rmfharvey/EE4951_REPO/Documentation/Firmware Algorithms/ADC Trigger.PNG

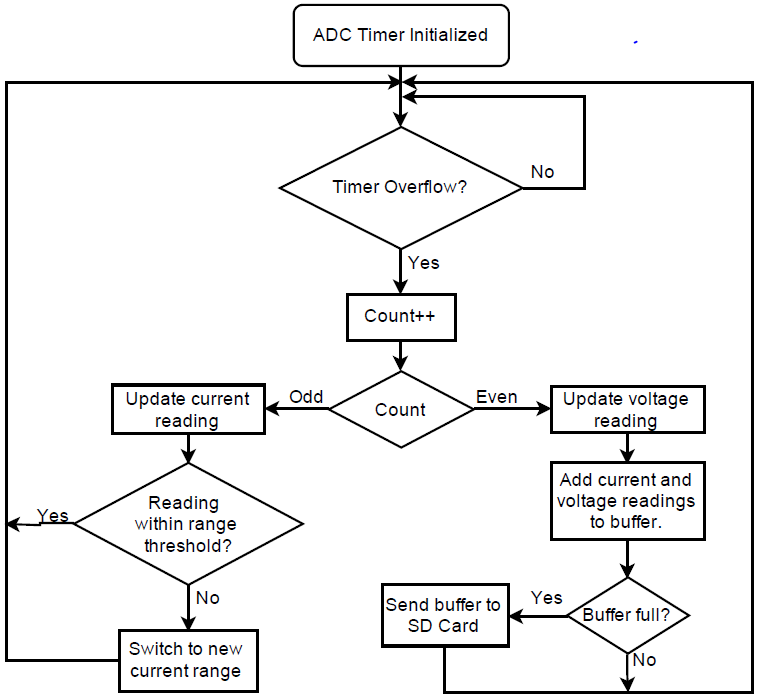
Documentation/Firmware Algorithms/ADC Trigger.PNG
