rmfharvey/EE4951_REPO/Documentation/Nimbelink Device Power Profile/Skywire Online Demo.png

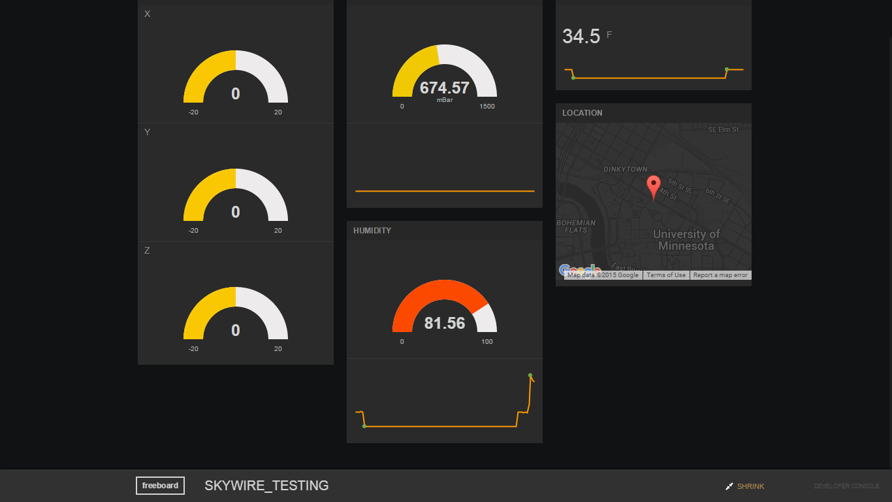
Documentation/Nimbelink Device Power Profile/Skywire Online Demo.png
