rmfharvey/EE4951_REPO/Documentation/Skywire Scope Shots/Constant Transmission.png

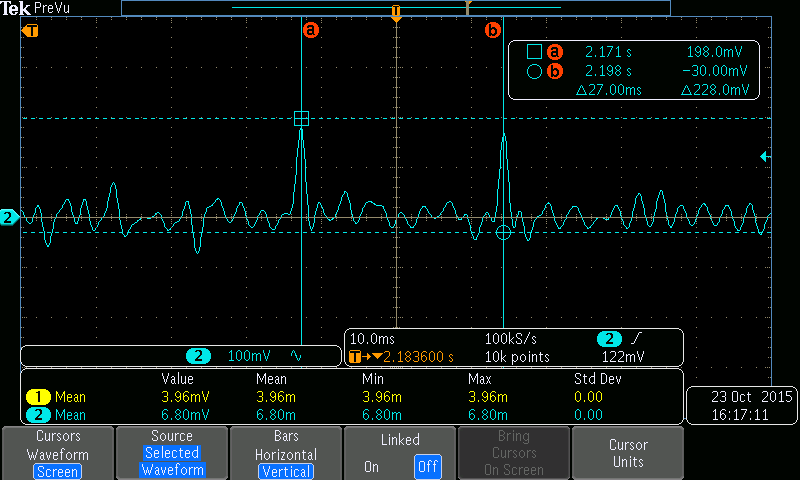
Documentation/Skywire Scope Shots/Constant Transmission.png
