rmfharvey/EE4951_REPO/Documentation/Skywire Scope Shots/Transmission Length.png

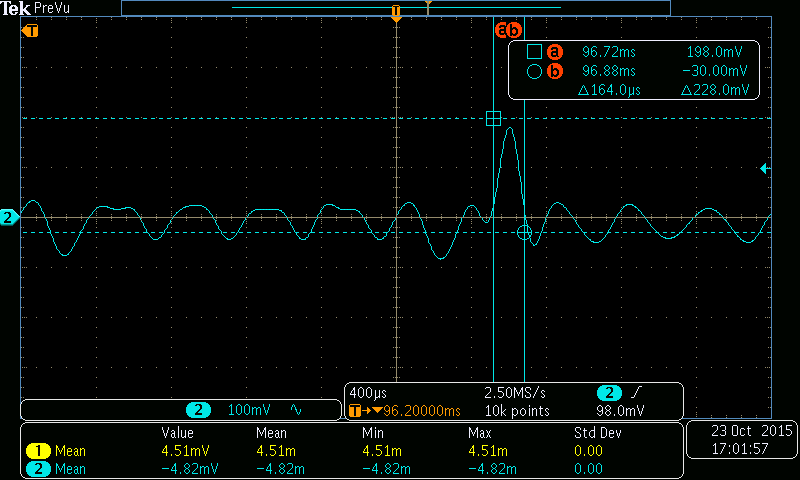
Documentation/Skywire Scope Shots/Transmission Length.png
