rmfharvey/EE4951_REPO/Simulation/Power Subsystem/Converter Selection Controls Simulation/Simulation Output/Charge Pump Auto Turn_Off.png

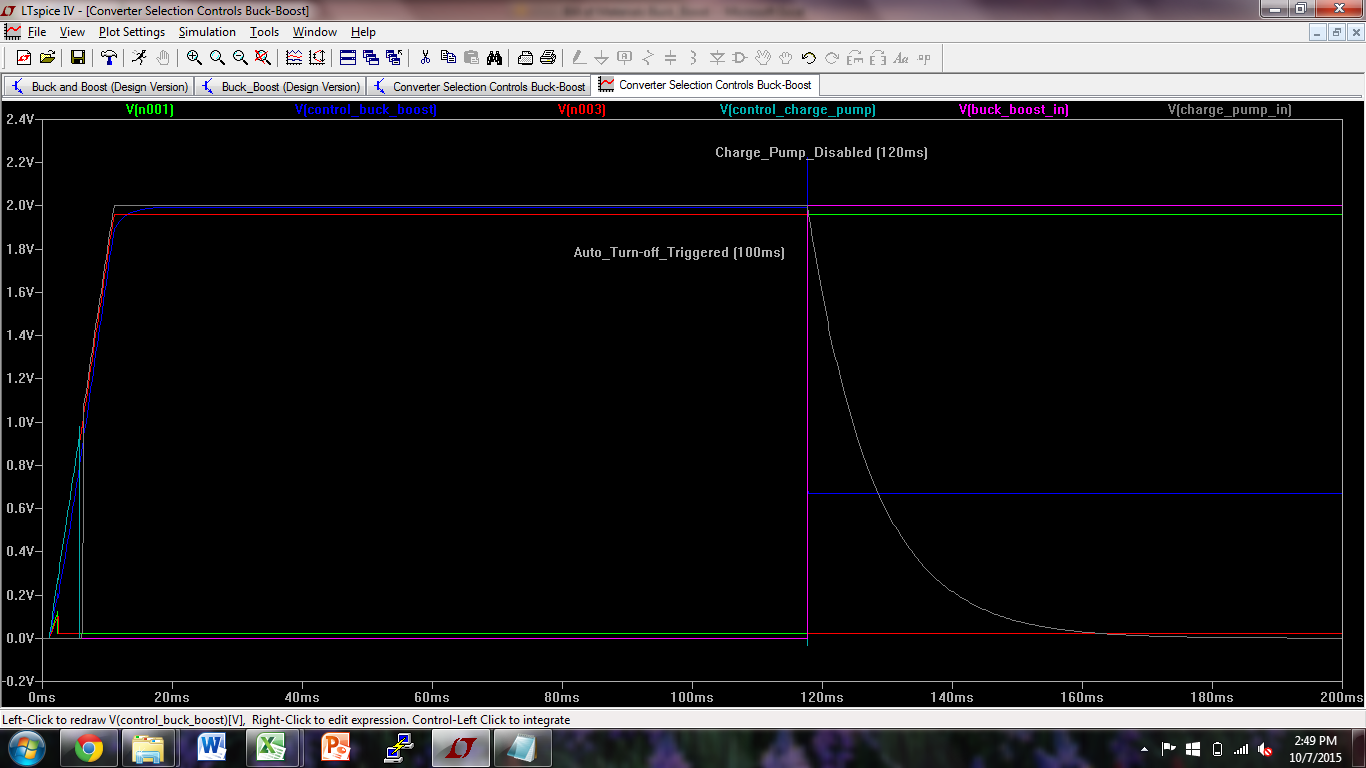
Simulation/Power Subsystem/Converter Selection Controls Simulation/Simulation Output/Charge Pump Auto Turn_Off.png
