rmfharvey/EE4951_REPO/Simulation/Power Subsystem/Converter Selection Controls Simulation/Simulation Output/Comparator and Control Signals.png

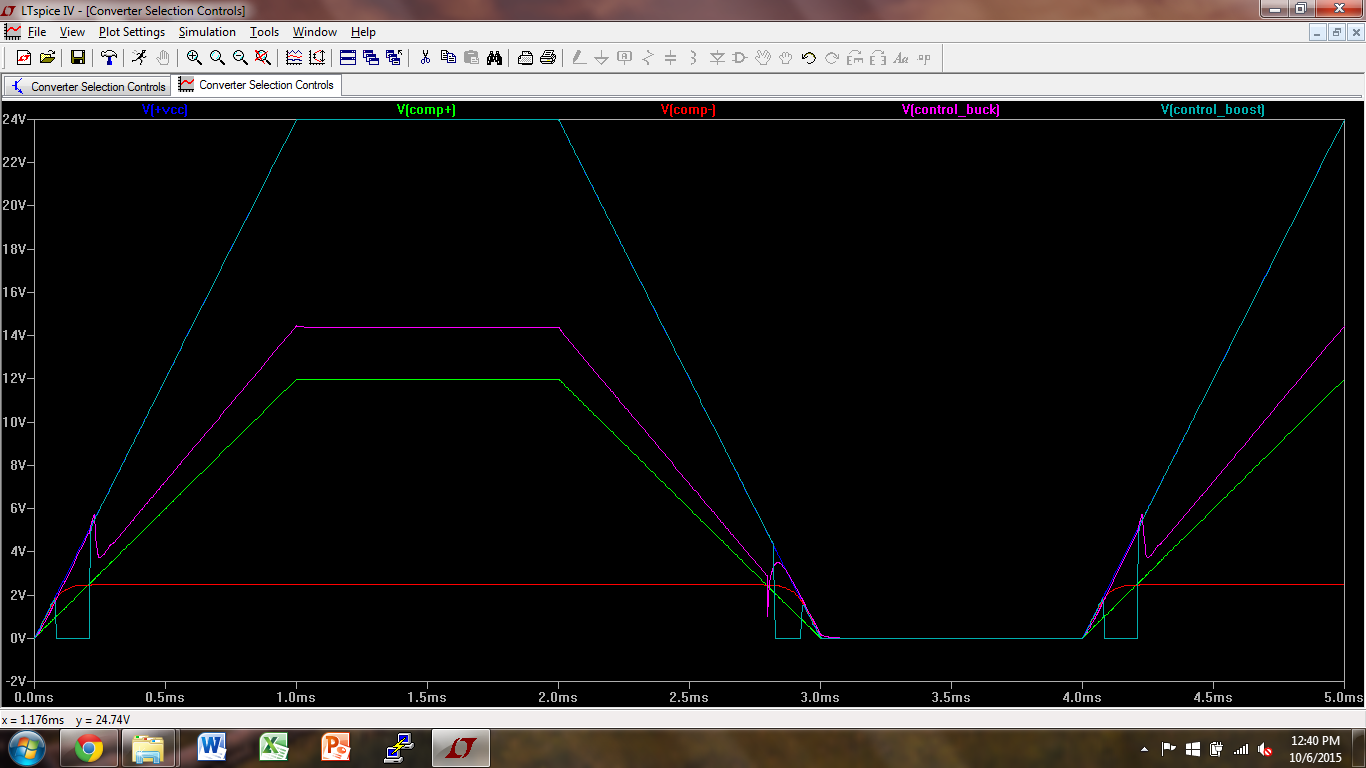
Simulation/Power Subsystem/Converter Selection Controls Simulation/Simulation Output/Comparator and Control Signals.png
