rmfharvey/EE4951_REPO/Simulation/Power Subsystem/Converter Selection Controls Simulation/Simulation Output/Converter Inputs (Assuming 10uF filter caps).png

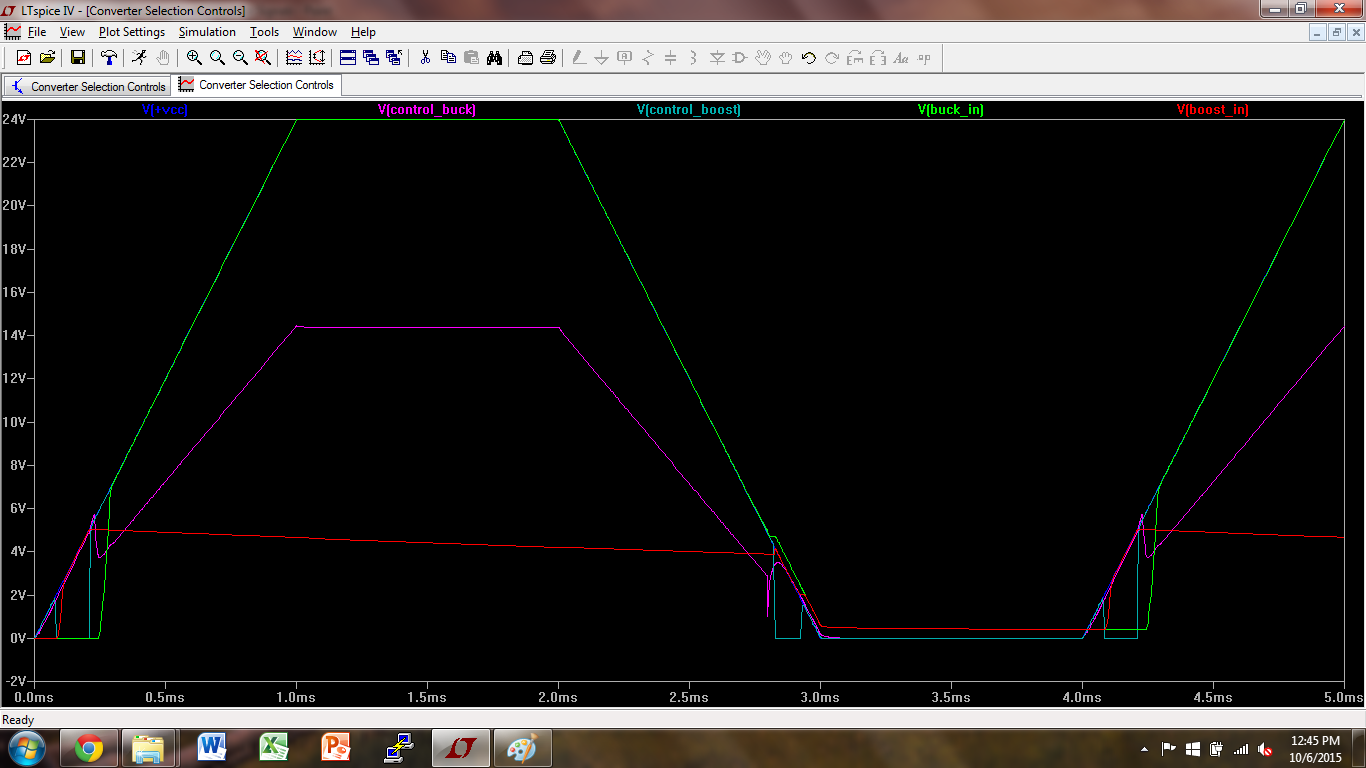
Simulation/Power Subsystem/Converter Selection Controls Simulation/Simulation Output/Converter Inputs (Assuming 10uF filter caps).png
