rmfharvey/EE4951_REPO/Simulation/Power Subsystem/Converter Selection Controls Simulation/Simulation Output/Converter Transition 4_4V to 5_6V Input.png

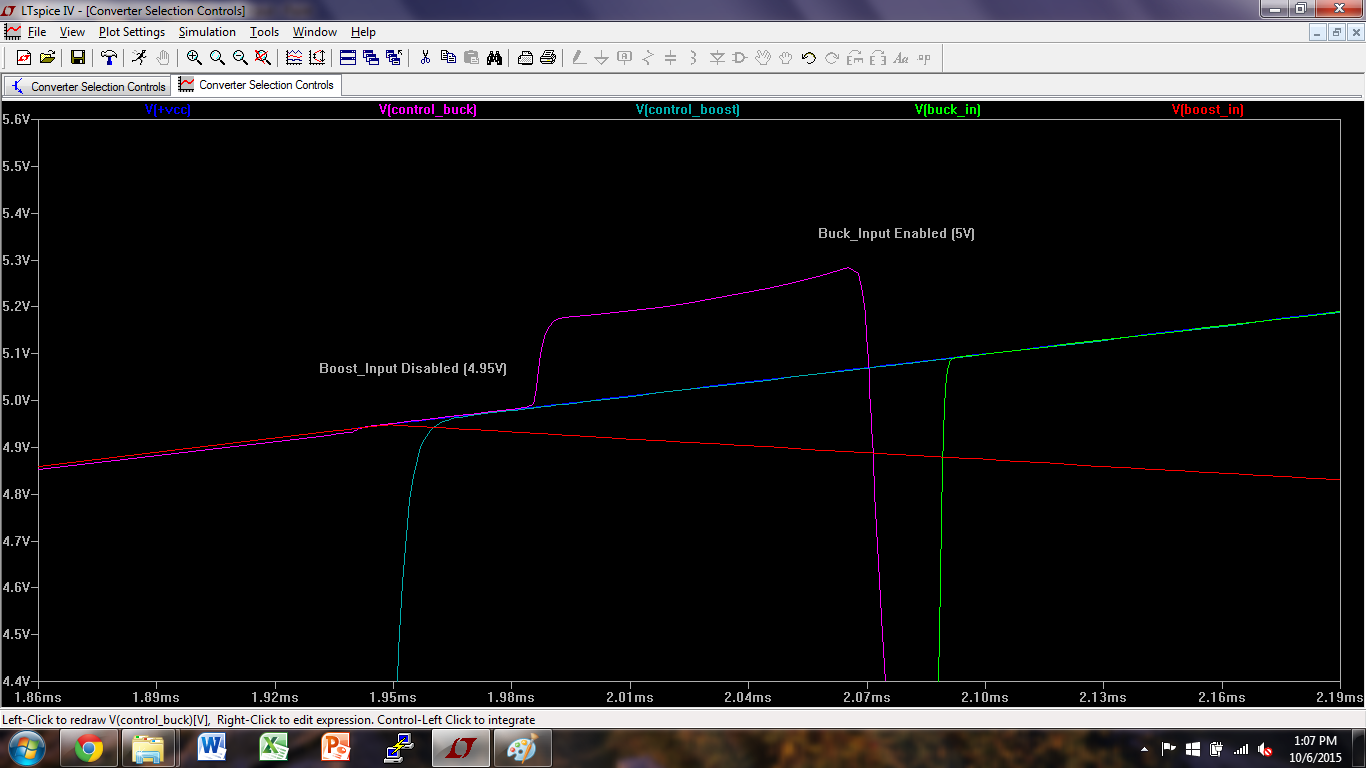
Simulation/Power Subsystem/Converter Selection Controls Simulation/Simulation Output/Converter Transition 4_4V to 5_6V Input.png
