rmfharvey/EE4951_REPO/Simulation/Power Subsystem/USB Autotransfer/Switch USB onto 4_5V.png

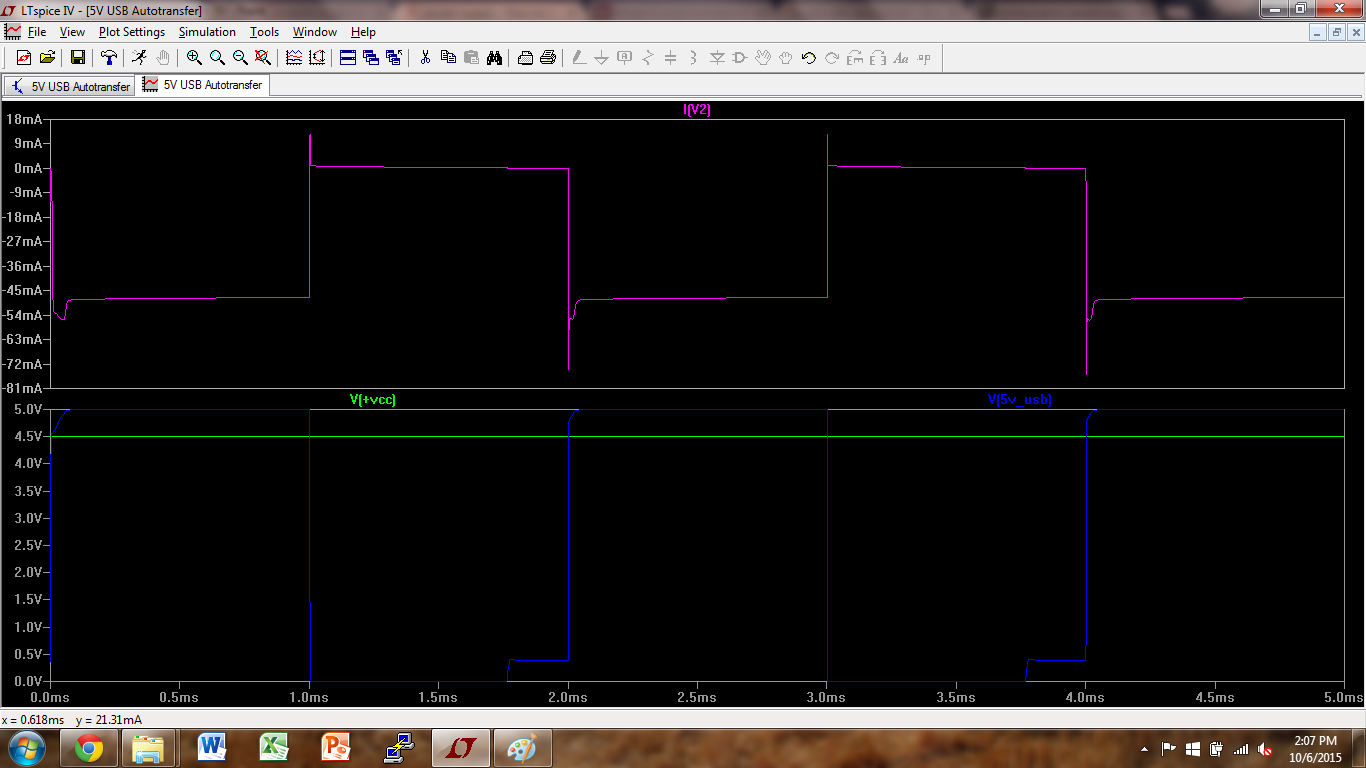
Simulation/Power Subsystem/USB Autotransfer/Switch USB onto 4_5V.png
