rmfharvey/EE4951_REPO/Simulation/Power Subsystem/USB Autotransfer/Switch USB onto 5V (Converter Current Spike).png

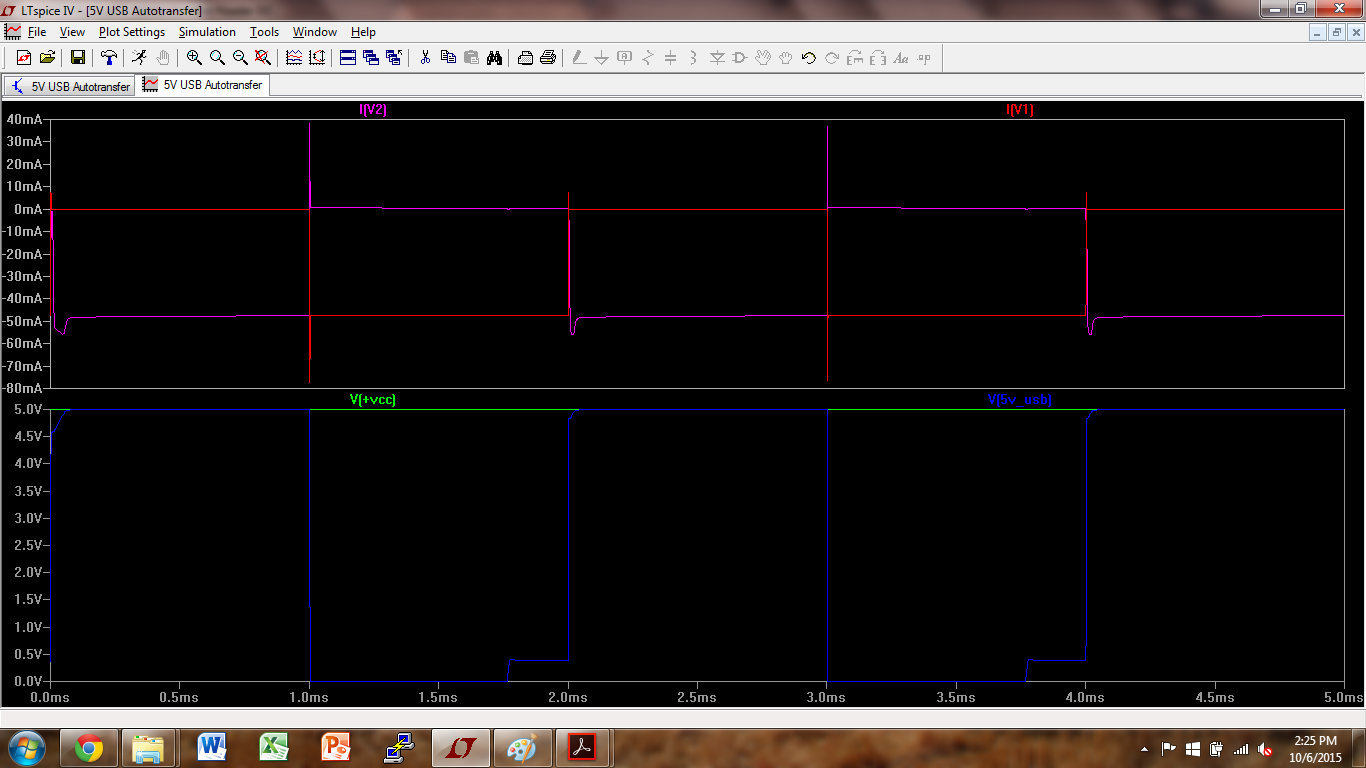
Simulation/Power Subsystem/USB Autotransfer/Switch USB onto 5V (Converter Current Spike).png
