rmfharvey/EE4951_REPO/Simulation/Power Subsystem/USB Autotransfer/Switch USB onto 5V.png

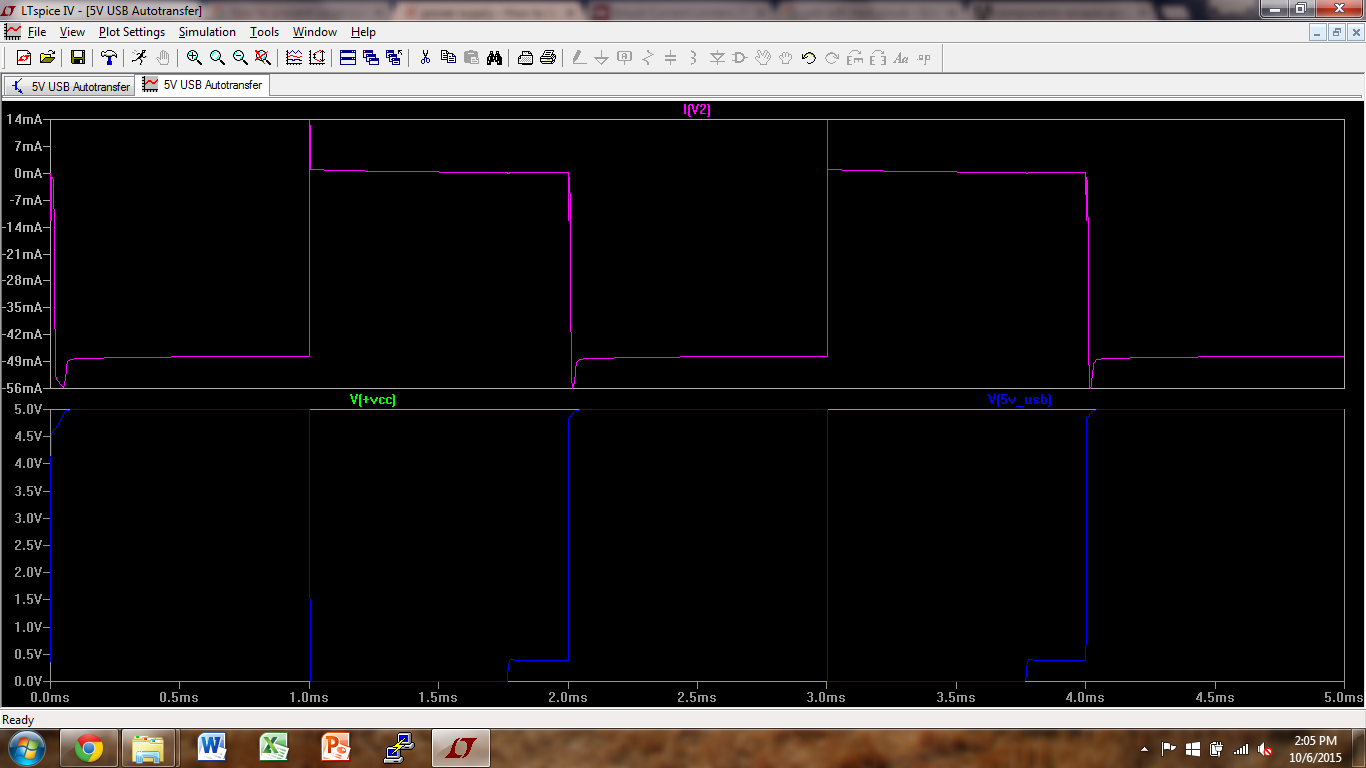
Simulation/Power Subsystem/USB Autotransfer/Switch USB onto 5V.png
