rmfharvey/EE4951_REPO/PCBA/Master_Altium_Library/3D Models/Standoff_M3x15mm.stp

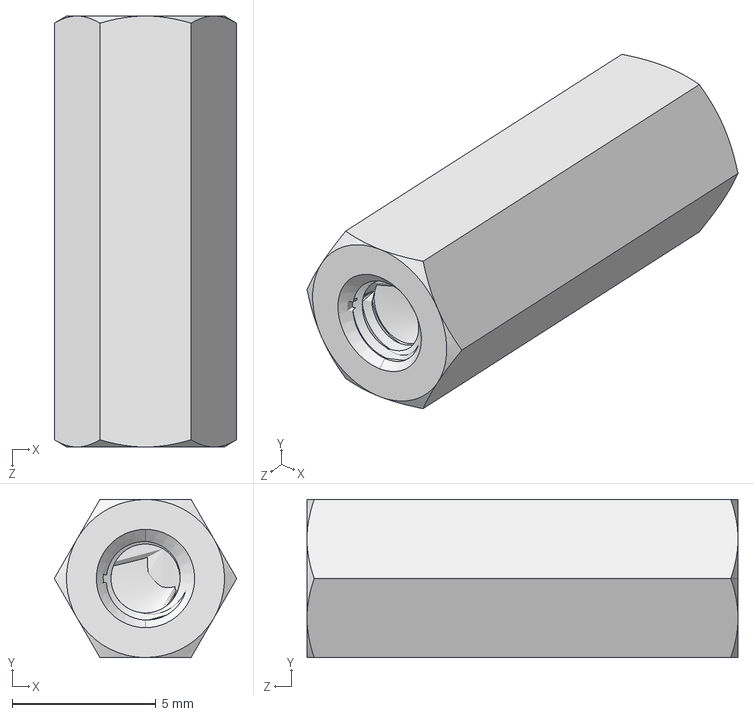
[picture p25: CAD file, 2015-10-20]
PCBA/Master_Altium_Library/3D Models/Standoff_M3x15mm.stp
6.35 x 5.50 x 15.0 mm
