rmfharvey/EE4951_REPO/PCBA/Master_Altium_Library/3D Models/QFN-32-5x5.step

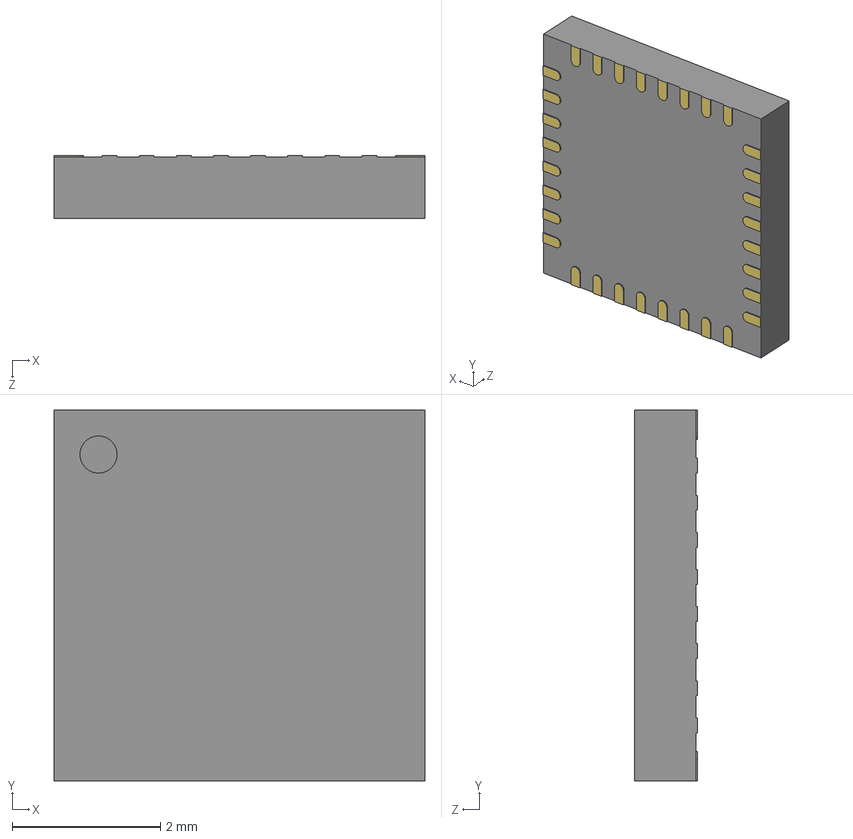
[picture p35: CAD file, 2015-10-08]
PCBA/Master_Altium_Library/3D Models/QFN-32-5x5.step
5.00 x 5.00 x 0.85 mm
