rmfharvey/EE4951_REPO/PCBA/Master_Altium_Library/3D Models/PLCC-2.STEP

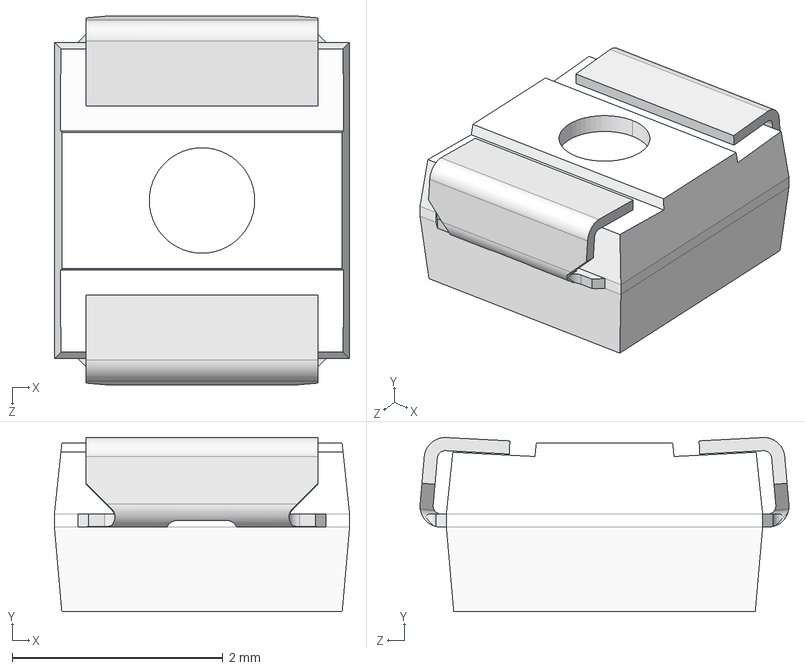
[picture p36: CAD file, 2015-10-08]
PCBA/Master_Altium_Library/3D Models/PLCC-2.STEP
2.80 x 1.65 x 3.50 mm
User Library-PLCC-2_VSMY3850_6_541-5067_1-3D
User Library-PLCC-2_VSMY3850_6_541-5067_1-3D001
User Library-PLCC-2_VSMY3850_6_541-5067_1-3D002
User Library-PLCC-2_VSMY3850_6_541-5067_1-3D003
