rmfharvey/EE4951_REPO/PCBA/Master_Altium_Library/3D Models/SMD_CAP_4x5_5.STEP

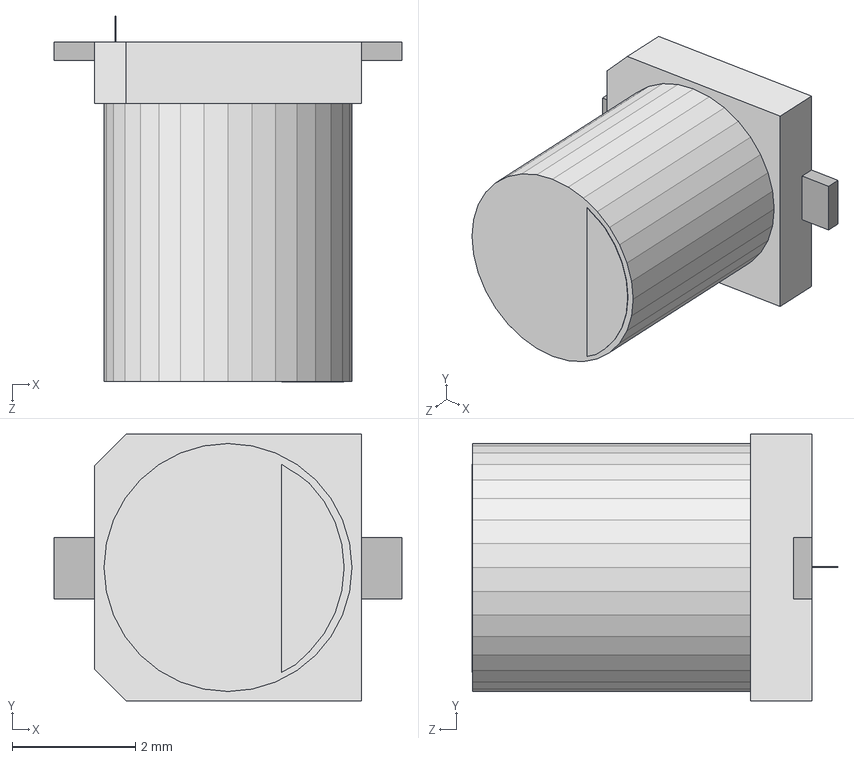
[picture p37: CAD file, 2015-10-08]
PCBA/Master_Altium_Library/3D Models/SMD_CAP_4x5_5.STEP
5.64 x 4.32 x 5.93 mm
SW3dPS-CAPSMD4x5_5_Board
SW3dPS-CAPSMD4x5_5_Extruded2 x 2
SW3dPS-CAPSMD4x5_5_Extruded3
SW3dPS-CAPSMD4x5_5_Extruded
SW3dPS-CAPSMD4x5_5_Extruded1
