rmfharvey/EE4951_REPO/PCBA/Master_Altium_Library/3D Models/MOLEX_878310820.stp

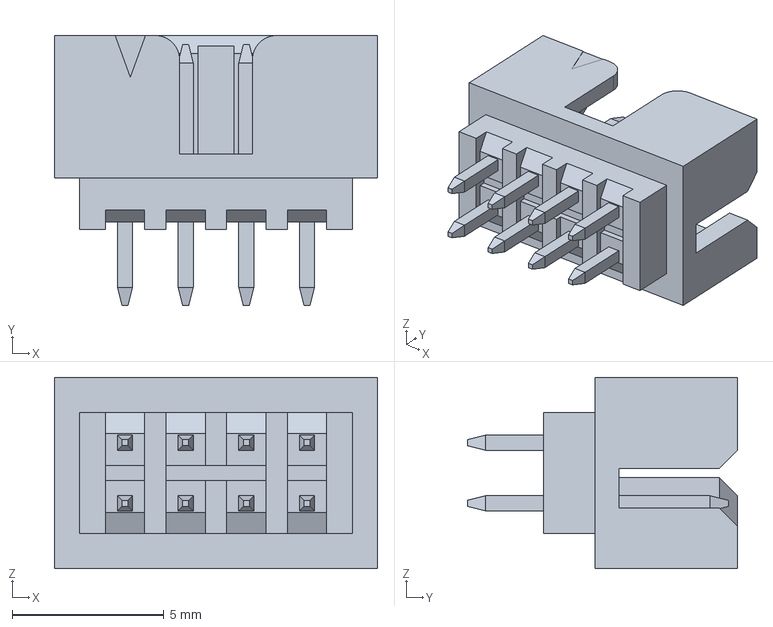
[picture p38: CAD file, 2015-10-08]
PCBA/Master_Altium_Library/3D Models/MOLEX_878310820.stp
10.7 x 8.90 x 6.30 mm
