rmfharvey/EE4951_REPO/PCBA/Master_Altium_Library/3D Models/RES0201.stp

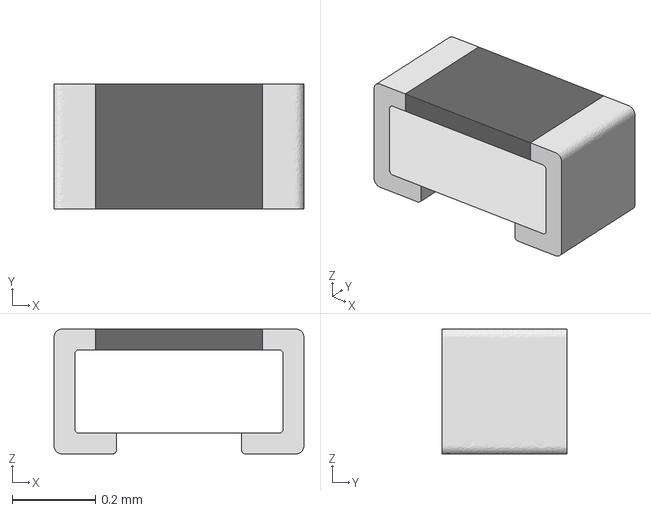
[picture p39: CAD file, 2015-10-08]
PCBA/Master_Altium_Library/3D Models/RES0201.stp
0.6 x 0.3 x 0.3 mm
