rmfharvey/EE4951_REPO/PCBA/Master_Altium_Library/3D Models/Molex 15-31-1026.stp

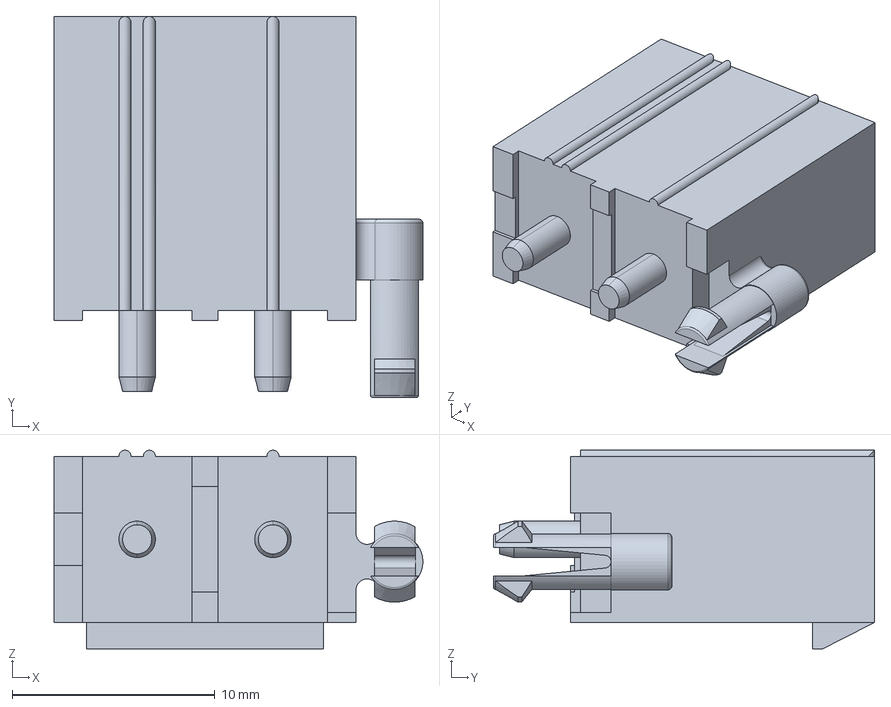
[picture p40: CAD file, 2015-10-08]
PCBA/Master_Altium_Library/3D Models/Molex 15-31-1026.stp
18.2 x 18.8 x 9.80 mm
