rmfharvey/EE4951_REPO/PCBA/Master_Altium_Library/3D Models/1x4 Header.stp

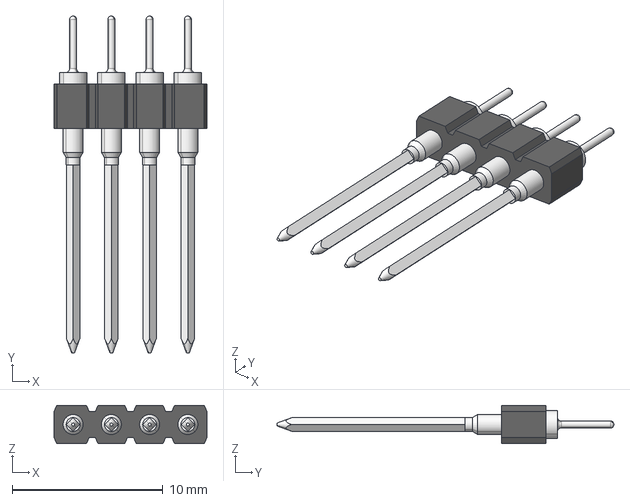
[picture p41: CAD file, 2015-10-08]
PCBA/Master_Altium_Library/3D Models/1x4 Header.stp
10.2 x 22.4 x 2.54 mm
