rmfharvey/EE4951_REPO/PCBA/Master_Altium_Library/3D Models/TSSOP14.step

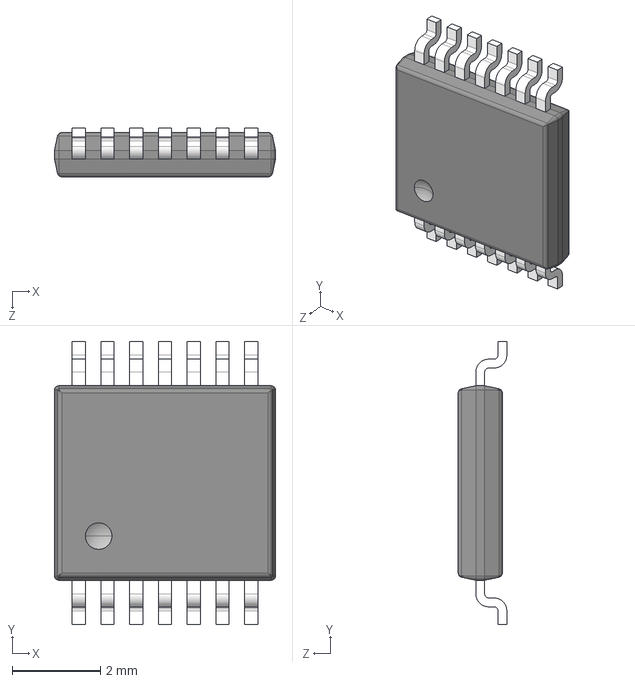
[picture p42: CAD file, 2015-10-08]
PCBA/Master_Altium_Library/3D Models/TSSOP14.step
5.00 x 6.40 x 1.10 mm
