rmfharvey/EE4951_REPO/PCBA/Master_Altium_Library/3D Models/USB_MINI_B_SMD_FEMALE.stp

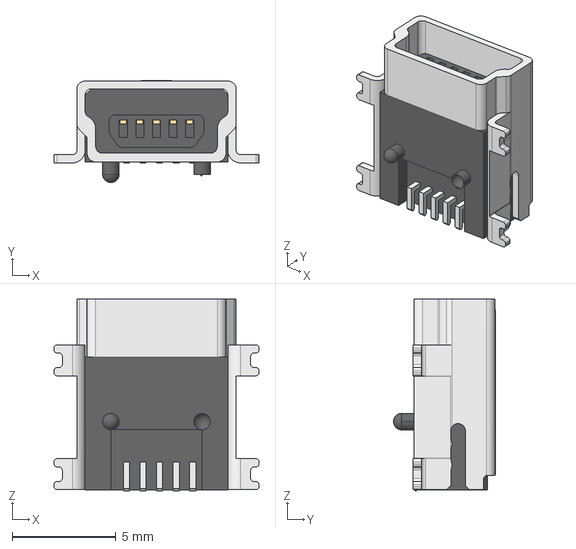
[picture p43: CAD file, 2015-10-08]
PCBA/Master_Altium_Library/3D Models/USB_MINI_B_SMD_FEMALE.stp
9.90 x 4.93 x 9.25 mm
