rmfharvey/EE4951_REPO/PCBA/Master_Altium_Library/3D Models/SOT-23-6 PITCH 0_65.STEP

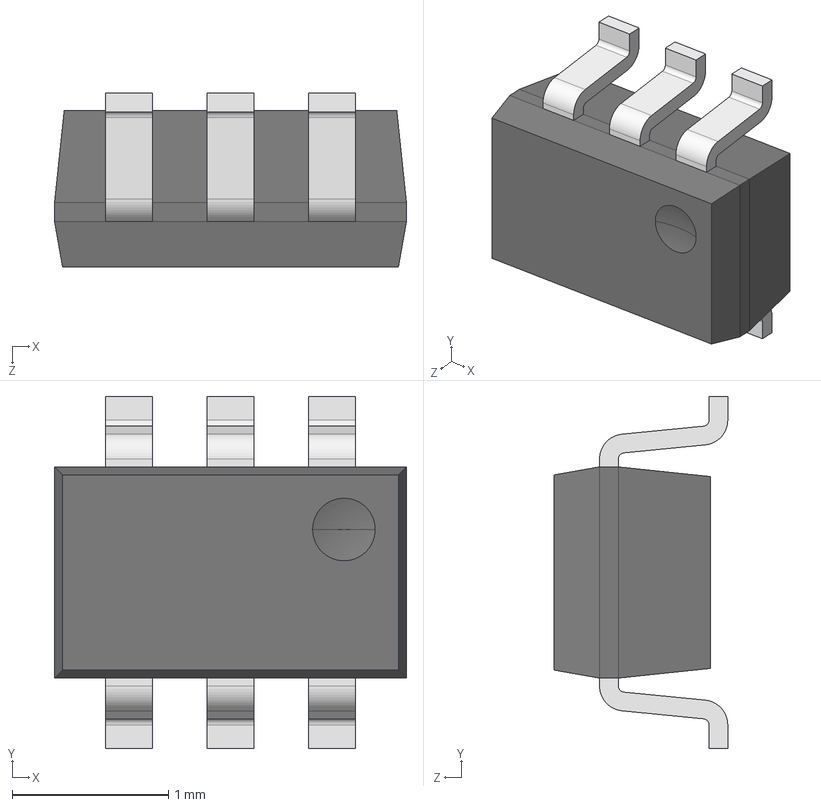
[picture p44: CAD file, 2015-10-08]
PCBA/Master_Altium_Library/3D Models/SOT-23-6 PITCH 0_65.STEP
2.25 x 2.25 x 1.11 mm
User Library-TSSOP-6 (SOT-23-6 PITCH 0.65)_pin_TSSOP_tssop6_1 x 6
User Library-TSSOP-6 (SOT-23-6 PITCH 0.65)_body_TSSOP-6_TSSOP5_1
