rmfharvey/EE4951_REPO/PCBA/Master_Altium_Library/3D Models/SOIC10 narrow.stp

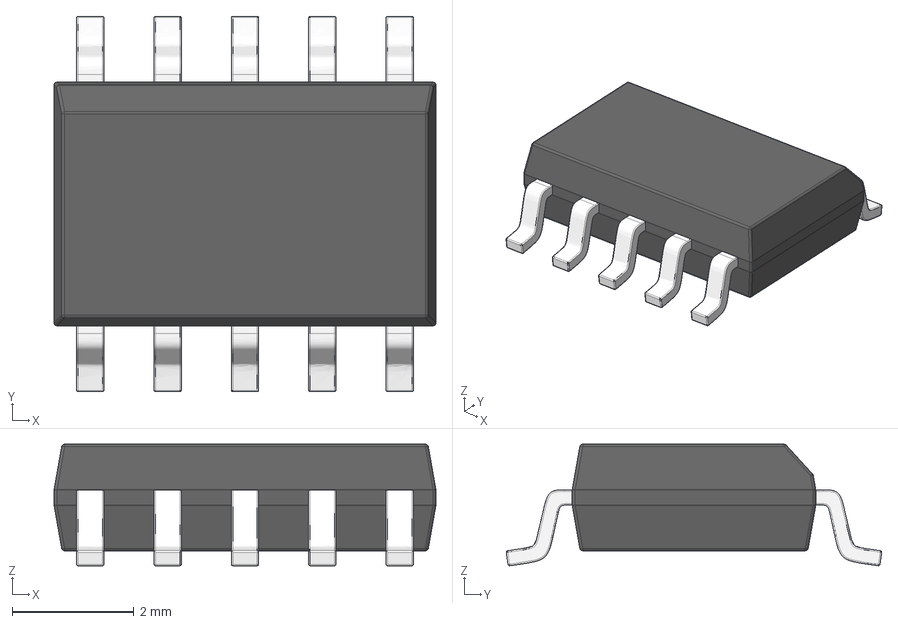
[picture p45: CAD file, 2015-10-08]
PCBA/Master_Altium_Library/3D Models/SOIC10 narrow.stp
6.27 x 6.16 x 2.00 mm
