rmfharvey/EE4951_REPO/PCBA/Master_Altium_Library/3D Models/CAP2220.stp

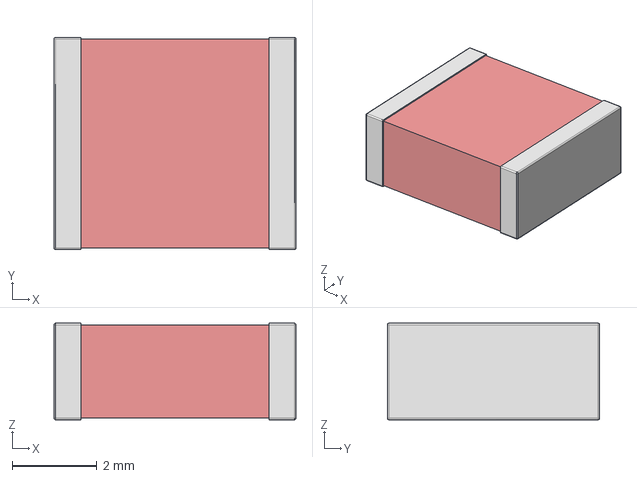
[picture p46: CAD file, 2015-10-08]
PCBA/Master_Altium_Library/3D Models/CAP2220.stp
5.70 x 5.00 x 2.28 mm
