rmfharvey/EE4951_REPO/PCBA/Master_Altium_Library/3D Models/1x4 PicoBlade.stp

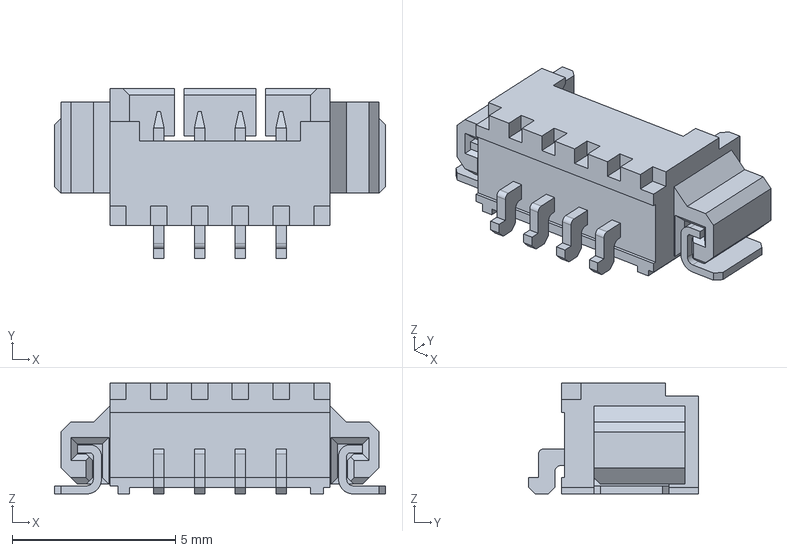
[picture p47: CAD file, 2015-10-08]
PCBA/Master_Altium_Library/3D Models/1x4 PicoBlade.stp
10.2 x 5.20 x 3.40 mm
