rmfharvey/EE4951_REPO/PCBA/Master_Altium_Library/3D Models/SRR1260-680M.step

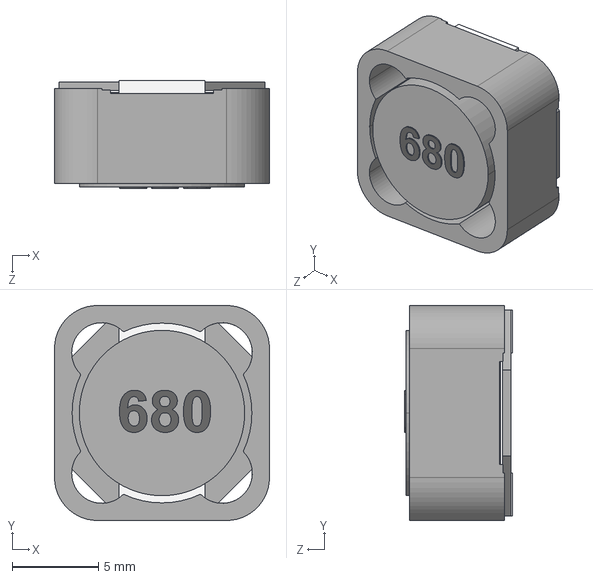
[picture p48: CAD file, 2015-10-08]
PCBA/Master_Altium_Library/3D Models/SRR1260-680M.step
12.5 x 12.5 x 6.29 mm
