rmfharvey/EE4951_REPO/PCBA/Master_Altium_Library/3D Models/BGA121C65P11X11_800X800X143_JEDEC_MO-275-CCBE-1_Freescale_MAPBGA_121 (2).STEP

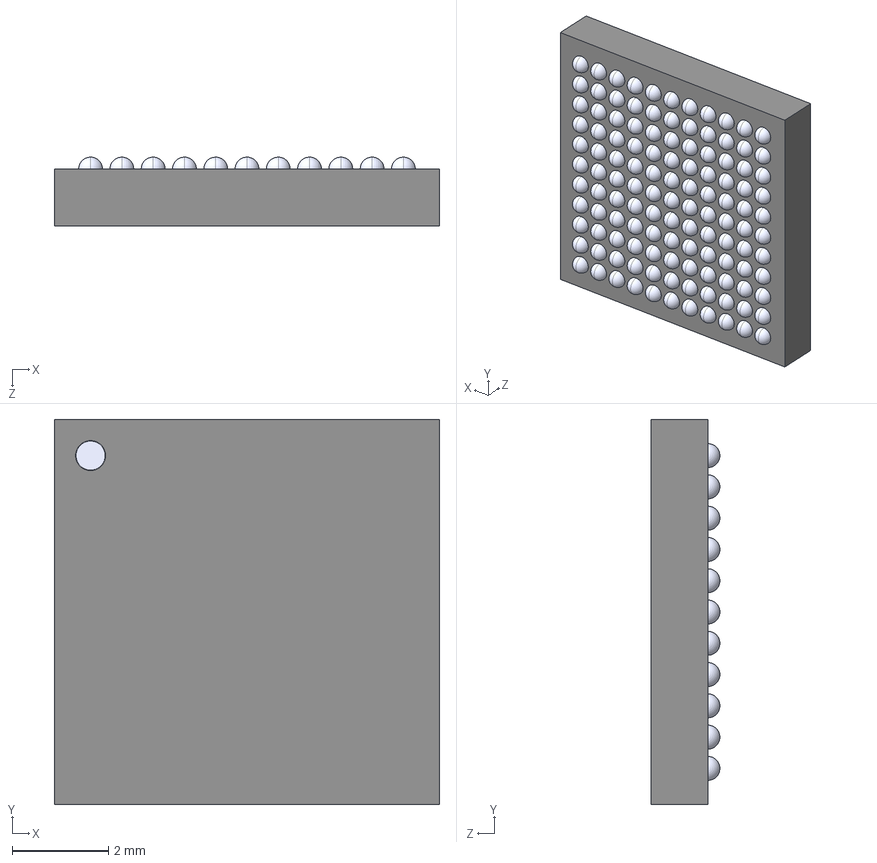
[picture p49: CAD file, 2015-10-08]
PCBA/Master_Altium_Library/3D Models/BGA121C65P11X11_800X800X143_JEDEC_MO-275-CCBE-1_Freescale_MAPBGA_121 (2).STEP
8.00 x 8.00 x 1.43 mm
