rmfharvey/EE4951_REPO/PCBA/Master_Altium_Library/3D Models/DO-214AC SMA.step

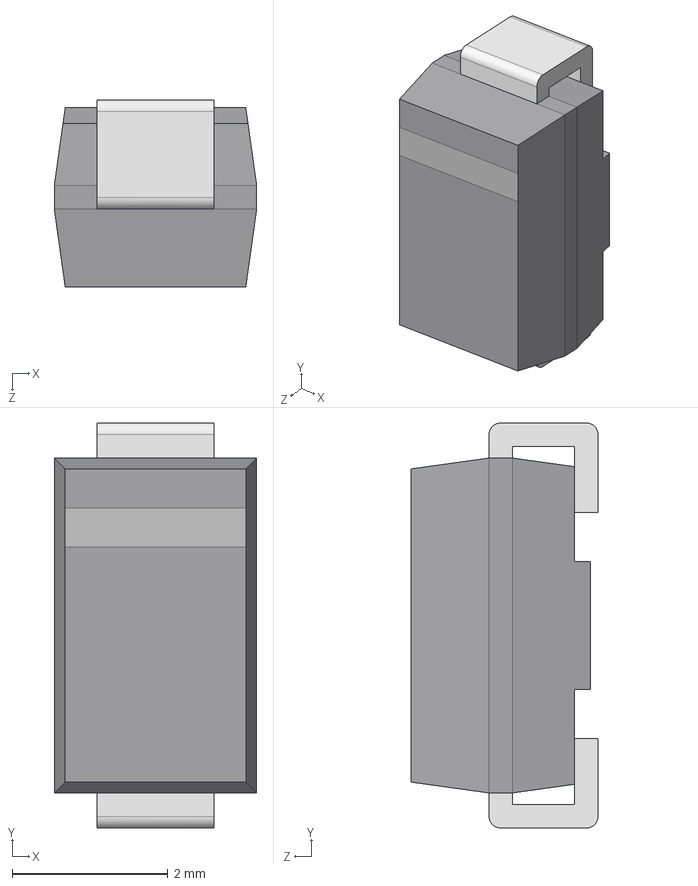
[picture p50: CAD file, 2015-10-08]
PCBA/Master_Altium_Library/3D Models/DO-214AC SMA.step
2.60 x 5.20 x 2.40 mm
