rmfharvey/EE4951_REPO/PCBA/Master_Altium_Library/3D Models/SOD-123FL.STEP

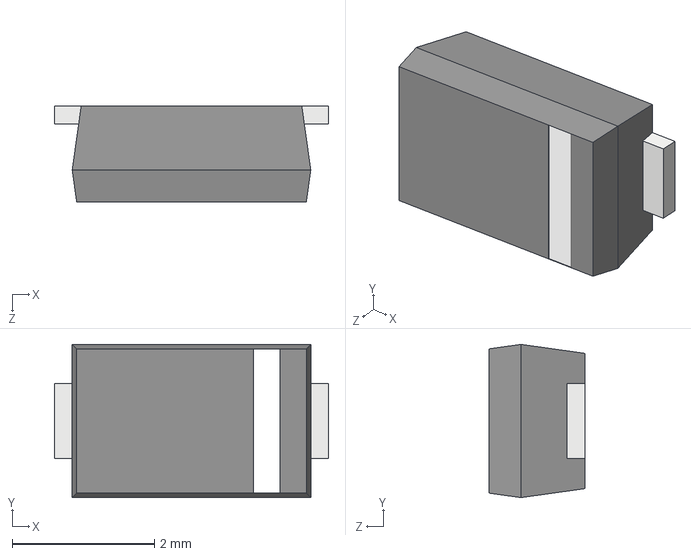
[picture p51: CAD file, 2015-10-08]
PCBA/Master_Altium_Library/3D Models/SOD-123FL.STEP
3.85 x 2.15 x 1.35 mm
