rmfharvey/EE4951_REPO/PCBA/Master_Altium_Library/3D Models/DPAK_TO-252AA.step

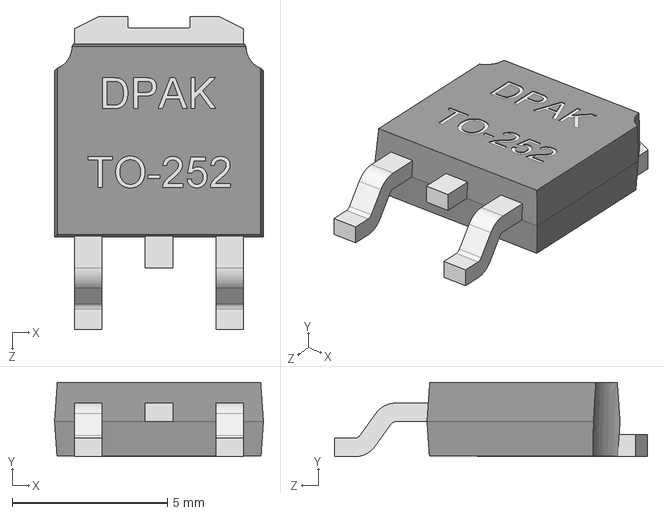
[picture p52: CAD file, 2015-10-08]
PCBA/Master_Altium_Library/3D Models/DPAK_TO-252AA.step
6.73 x 2.40 x 10.1 mm
