rmfharvey/EE4951_REPO/PCBA/Master_Altium_Library/3D Models/P-TO263-15-1.STEP

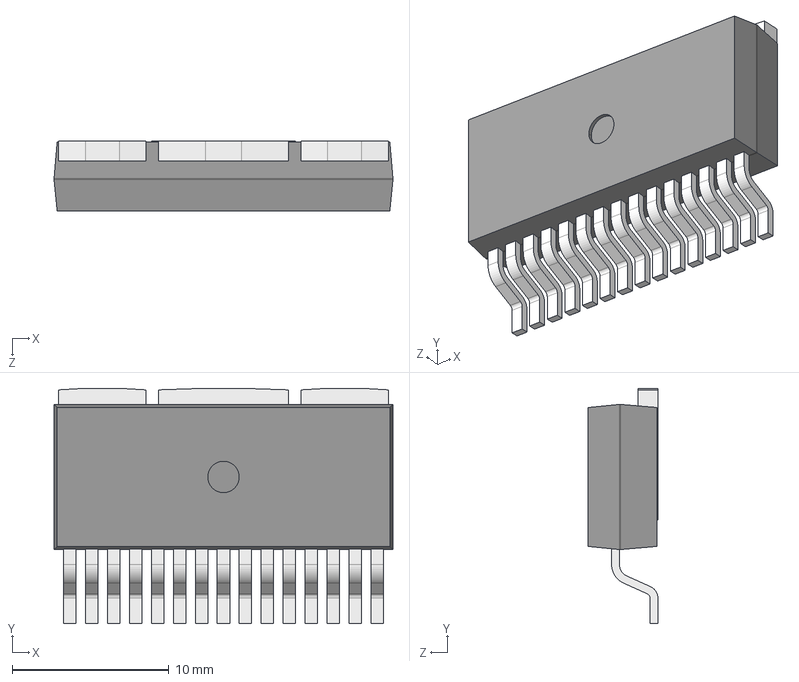
[picture p53: CAD file, 2015-10-08]
PCBA/Master_Altium_Library/3D Models/P-TO263-15-1.STEP
21.6 x 15.0 x 4.45 mm
SW3dPS-P-TO263-15-1_Part_1303
SW3dPS-P-TO263-15-1_Part_1535
SW3dPS-P-TO263-15-1_Part_996
SW3dPS-P-TO263-15-1_Part_1655
SW3dPS-P-TO263-15-1_Part_557
SW3dPS-P-TO263-15-1_Part_1075
SW3dPS-P-TO263-15-1_Part_1575
SW3dPS-P-TO263-15-1_Part_1151
SW3dPS-P-TO263-15-1_Part_1735
SW3dPS-P-TO263-15-1_Part_98
SW3dPS-P-TO263-15-1_Part_1379
SW3dPS-P-TO263-15-1_Part_59
SW3dPS-P-TO263-15-1_Part_1775
SW3dPS-P-TO263-15-1_Part_1695
SW3dPS-P-TO263-15-1_Part_1531
SW3dPS-P-TO263-15-1_Part_1227
SW3dPS-P-TO263-15-1_Part_1455
SW3dPS-P-TO263-15-1_Part_113
SW3dPS-P-TO263-15-1_Part_1615
