rmfharvey/EE4951_REPO/PCBA/Master_Altium_Library/3D Models/SOIC-8 Narrow.step

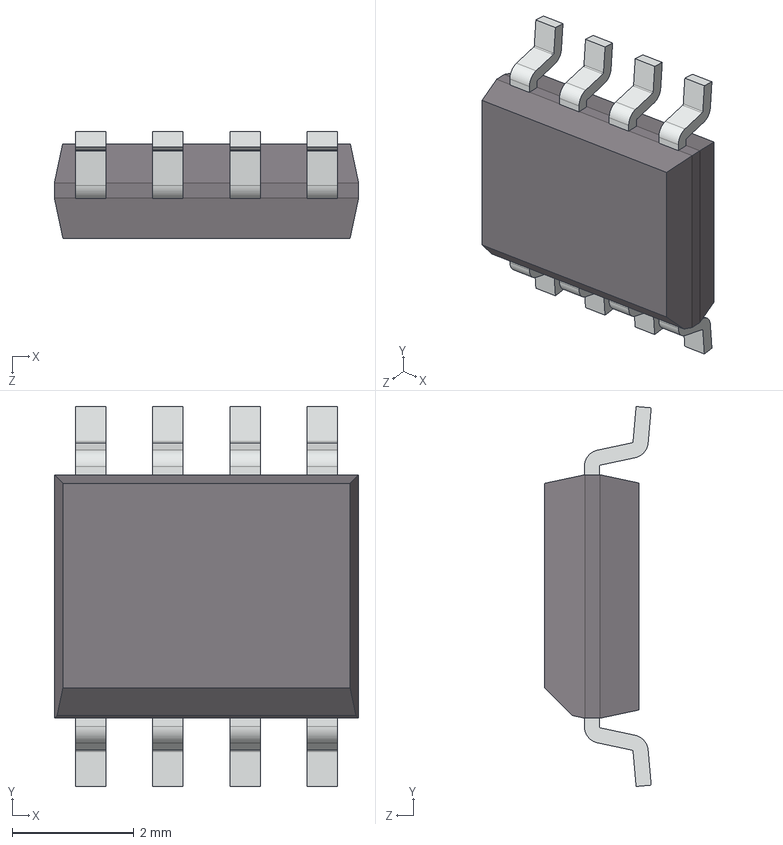
[picture p54: CAD file, 2015-10-08]
PCBA/Master_Altium_Library/3D Models/SOIC-8 Narrow.step
5.00 x 6.24 x 1.75 mm
