rmfharvey/EE4951_REPO/PCBA/Master_Altium_Library/3D Models/d2pak7_ST.STEP

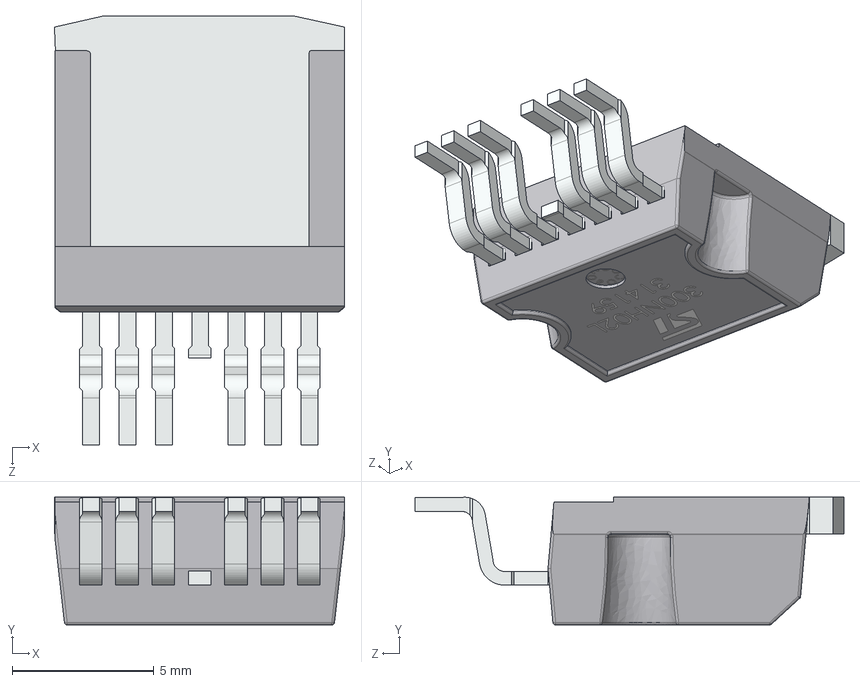
[picture p55: CAD file, 2015-10-08]
PCBA/Master_Altium_Library/3D Models/d2pak7_ST.STEP
10.2 x 4.50 x 15.1 mm
