rmfharvey/EE4951_REPO/PCBA/Master_Altium_Library/3D Models/TSDSON-8.step

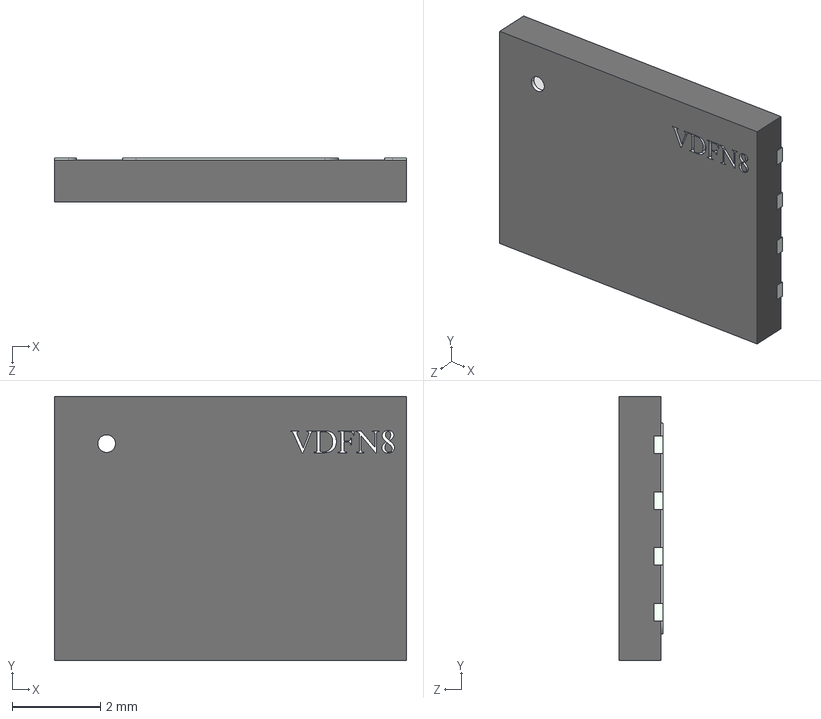
[picture p56: CAD file, 2015-10-08]
PCBA/Master_Altium_Library/3D Models/TSDSON-8.step
8.00 x 6.00 x 1.00 mm
