rmfharvey/EE4951_REPO/PCBA/Master_Altium_Library/3D Models/PowerPAK_SO8.step

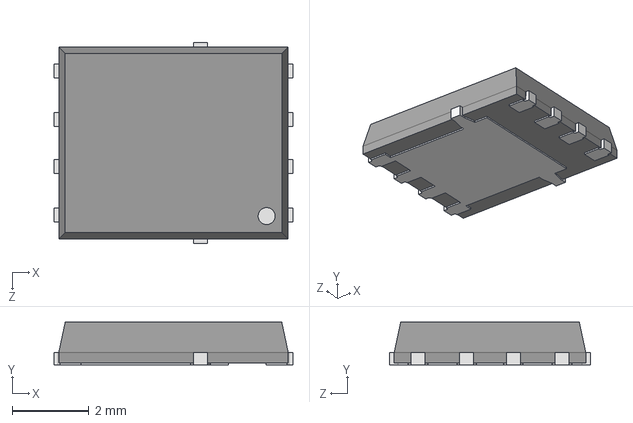
[picture p57: CAD file, 2015-10-08]
PCBA/Master_Altium_Library/3D Models/PowerPAK_SO8.step
6.24 x 1.12 x 5.25 mm
