rmfharvey/EE4951_REPO/PCBA/Master_Altium_Library/3D Models/CAP1825.stp

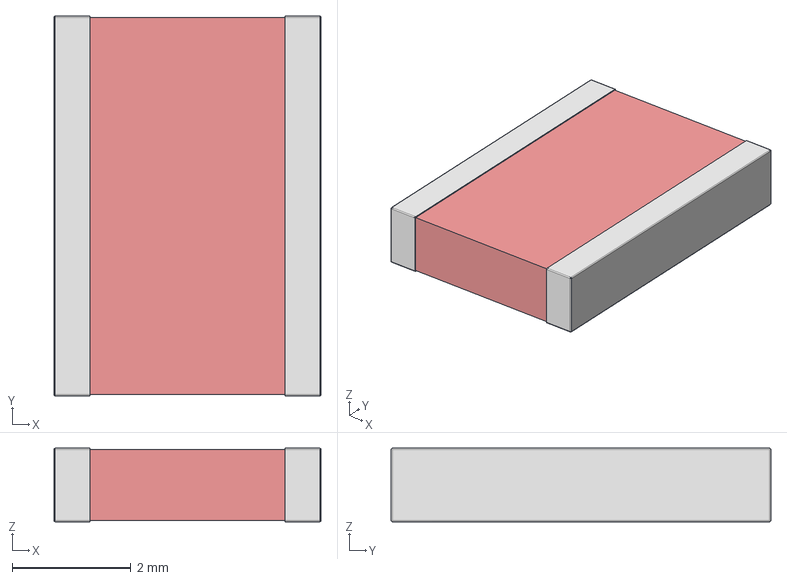
[picture p58: CAD file, 2015-10-08]
PCBA/Master_Altium_Library/3D Models/CAP1825.stp
4.50 x 6.40 x 1.24 mm
