rmfharvey/EE4951_REPO/PCBA/Master_Altium_Library/3D Models/Vertical USB-B.stp

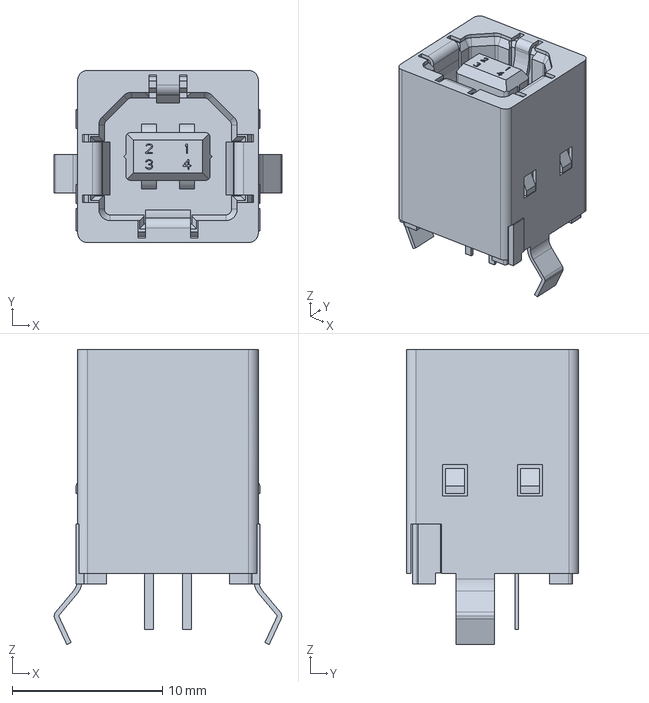
[picture p59: CAD file, 2015-10-08]
PCBA/Master_Altium_Library/3D Models/Vertical USB-B.stp
15.2 x 11.5 x 19.6 mm
