rmfharvey/EE4951_REPO/PCBA/Master_Altium_Library/3D Models/CTS 204-211.step

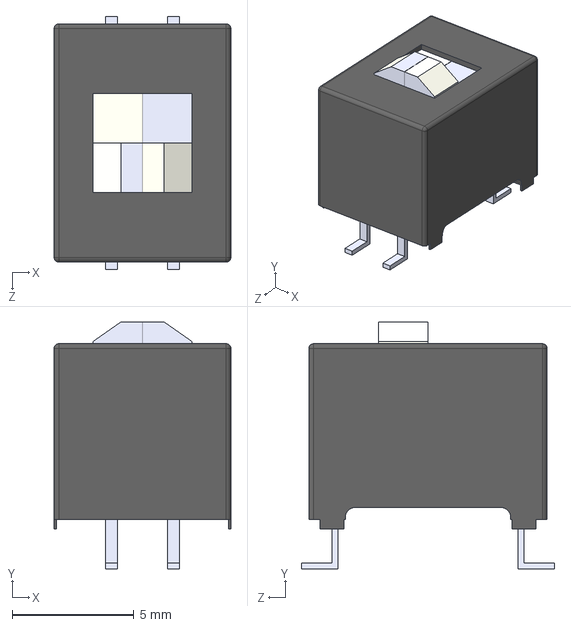
[picture p60: CAD file, 2015-10-08]
PCBA/Master_Altium_Library/3D Models/CTS 204-211.step
7.26 x 10.1 x 10.4 mm
