rmfharvey/EE4951_REPO/PCBA/Master_Altium_Library/3D Models/TO263-5.STEP

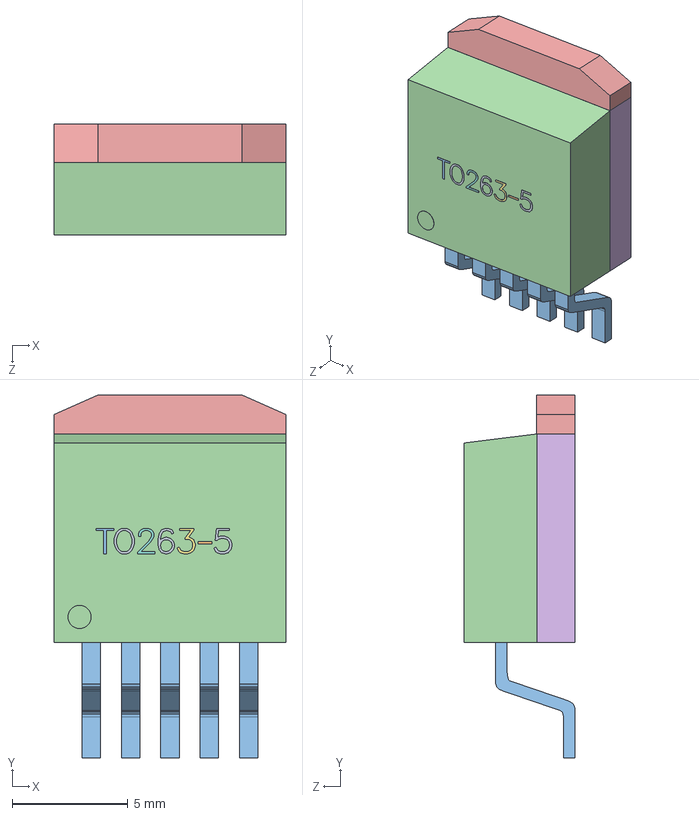
[picture p61: CAD file, 2015-10-08]
PCBA/Master_Altium_Library/3D Models/TO263-5.STEP
10.0 x 15.7 x 4.80 mm
SW3dPS-TO263-5_Board6
SW3dPS-TO263-5_Board7 x 5
SW3dPS-TO263-5_Extruded13 x 5
SW3dPS-TO263-5_Board5
SW3dPS-TO263-5_Extruded18
SW3dPS-TO263-5_Board9
SW3dPS-TO263-5_Extruded20
SW3dPS-TO263-5_Extruded14
SW3dPS-TO263-5_Board8
SW3dPS-TO263-5_Extruded15
SW3dPS-TO263-5_Extruded16
SW3dPS-TO263-5_Extruded17
SW3dPS-TO263-5_Extruded12
SW3dPS-TO263-5_Extruded21
SW3dPS-TO263-5_Extruded19
SW3dPS-TO263-5_Cylinder1
SW3dPS-TO263-5_Extruded11
