rmfharvey/EE4951_REPO/PCBA/Master_Altium_Library/3D Models/TSSOP16.step

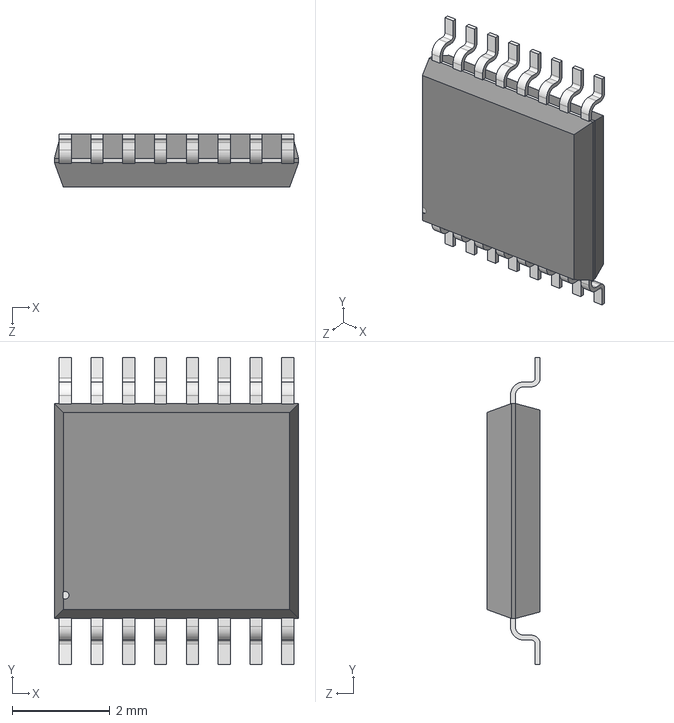
[picture p62: CAD file, 2015-10-08]
PCBA/Master_Altium_Library/3D Models/TSSOP16.step
5.00 x 6.28 x 1.09 mm
