rmfharvey/EE4951_REPO/PCBA/Master_Altium_Library/3D Models/2x5 Header JTAG.step

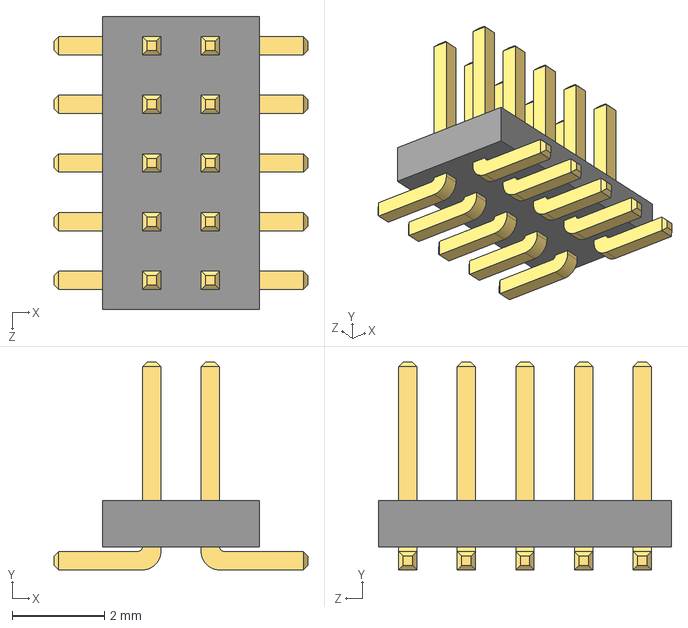
[picture p63: CAD file, 2015-10-08]
PCBA/Master_Altium_Library/3D Models/2x5 Header JTAG.step
5.50 x 4.50 x 6.35 mm
