rmfharvey/EE4951_REPO/PCBA/Master_Altium_Library/3D Models/SOT-223-6.step

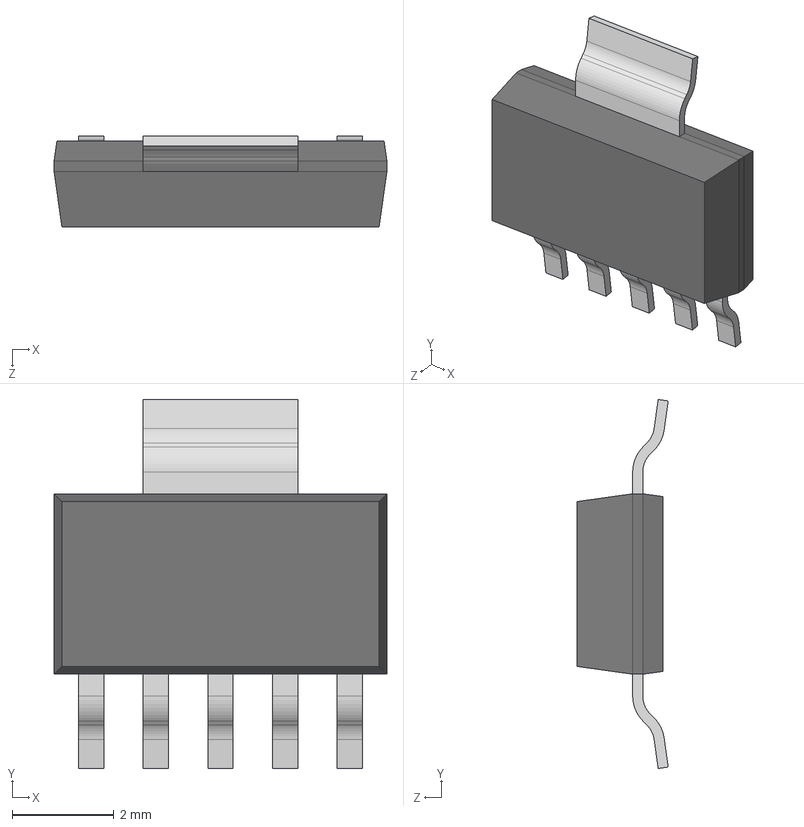
[picture p64: CAD file, 2015-10-08]
PCBA/Master_Altium_Library/3D Models/SOT-223-6.step
6.55 x 7.26 x 1.80 mm
