rmfharvey/EE4951_REPO/PCBA/Master_Altium_Library/3D Models/8pin Friction Lock.stp

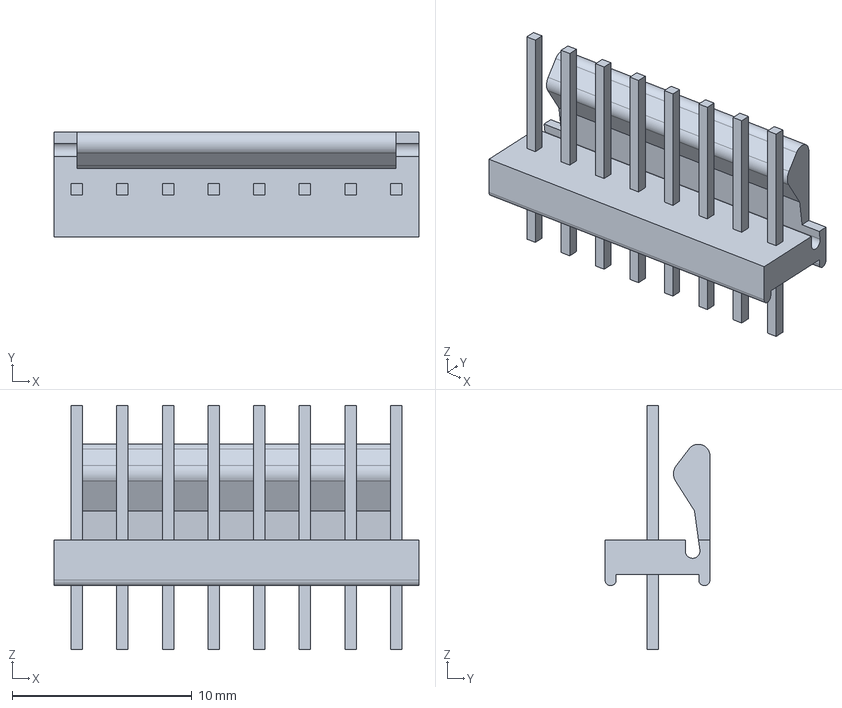
[picture p65: CAD file, 2015-10-08]
PCBA/Master_Altium_Library/3D Models/8pin Friction Lock.stp
20.3 x 5.84 x 13.6 mm
