rmfharvey/EE4951_REPO/PCBA/Master_Altium_Library/3D Models/SOIC16.step

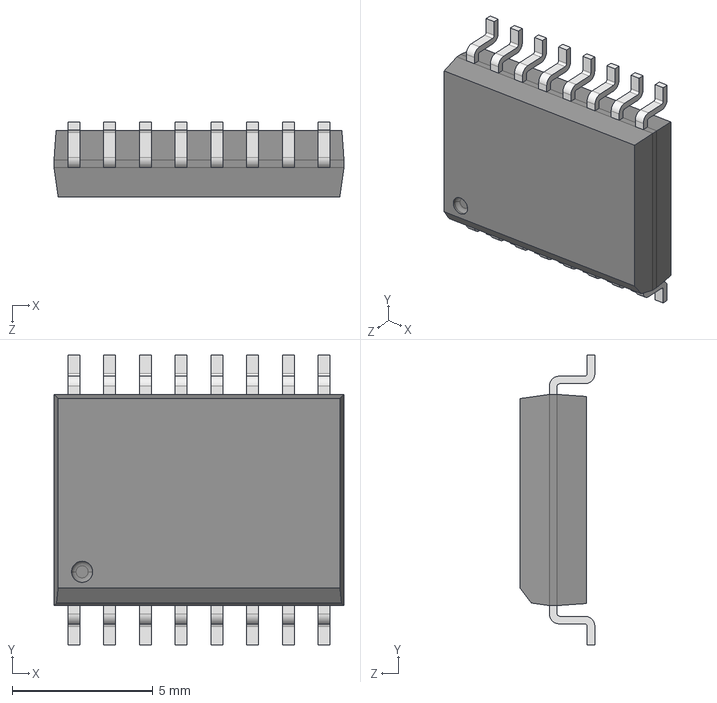
[picture p66: CAD file, 2015-10-08]
PCBA/Master_Altium_Library/3D Models/SOIC16.step
10.3 x 10.3 x 2.65 mm
