rmfharvey/EE4951_REPO/PCBA/Master_Altium_Library/3D Models/SOT-223-4.STEP

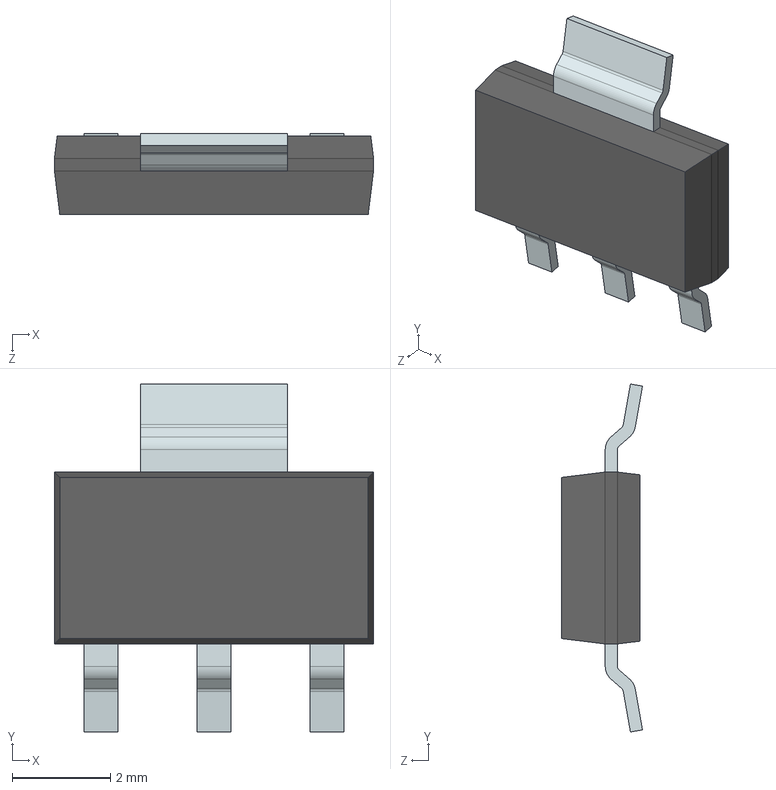
[picture p67: CAD file, 2015-10-08]
PCBA/Master_Altium_Library/3D Models/SOT-223-4.STEP
6.50 x 7.09 x 1.65 mm
User Library-SOT-223-4_SOT-223 Body
User Library-SOT-223-4_SOT-223 Foot_1 x 3
User Library-SOT-223-4_SOT-223 Foot_2
