rmfharvey/EE4951_REPO/PCBA/Master_Altium_Library/3D Models/RES2010.stp

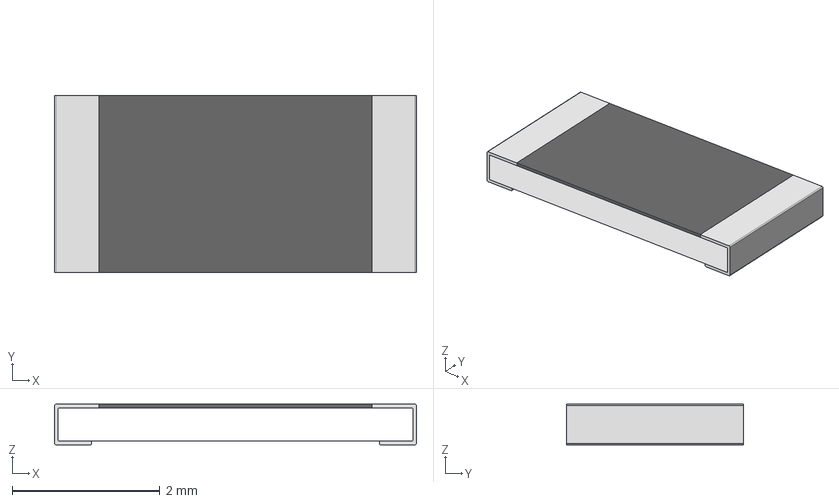
[picture p68: CAD file, 2015-10-08]
PCBA/Master_Altium_Library/3D Models/RES2010.stp
4.90 x 2.40 x 0.55 mm
