rmfharvey/EE4951_REPO/PCBA/Master_Altium_Library/3D Models/Fuse_Holder.STEP

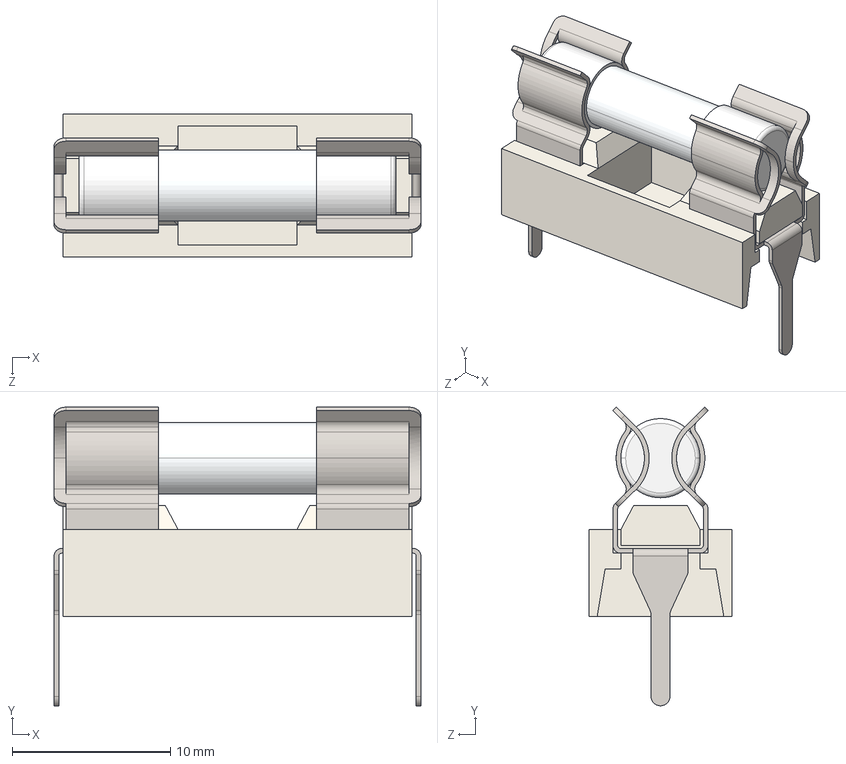
[picture p69: CAD file, 2015-10-08]
PCBA/Master_Altium_Library/3D Models/Fuse_Holder.STEP
23.2 x 18.8 x 9.00 mm
User Library-Fuse_Holder_Body_Domyslna
User Library-Fuse_Holder_pin_Domyslna x 2
User Library-Fuse_Holder_Fuse_Domyslna
