rmfharvey/EE4951_REPO/PCBA/Master_Altium_Library/3D Models/CAP2225.stp

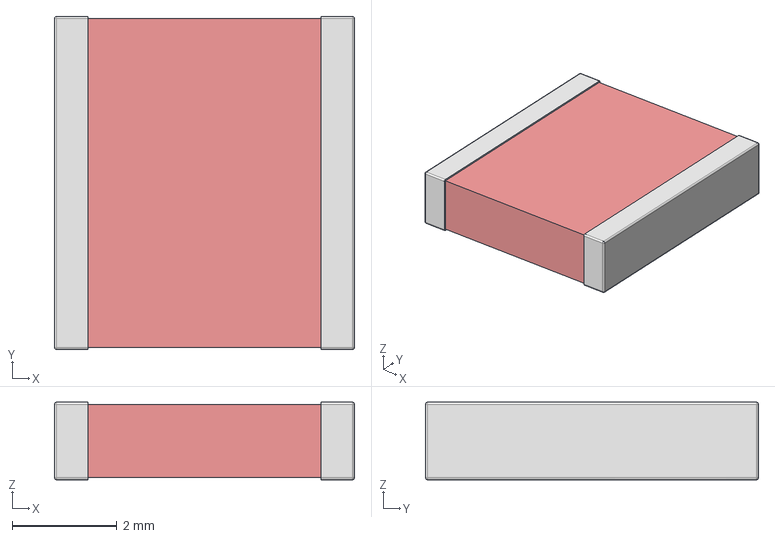
[picture p71: CAD file, 2015-10-08]
PCBA/Master_Altium_Library/3D Models/CAP2225.stp
5.72 x 6.35 x 1.48 mm
