rmfharvey/EE4951_REPO/PCBA/Master_Altium_Library/3D Models/jumper2_2.54mm.stp

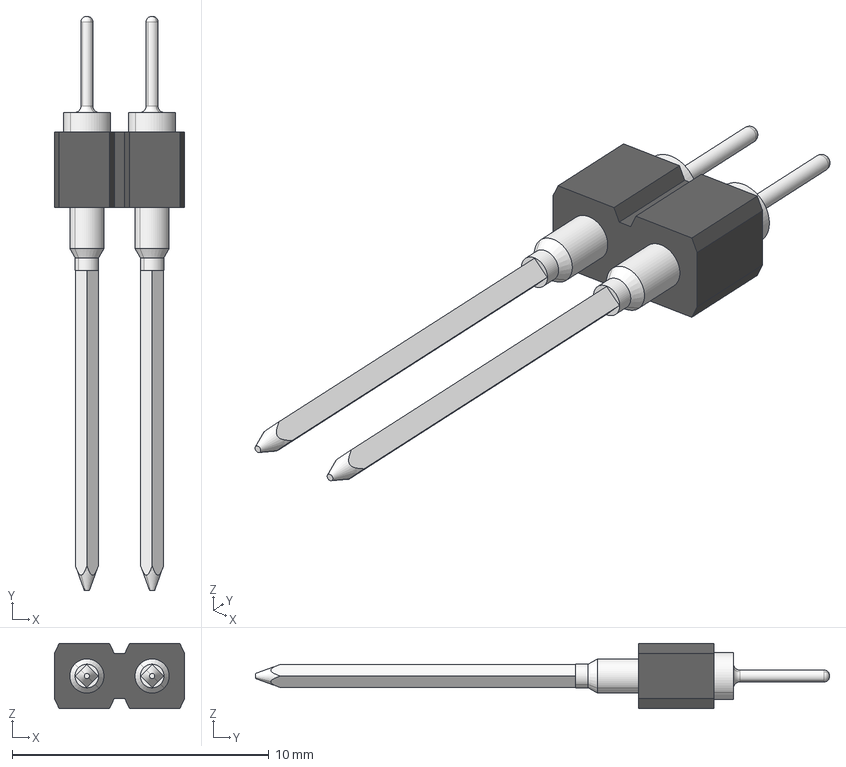
[picture p72: CAD file, 2015-10-08]
PCBA/Master_Altium_Library/3D Models/jumper2_2.54mm.stp
5.08 x 22.4 x 2.54 mm
