rmfharvey/EE4951_REPO/PCBA/Master_Altium_Library/3D Models/TSSOP-8 3_1x3_1.STEP

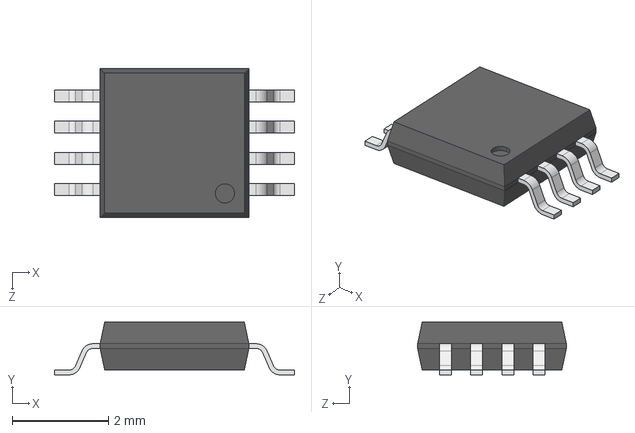
[picture p73: CAD file, 2015-10-08]
PCBA/Master_Altium_Library/3D Models/TSSOP-8 3_1x3_1.STEP
5.00 x 1.10 x 3.10 mm
User Library-TSSOP-8 3.1x3.1_pin_TSSOP_tssop_1 x 8
User Library-TSSOP-8 3.1x3.1_body_TSSOP_TSSOP_3.1x3.1_1
