rmfharvey/EE4951_REPO/PCBA/Master_Altium_Library/3D Models/BGA144_10x10mm_0.8mm_pitch.step

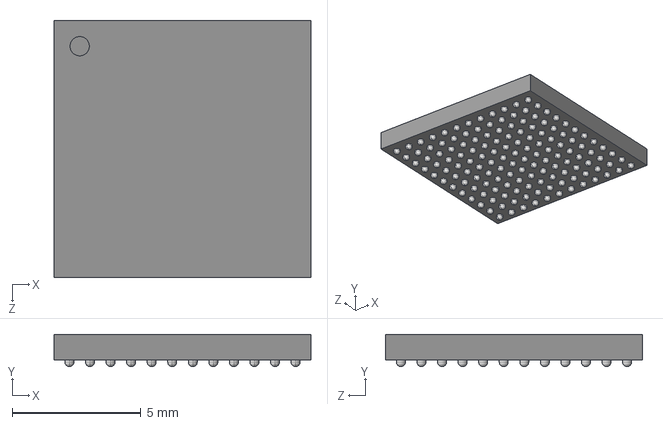
[picture p75: CAD file, 2015-10-08]
PCBA/Master_Altium_Library/3D Models/BGA144_10x10mm_0.8mm_pitch.step
10.0 x 1.25 x 10.0 mm
