rmfharvey/EE4951_REPO/PCBA/Master_Altium_Library/3D Models/SC70-6.step

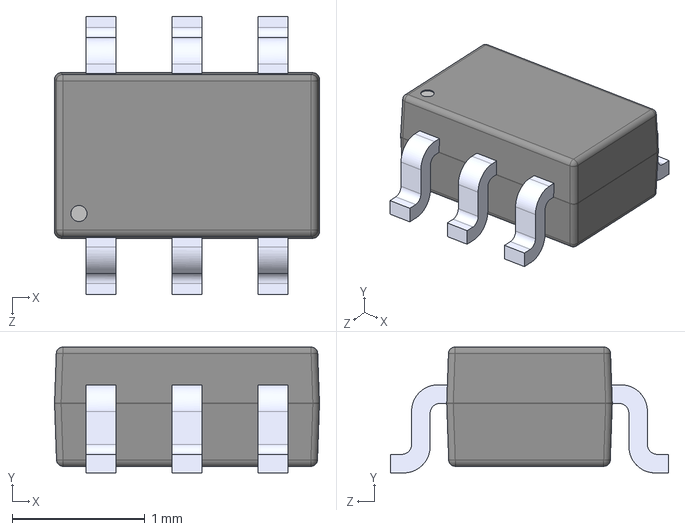
[picture p76: CAD file, 2015-10-08]
PCBA/Master_Altium_Library/3D Models/SC70-6.step
2.00 x 0.95 x 2.10 mm
