rmfharvey/EE4951_REPO/PCBA/Master_Altium_Library/3D Models/SOIC08 narrow.stp

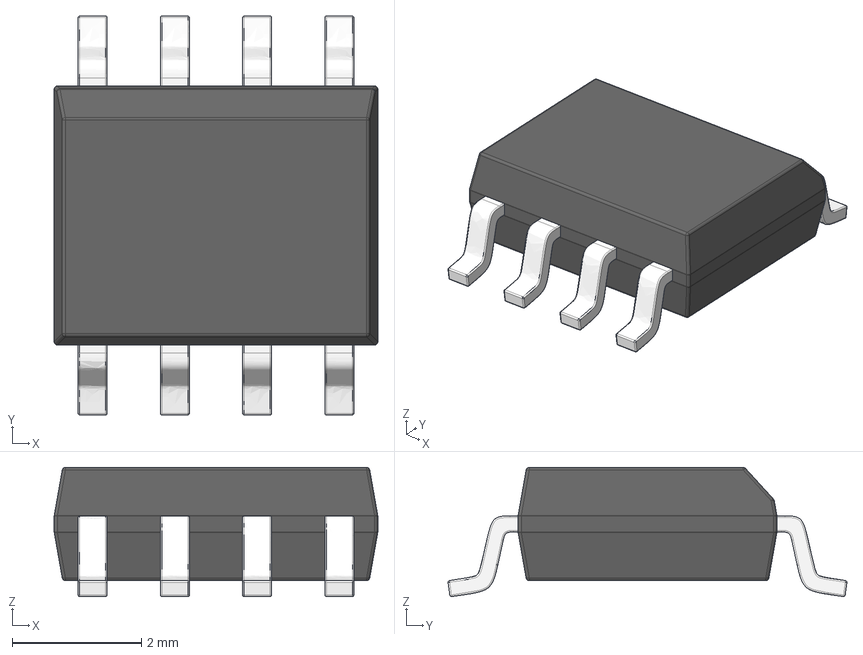
[picture p77: CAD file, 2015-10-08]
PCBA/Master_Altium_Library/3D Models/SOIC08 narrow.stp
5.00 x 6.16 x 2.00 mm
