rmfharvey/EE4951_REPO/PCBA/Master_Altium_Library/3D Models/SOT23-3.stEP

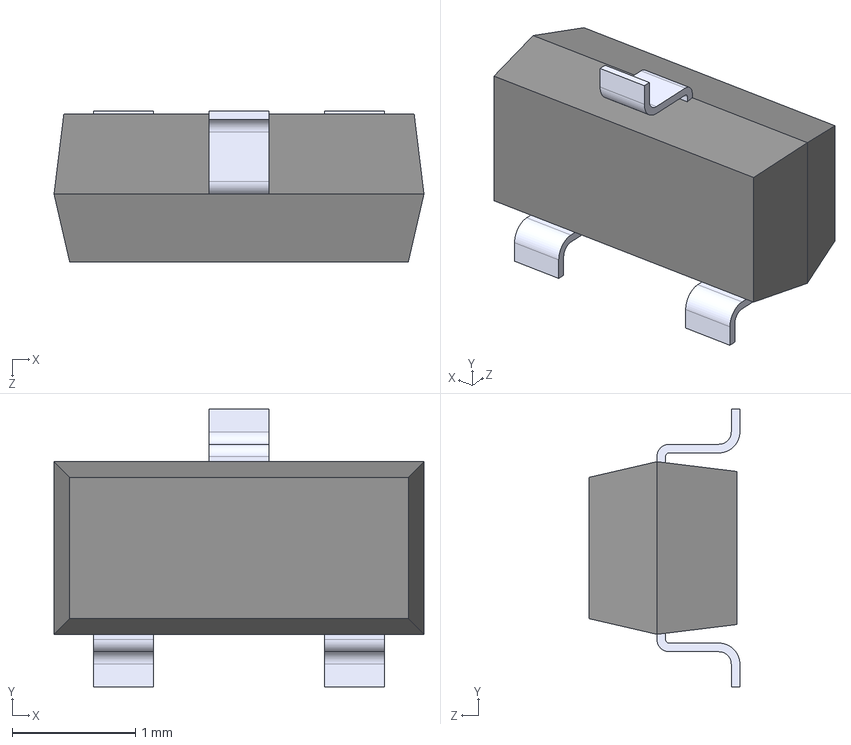
[picture p78: CAD file, 2015-10-08]
PCBA/Master_Altium_Library/3D Models/SOT23-3.stEP
3.00 x 2.25 x 1.22 mm
