rmfharvey/EE4951_REPO/PCBA/Master_Altium_Library/3D Models/SOT-323.step

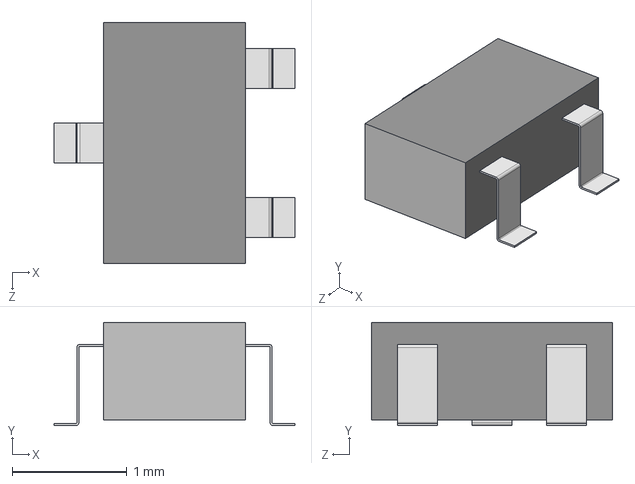
[picture p79: CAD file, 2015-10-08]
PCBA/Master_Altium_Library/3D Models/SOT-323.step
2.10 x 0.9 x 2.10 mm
