rmfharvey/EE4951_REPO/PCBA/Master_Altium_Library/3D Models/SMD_ELKO_6,3x5,8.stp

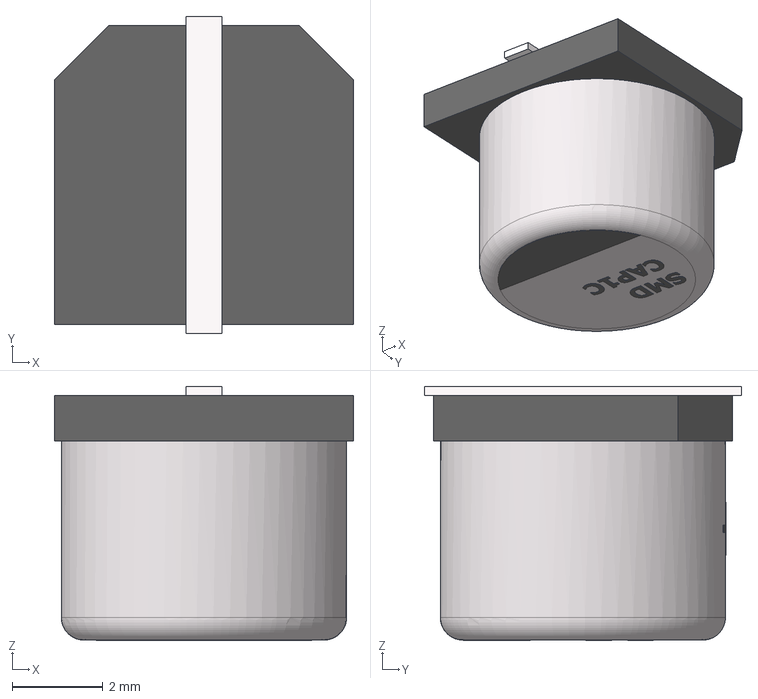
[picture p80: CAD file, 2015-10-08]
PCBA/Master_Altium_Library/3D Models/SMD_ELKO_6,3x5,8.stp
6.60 x 7.00 x 5.61 mm
