rmfharvey/EE4951_REPO/PCBA/Master_Altium_Library/3D Models/RES2512.stp

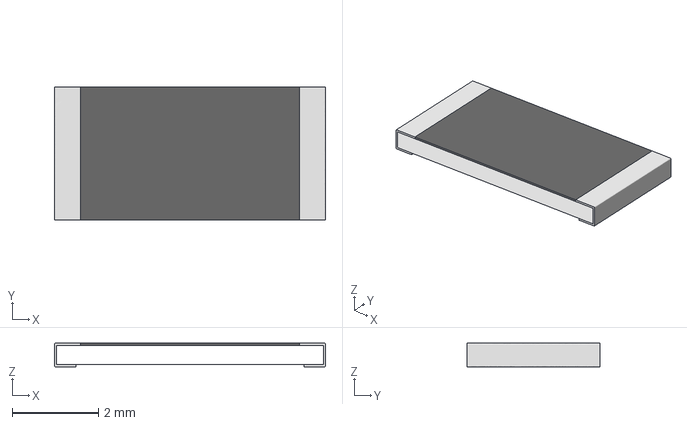
[picture p81: CAD file, 2015-10-08]
PCBA/Master_Altium_Library/3D Models/RES2512.stp
6.30 x 3.10 x 0.55 mm
