rmfharvey/EE4951_REPO/PCBA/Master_Altium_Library/3D Models/TQFP64_Grid_0_5.STEP

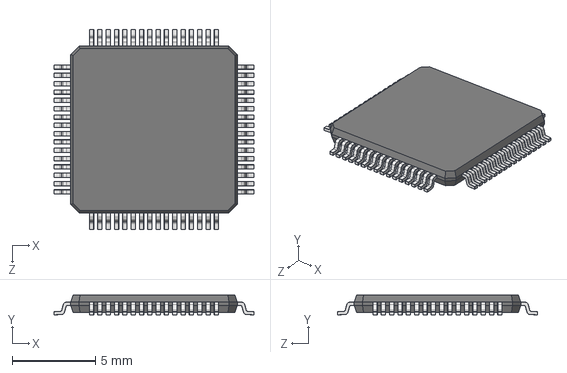
[picture p82: CAD file, 2015-10-08]
PCBA/Master_Altium_Library/3D Models/TQFP64_Grid_0_5.STEP
12.0 x 1.20 x 12.0 mm
User Library-TQFP64_Grid_0.5_TQFP64_Koerper_2
User Library-TQFP64_Grid_0.5_TQFP_PIN_2 x 64
