rmfharvey/EE4951_REPO/PCBA/Master_Altium_Library/3D Models/ATX_PSU_Conn.stp

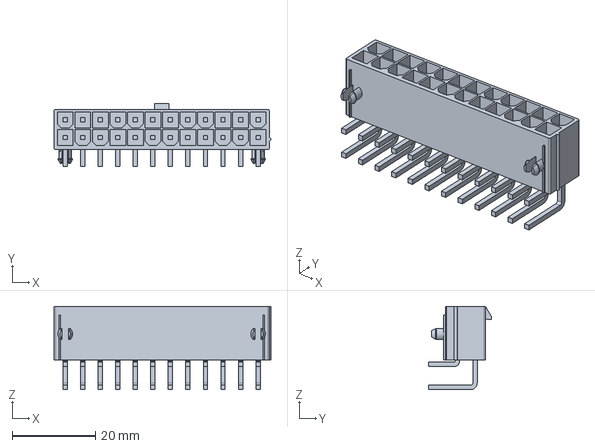
[picture p84: CAD file, 2015-10-08]
PCBA/Master_Altium_Library/3D Models/ATX_PSU_Conn.stp
52.0 x 15.0 x 19.9 mm
