rmfharvey/EE4951_REPO/PCBA/Master_Altium_Library/3D Models/CAP1210.stp

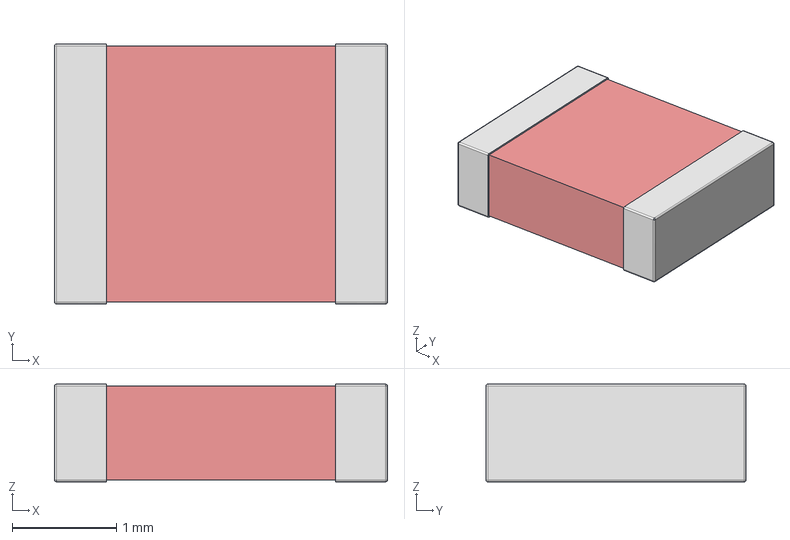
[picture p85: CAD file, 2015-10-08]
PCBA/Master_Altium_Library/3D Models/CAP1210.stp
3.20 x 2.50 x 0.94 mm
