rmfharvey/EE4951_REPO/PCBA/Master_Altium_Library/3D Models/CAP1812.stp

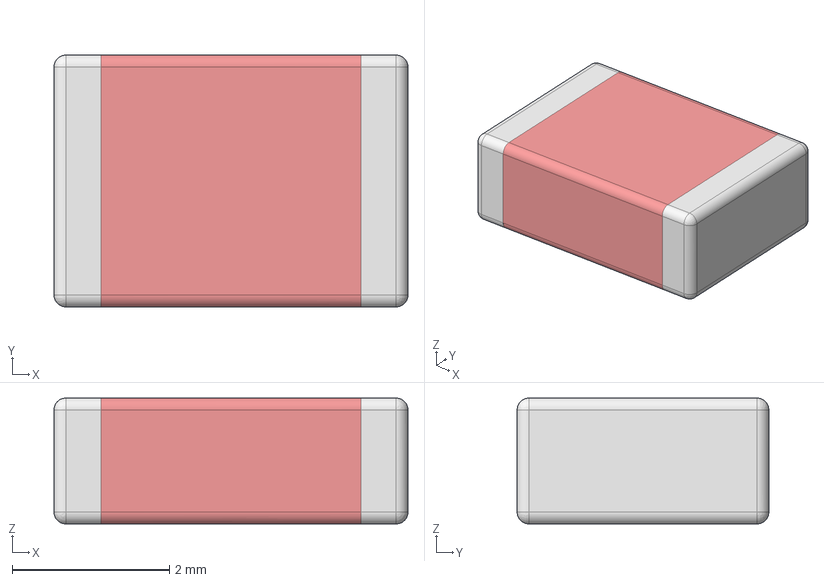
[picture p86: CAD file, 2015-10-08]
PCBA/Master_Altium_Library/3D Models/CAP1812.stp
4.50 x 3.20 x 1.60 mm
