rmfharvey/EE4951_REPO/PCBA/Master_Altium_Library/3D Models/LQFP100 0_5mm 14x14.STEP

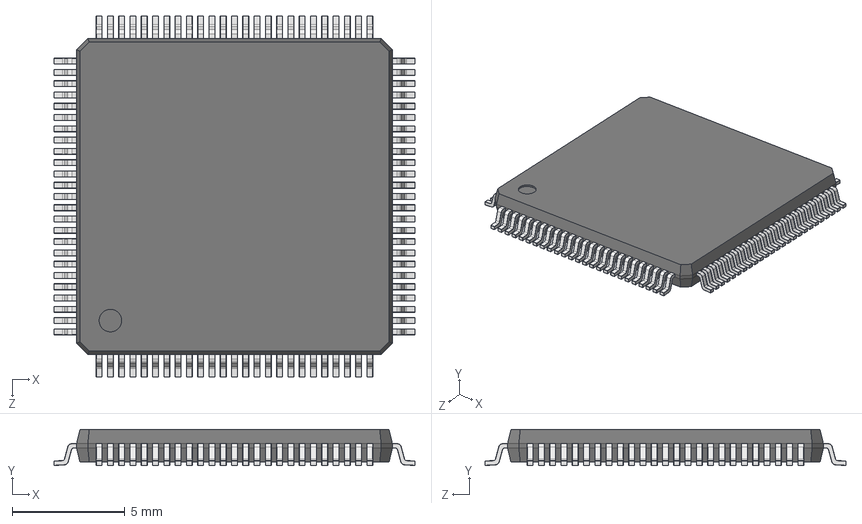
[picture p88: CAD file, 2015-10-08]
PCBA/Master_Altium_Library/3D Models/LQFP100 0_5mm 14x14.STEP
16.0 x 1.60 x 16.0 mm
User Library-LQFP100_Grid_0.5_LQFP100_Koerper_2
User Library-LQFP100_Grid_0.5_LQFP_PIN_2 x 100
