rmfharvey/EE4951_REPO/PCBA/Master_Altium_Library/3D Models/LDQ-N516R1.step

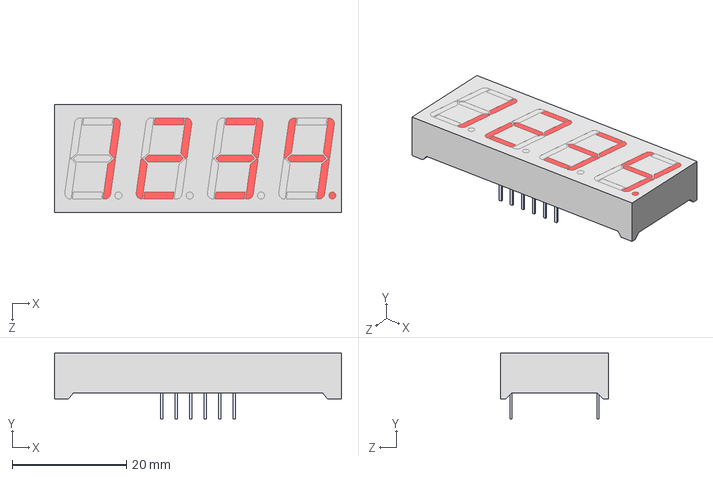
[picture p89: CAD file, 2015-10-08]
PCBA/Master_Altium_Library/3D Models/LDQ-N516R1.step
50.3 x 11.5 x 19.0 mm
