rmfharvey/EE4951_REPO/PCBA/Master_Altium_Library/3D Models/BNC_Connector.stp

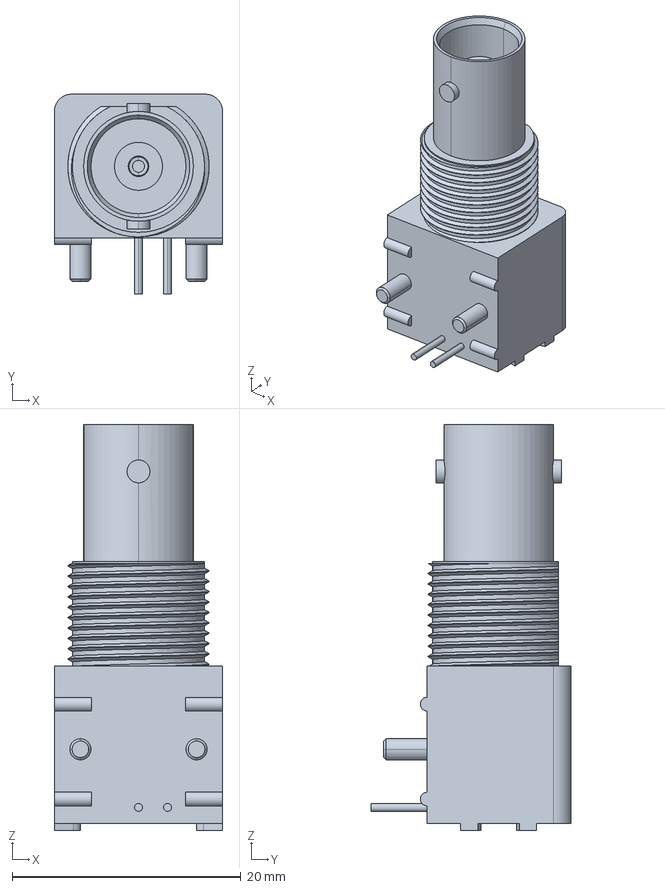
[picture p90: CAD file, 2015-10-08]
PCBA/Master_Altium_Library/3D Models/BNC_Connector.stp
14.7 x 17.5 x 35.5 mm
