rmfharvey/EE4951_REPO/PCBA/Master_Altium_Library/3D Models/RES1206.stp

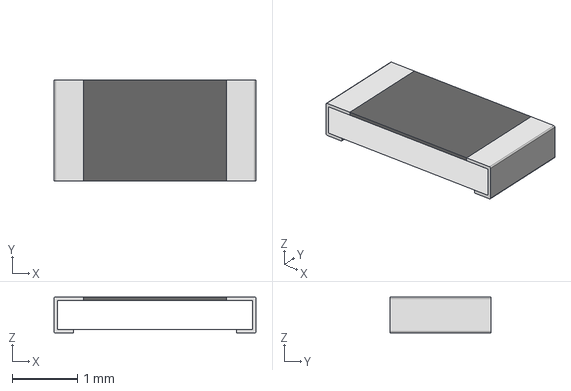
[picture p91: CAD file, 2015-10-08]
PCBA/Master_Altium_Library/3D Models/RES1206.stp
3.10 x 1.55 x 0.55 mm
