rmfharvey/EE4951_REPO/PCBA/Master_Altium_Library/3D Models/SOIC24.step

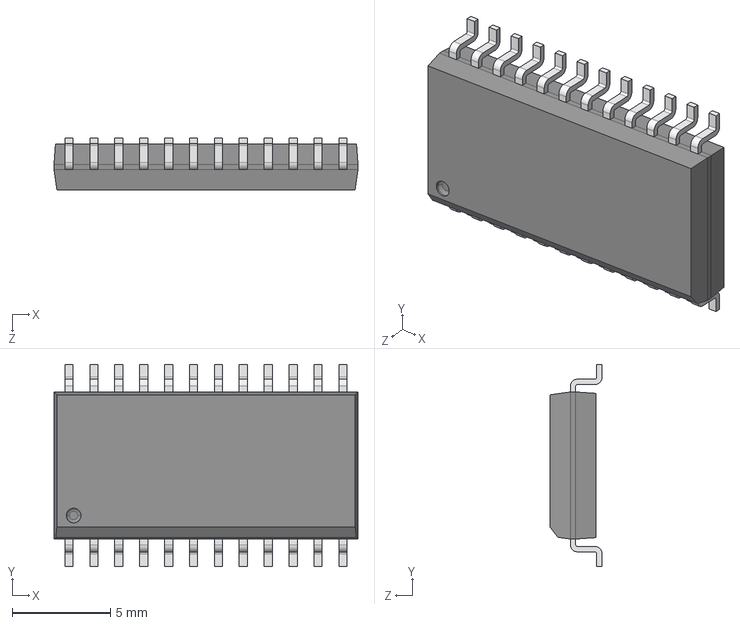
[picture p92: CAD file, 2015-10-08]
PCBA/Master_Altium_Library/3D Models/SOIC24.step
15.5 x 10.3 x 2.65 mm
