rmfharvey/EE4951_REPO/PCBA/Master_Altium_Library/3D Models/RES0603.stp

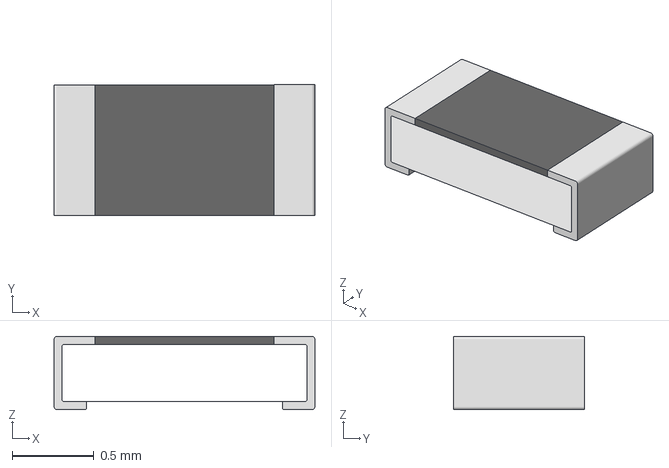
[picture p93: CAD file, 2015-10-08]
PCBA/Master_Altium_Library/3D Models/RES0603.stp
1.60 x 0.8 x 0.45 mm
