rmfharvey/EE4951_REPO/PCBA/Master_Altium_Library/3D Models/HC49_Crystal_SM.step

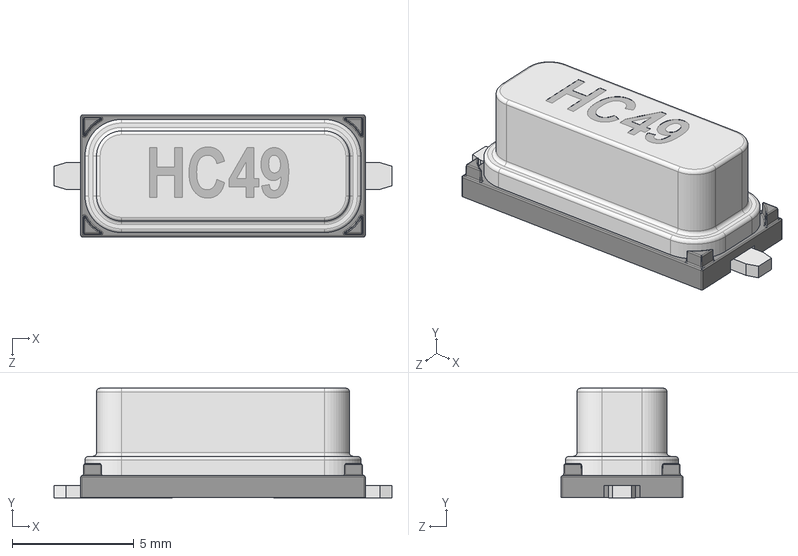
[picture p94: CAD file, 2015-10-08]
PCBA/Master_Altium_Library/3D Models/HC49_Crystal_SM.step
13.9 x 4.51 x 5.00 mm
