rmfharvey/EE4951_REPO/PCBA/Master_Altium_Library/3D Models/Banana_jack_red.step

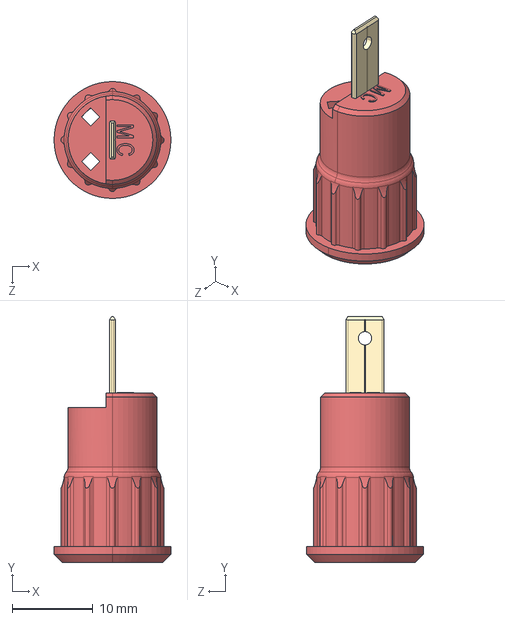
[picture p95: CAD file, 2015-10-08]
PCBA/Master_Altium_Library/3D Models/Banana_jack_red.step
14.5 x 30.5 x 14.5 mm
