rmfharvey/EE4951_REPO/PCBA/Master_Altium_Library/3D Models/LED SMD RGB.step

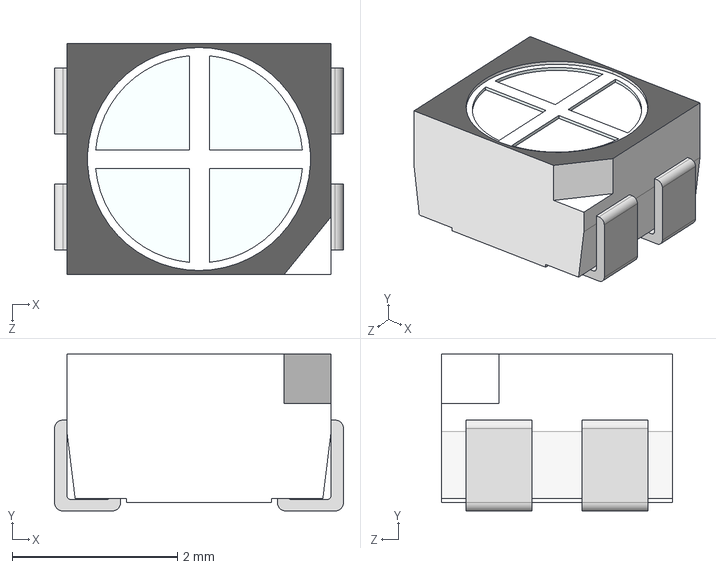
[picture p96: CAD file, 2015-10-08]
PCBA/Master_Altium_Library/3D Models/LED SMD RGB.step
3.50 x 1.90 x 2.80 mm
