rmfharvey/EE4951_REPO/PCBA/Master_Altium_Library/3D Models/SOT-23-6.step

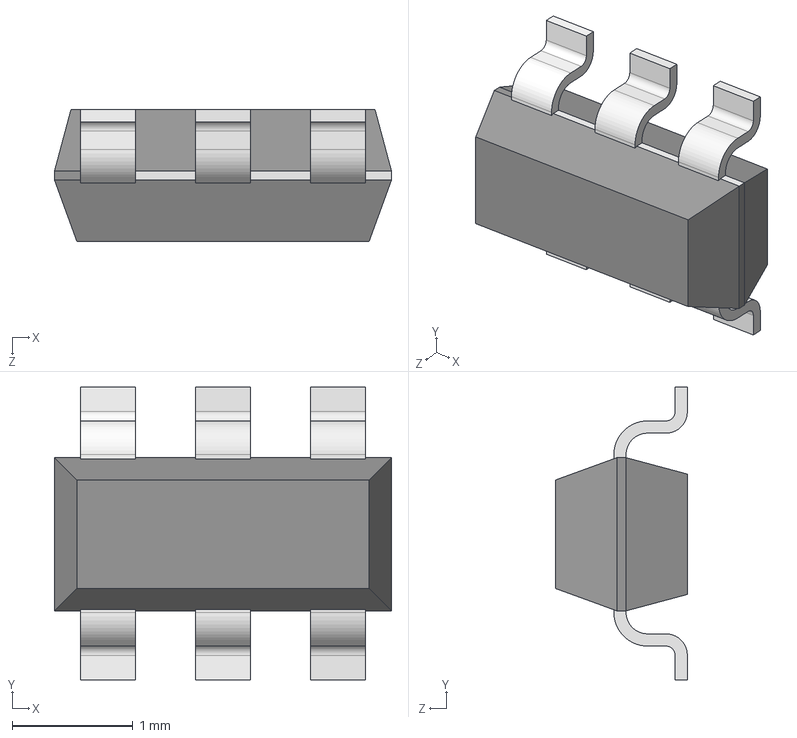
[picture p97: CAD file, 2015-10-08]
PCBA/Master_Altium_Library/3D Models/SOT-23-6.step
2.79 x 2.43 x 1.09 mm
