rmfharvey/EE4951_REPO/PCBA/Master_Altium_Library/3D Models/RES1218.stp

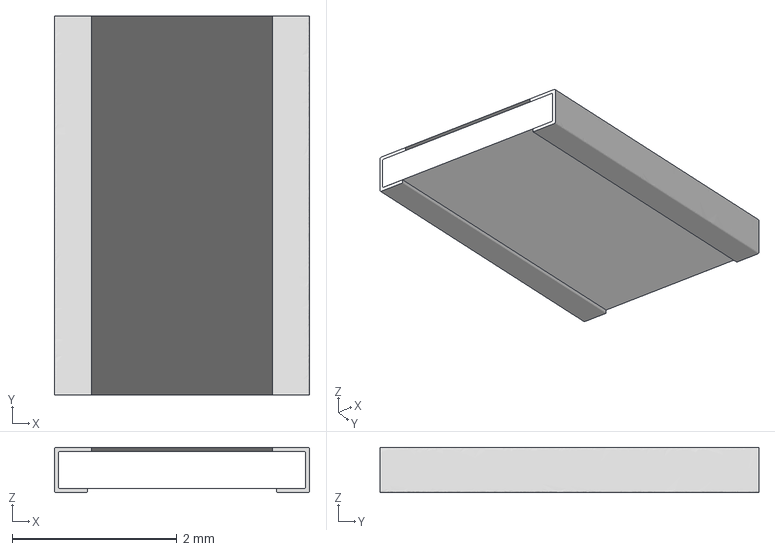
[picture p98: CAD file, 2015-10-08]
PCBA/Master_Altium_Library/3D Models/RES1218.stp
3.10 x 4.61 x 0.55 mm
