rmfharvey/EE4951_REPO/PCBA/Master_Altium_Library/3D Models/jumper_5x2_2.54mm.stp

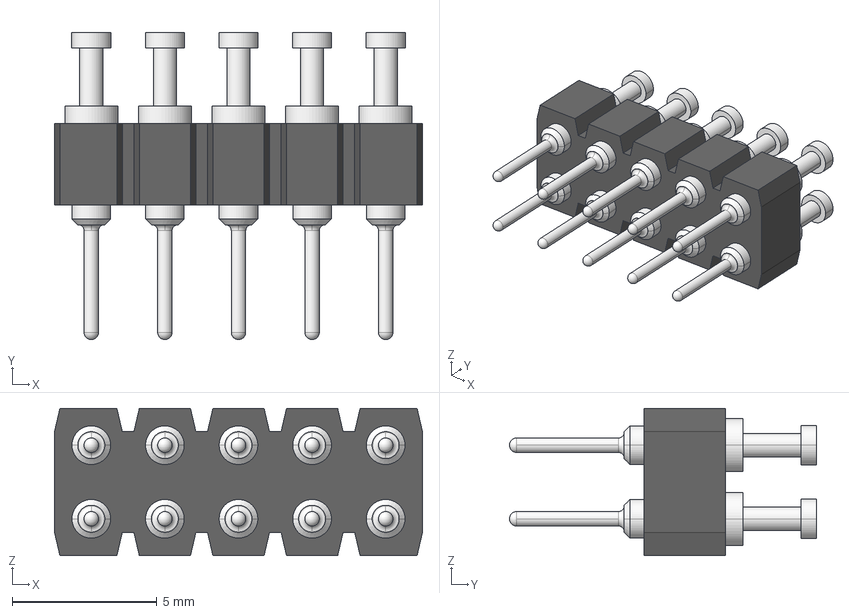
[picture p100: CAD file, 2015-10-08]
PCBA/Master_Altium_Library/3D Models/jumper_5x2_2.54mm.stp
12.7 x 10.6 x 5.08 mm
