rmfharvey/EE4951_REPO/PCBA/Master_Altium_Library/3D Models/SSOP-28.step

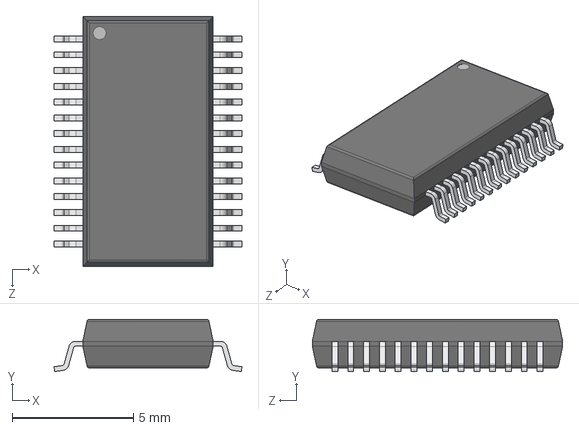
[picture p101: CAD file, 2015-10-08]
PCBA/Master_Altium_Library/3D Models/SSOP-28.step
7.76 x 2.15 x 10.3 mm
