rmfharvey/EE4951_REPO/PCBA/Master_Altium_Library/3D Models/1x6 Header Right Angle.stp

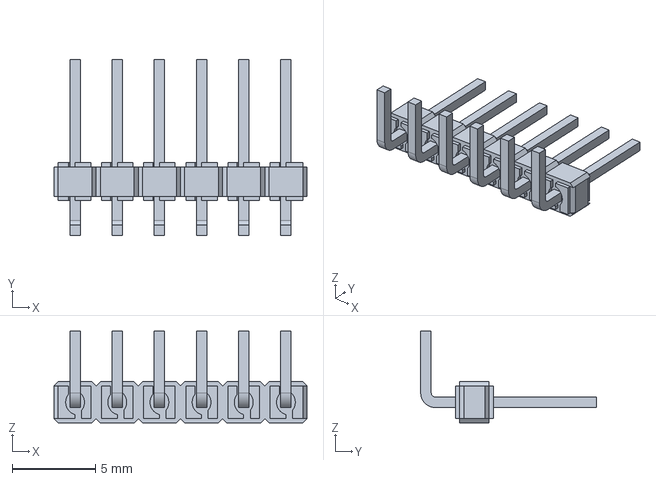
[picture p102: CAD file, 2015-10-08]
PCBA/Master_Altium_Library/3D Models/1x6 Header Right Angle.stp
15.2 x 10.6 x 5.54 mm
