rmfharvey/EE4951_REPO/PCBA/Master_Altium_Library/3D Models/DIP16.step

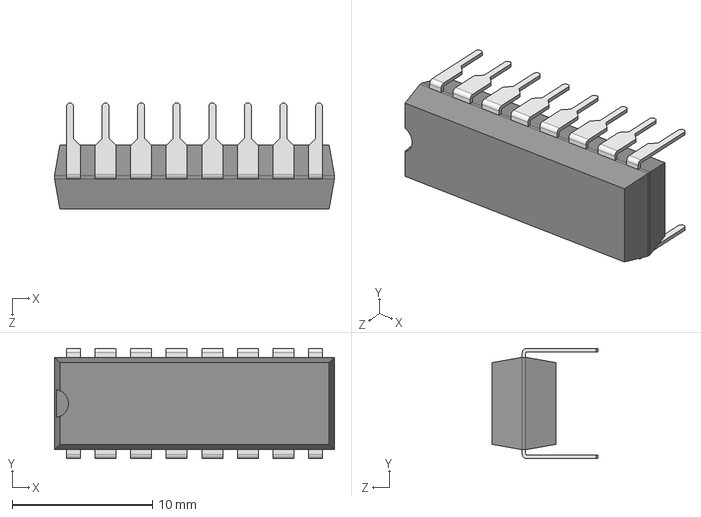
[picture p103: CAD file, 2015-10-08]
PCBA/Master_Altium_Library/3D Models/DIP16.step
20.0 x 7.87 x 7.57 mm
