rmfharvey/EE4951_REPO/PCBA/Master_Altium_Library/3D Models/SOD-323.step

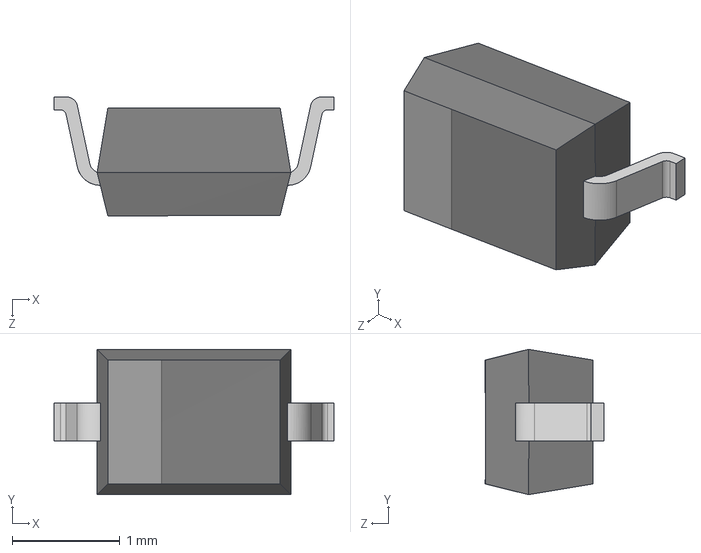
[picture p104: CAD file, 2015-10-08]
PCBA/Master_Altium_Library/3D Models/SOD-323.step
2.60 x 1.35 x 1.10 mm
