rmfharvey/EE4951_REPO/PCBA/Master_Altium_Library/3D Models/SOIC14 narrow.stp

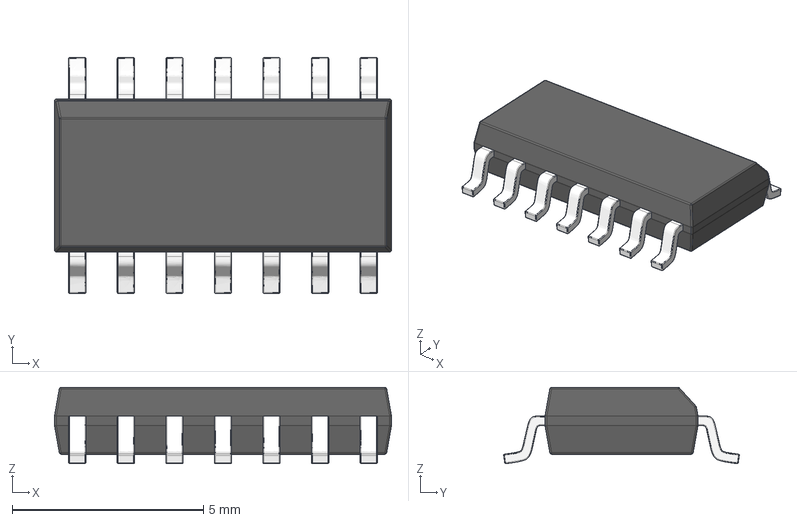
[picture p105: CAD file, 2015-10-08]
PCBA/Master_Altium_Library/3D Models/SOIC14 narrow.stp
8.81 x 6.16 x 2.00 mm
