rmfharvey/EE4951_REPO/PCBA/Master_Altium_Library/3D Models/1x6 Header.stp

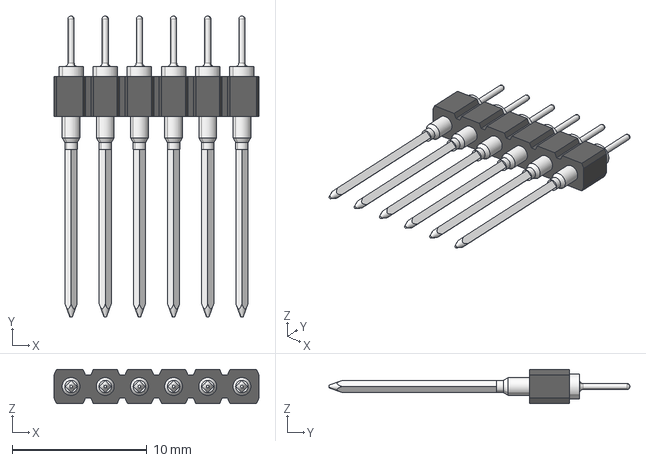
[picture p106: CAD file, 2015-10-08]
PCBA/Master_Altium_Library/3D Models/1x6 Header.stp
15.2 x 22.4 x 2.54 mm
