rmfharvey/EE4951_REPO/PCBA/Master_Altium_Library/3D Models/MicroFit 2x2.stp

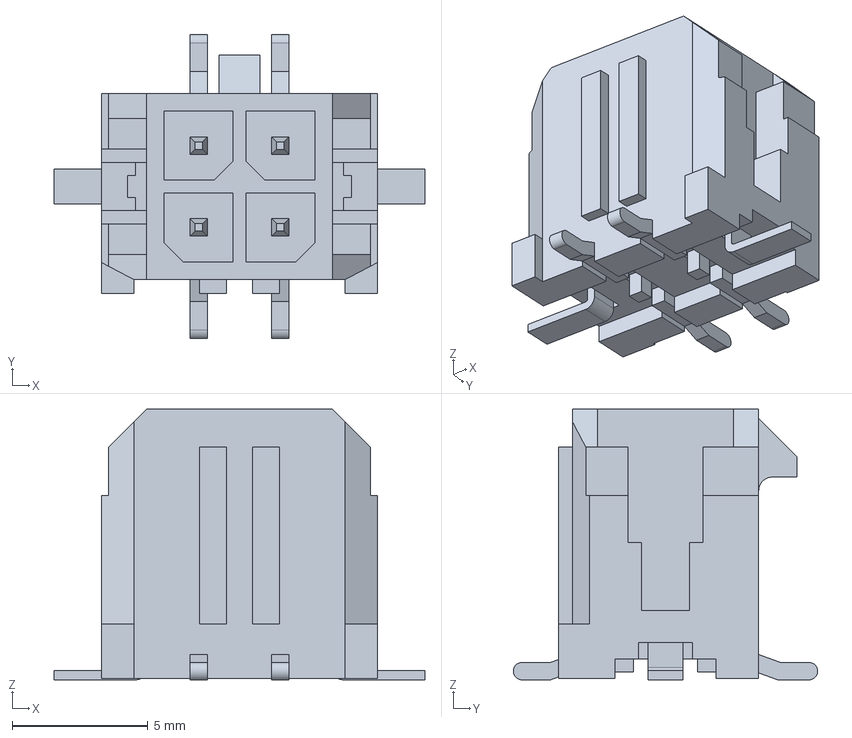
[picture p107: CAD file, 2015-10-08]
PCBA/Master_Altium_Library/3D Models/MicroFit 2x2.stp
13.7 x 11.2 x 9.96 mm
