rmfharvey/EE4951_REPO/PCBA/Master_Altium_Library/3D Models/RES0805.stp

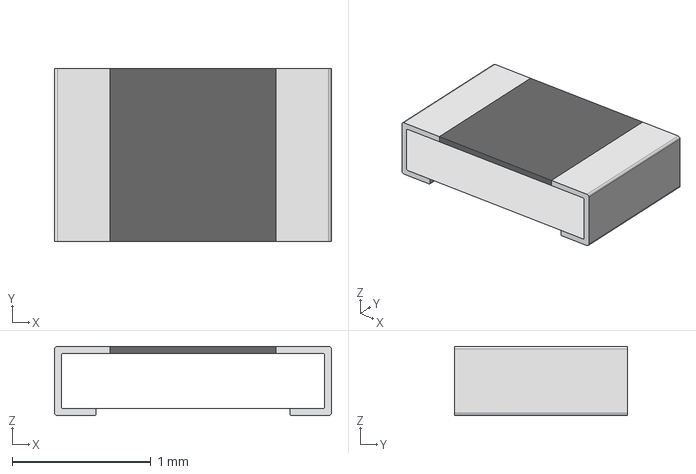
[picture p109: CAD file, 2015-10-08]
PCBA/Master_Altium_Library/3D Models/RES0805.stp
2.00 x 1.25 x 0.5 mm
