rmfharvey/EE4951_REPO/PCBA/Master_Altium_Library/3D Models/CAP1206.stp

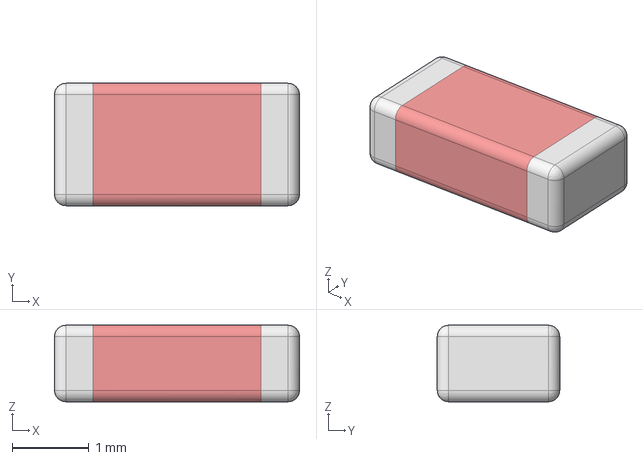
[picture p110: CAD file, 2015-10-08]
PCBA/Master_Altium_Library/3D Models/CAP1206.stp
3.20 x 1.60 x 1.00 mm
