rmfharvey/EE4951_REPO/PCBA/Master_Altium_Library/3D Models/39-29-3026.stp

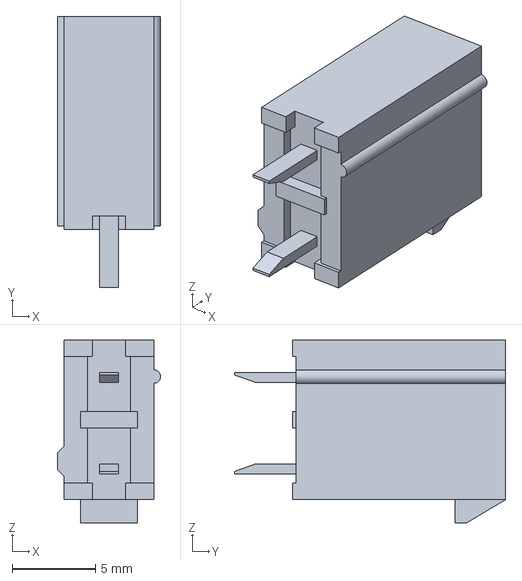
[picture p111: CAD file, 2015-10-08]
PCBA/Master_Altium_Library/3D Models/39-29-3026.stp
6.20 x 16.3 x 11.0 mm
