rmfharvey/EE4951_REPO/PCBA/Master_Altium_Library/3D Models/CAP0402.stp

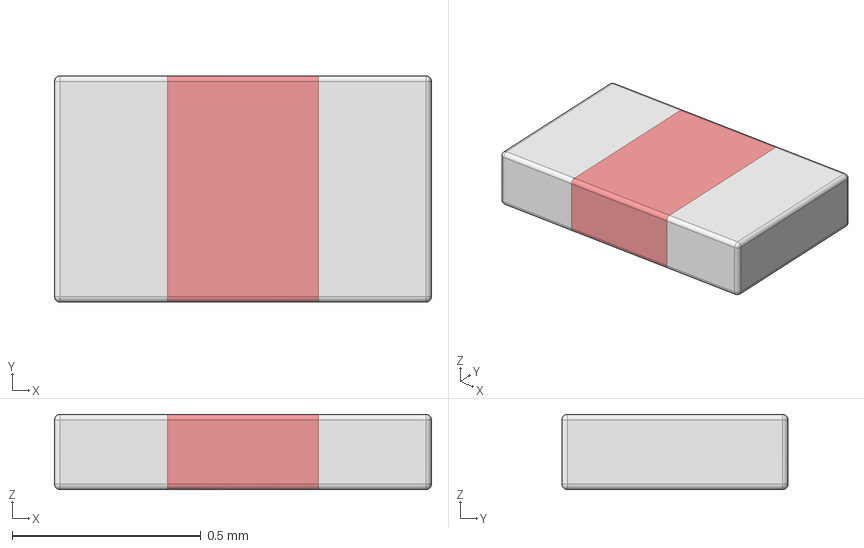
[picture p112: CAD file, 2015-10-08]
PCBA/Master_Altium_Library/3D Models/CAP0402.stp
1.00 x 0.6 x 0.2 mm
