rmfharvey/EE4951_REPO/PCBA/Master_Altium_Library/3D Models/SOIC16 narrow.stp

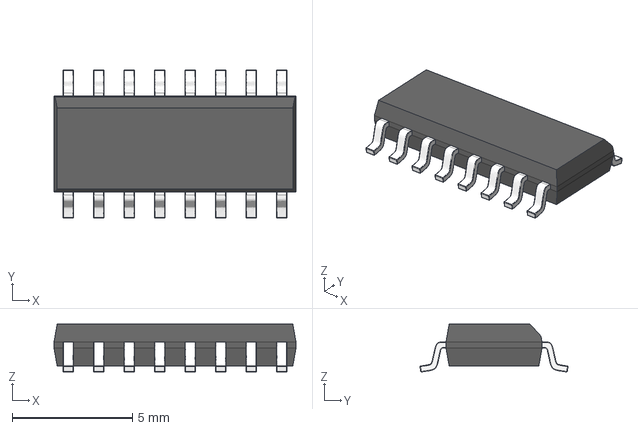
[picture p113: CAD file, 2015-10-08]
PCBA/Master_Altium_Library/3D Models/SOIC16 narrow.stp
10.1 x 6.16 x 2.00 mm
