rmfharvey/EE4951_REPO/PCBA/Master_Altium_Library/3D Models/S-PVSON-N8.STEP

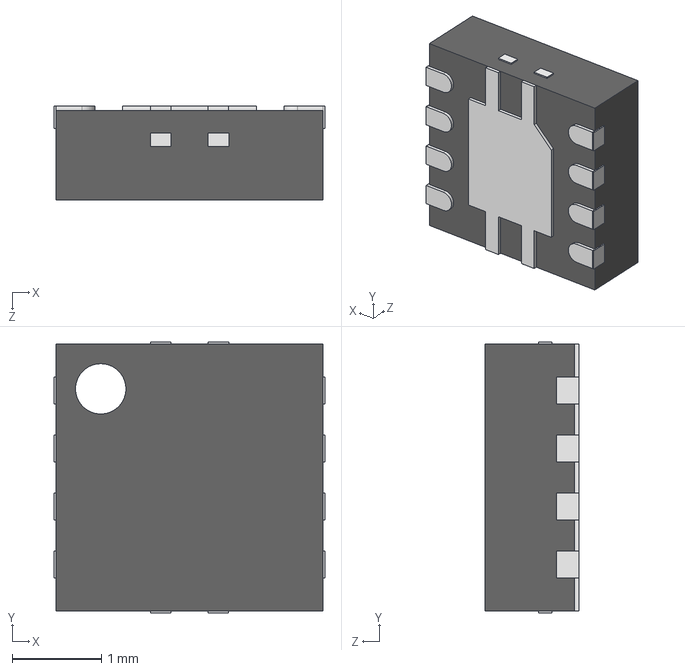
[picture p114: CAD file, 2015-10-08]
PCBA/Master_Altium_Library/3D Models/S-PVSON-N8.STEP
3.04 x 3.04 x 1.05 mm
