rmfharvey/EE4951_REPO/PCBA/Master_Altium_Library/3D Models/RES0402.stp

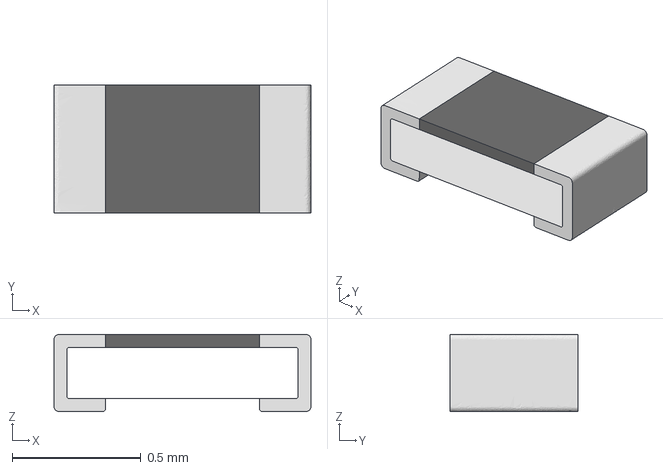
[picture p115: CAD file, 2015-10-08]
PCBA/Master_Altium_Library/3D Models/RES0402.stp
1.00 x 0.5 x 0.3 mm
