rmfharvey/EE4951_REPO/Firmware/Test/EE4951_BPM_REVA/ee4951_k22_test/Documentation/ee4951_k22_test.txt

=============================================================================
List of generated methods in project: ee4951_k22_test

This text description is generated by Processor Expert. Do not modify it.
=============================================================================

Module "clockMan1" (component fsl_clock_manager)
   - clockMan1_CLOCK_SYS_SetOutDiv1 -Sets the clock out divider1 setting(OUTDIV1).
   - clockMan1_CLOCK_SYS_GetOutDiv1 -Gets the clock out divider1 setting(OUTDIV1).
   - clockMan1_CLOCK_SYS_SetOutDiv2 -Sets the clock out divider2 setting(OUTDIV2).
   - clockMan1_CLOCK_SYS_GetOutDiv2 -Gets the clock out divider2 setting(OUTDIV2).
   - clockMan1_CLOCK_SYS_SetOutDiv3 -Sets the clock out divider3 setting(OUTDIV3).
   - clockMan1_CLOCK_SYS_GetOutDiv3 -Gets the clock out divider3 setting(OUTDIV3).
   - clockMan1_CLOCK_SYS_SetOutDiv4 -Sets the clock out divider4 setting(OUTDIV4).
   - clockMan1_CLOCK_SYS_GetOutDiv4 -Gets the clock out divider4 setting(OUTDIV4).
   - clockMan1_CLOCK_SYS_SetOutDiv -Sets the clock out dividers setting.
   - clockMan1_CLOCK_SYS_GetOutDiv -Gets the clock out dividers setting.
   - clockMan1_CLOCK_SYS_GetFlexbusFreq -Get flexbus clock frequency.
   - clockMan1_CLOCK_SYS_GetPllFllClockFreq -Get the MCGPLLCLK/MCGFLLCLK/IRC48MCLK clock frequency.
   - clockMan1_CLOCK_SYS_SetPllfllSel -Set PLL/FLL clock selection.
   - clockMan1_CLOCK_SYS_GetPllfllSel -Get PLL/FLL clock selection.
   - clockMan1_CLOCK_SYS_GetFixedFreqClockFreq -Gets the MCGFFCLK clock frequency.
   - clockMan1_CLOCK_SYS_GetInternalRefClockFreq -Get internal reference clock frequency.
   - clockMan1_CLOCK_SYS_GetExternalRefClock32kFreq -Gets the external reference 32k clock frequency.
   - clockMan1_CLOCK_SYS_SetExternalRefClock32kSrc -Set the clock selection of ERCLK32K.
   - clockMan1_CLOCK_SYS_GetExternalRefClock32kSrc -Get the clock selection of ERCLK32K.
   - clockMan1_CLOCK_SYS_GetOsc0ExternalRefClockFreq -Gets the OSC0ERCLK frequency.
   - clockMan1_CLOCK_SYS_GetOsc0ExternalRefClockUndivFreq -Gets the OSC0ERCLK_UNDIV frequency.
   - clockMan1_CLOCK_SYS_GetRtcFreq -Gets RTC input clock frequency.
   - clockMan1_CLOCK_SYS_GetRtcOutFreq -Gets RTC_CLKOUT frequency.
   - clockMan1_CLOCK_SYS_GetRtcOutSrc -Gets RTC_CLKOUT source.
   - clockMan1_CLOCK_SYS_SetRtcOutSrc -Gets RTC_CLKOUT source.
   - clockMan1_CLOCK_SYS_GetWdogFreq -Gets the watch dog clock frequency.
   - clockMan1_CLOCK_SYS_GetTraceSrc -Gets the debug trace clock source.
   - clockMan1_CLOCK_SYS_SetTraceSrc -Sets the debug trace clock source.
   - clockMan1_CLOCK_SYS_GetTraceFreq -Gets the debug trace clock frequency.
   - clockMan1_CLOCK_SYS_GetPortFilterFreq -Gets PORTx digital input filter clock frequency.
   - clockMan1_CLOCK_SYS_GetLptmrFreq -Gets LPTMRx pre-scaler/glitch filter clock frequency.
   - clockMan1_CLOCK_SYS_GetEwmFreq -Gets the clock frequency for EWM module.
   - clockMan1_CLOCK_SYS_GetFtfFreq -Gets the clock frequency for FTF module. (Flash Memory)
   - clockMan1_CLOCK_SYS_GetCrcFreq -Gets the clock frequency for CRC module.
   - clockMan1_CLOCK_SYS_GetCmpFreq -Gets the clock frequency for CMP module.
   - clockMan1_CLOCK_SYS_GetVrefFreq -Gets the clock frequency for VREF module.
   - clockMan1_CLOCK_SYS_GetPdbFreq -Gets the clock frequency for PDB module.
   - clockMan1_CLOCK_SYS_GetPitFreq -Gets the clock frequency for PIT module.
   - clockMan1_CLOCK_SYS_GetCmtFreq -Gets the clock frequency for CMT module.
   - clockMan1_CLOCK_SYS_GetUsbfsSrc -Gets the clock source for USB FS OTG module.
   - clockMan1_CLOCK_SYS_SetUsbfsSrc -Sets the clock source for USB FS OTG module.
   - clockMan1_CLOCK_SYS_GetUsbfsFreq -Gets the clock frequency for USB FS OTG module.
   - clockMan1_CLOCK_SYS_SetUsbfsDiv -Set USB FS divider setting.
   - clockMan1_CLOCK_SYS_GetUsbfsDiv -Get USB FS divider setting.
   - clockMan1_CLOCK_SYS_GetLpuartSrc -Gets the clock source for LPUART module.
   - clockMan1_CLOCK_SYS_SetLpuartSrc -Sets the clock source for LPUART module.
   - clockMan1_CLOCK_SYS_GetLpuartFreq -Gets the clock frequency for LPUART module.
   - clockMan1_CLOCK_SYS_GetSaiFreq -Gets the clock frequency for SAI.
   - clockMan1_CLOCK_SYS_GetSpiFreq -Gets the clock frequency for SPI module.
   - clockMan1_CLOCK_SYS_GetI2cFreq -Gets the clock frequency for I2C module.
   - clockMan1_CLOCK_SYS_GetAdcAltFreq -Gets ADC alternate clock frequency.
   - clockMan1_CLOCK_SYS_GetAdcAlt2Freq -Gets ADC alternate 2 clock frequency.
   - clockMan1_CLOCK_SYS_GetFtmFixedFreq -Gets FTM fixed frequency clock frequency.
   - clockMan1_CLOCK_SYS_GetFtmSystemClockFreq -Gets FTM's system clock frequency.
   - clockMan1_CLOCK_SYS_GetFtmExternalFreq -Gets FTM external clock frequency.
   - clockMan1_CLOCK_SYS_GetFtmExternalSrc -Gets FTM external clock source.
   - clockMan1_CLOCK_SYS_SetFtmExternalSrc -Sets FTM external clock source.
   - clockMan1_CLOCK_SYS_GetUartFreq -Gets the clock frequency for UART module.
   - clockMan1_CLOCK_SYS_GetGpioFreq -Gets the clock frequency for GPIO module.
   - clockMan1_CLOCK_SYS_EnableDmaClock -Enable the clock for DMA module.
   - clockMan1_CLOCK_SYS_DisableDmaClock -Disable the clock for DMA module.
   - clockMan1_CLOCK_SYS_GetDmaGateCmd -Get the the clock gate state for DMA module.
   - clockMan1_CLOCK_SYS_EnableDmamuxClock -Enable the clock for DMAMUX module.
   - clockMan1_CLOCK_SYS_DisableDmamuxClock -Disable the clock for DMAMUX module.
   - clockMan1_CLOCK_SYS_GetDmamuxGateCmd -Get the the clock gate state for DMAMUX module.
   - clockMan1_CLOCK_SYS_EnablePortClock -Enable the clock for PORT module.
   - clockMan1_CLOCK_SYS_DisablePortClock -Disable the clock for PORT module.
   - clockMan1_CLOCK_SYS_GetPortGateCmd -Get the the clock gate state for PORT module.
   - clockMan1_CLOCK_SYS_EnableEwmClock -Enable the clock for EWM module.
   - clockMan1_CLOCK_SYS_DisableEwmClock -Disable the clock for EWM module.
   - clockMan1_CLOCK_SYS_GetEwmGateCmd -Get the the clock gate state for EWM module.
   - clockMan1_CLOCK_SYS_EnableFlexbusClock -Enable the clock for FLEXBUS module.
   - clockMan1_CLOCK_SYS_DisableFlexbusClock -Disable the clock for FLEXBUS module.
   - clockMan1_CLOCK_SYS_GetFlexbusGateCmd -Get the the clock gate state for FLEXBUS module.
   - clockMan1_CLOCK_SYS_EnableFtfClock -Enable the clock for FTF module.
   - clockMan1_CLOCK_SYS_DisableFtfClock -Disable the clock for FTF module.
   - clockMan1_CLOCK_SYS_GetFtfGateCmd -Get the the clock gate state for FTF module.
   - clockMan1_CLOCK_SYS_EnableCrcClock -Enable the clock for CRC module.
   - clockMan1_CLOCK_SYS_DisableCrcClock -Disable the clock for CRC module.
   - clockMan1_CLOCK_SYS_GetCrcGateCmd -Get the the clock gate state for CRC module.
   - clockMan1_CLOCK_SYS_EnableRngaClock -Enable the clock for RNGA module.
   - clockMan1_CLOCK_SYS_DisableRngaClock -Disable the clock for RNGA module.
   - clockMan1_CLOCK_SYS_GetRngaGateCmd -Get the the clock gate state for RNGA module.
   - clockMan1_CLOCK_SYS_EnableAdcClock -Enable the clock for ADC module.
   - clockMan1_CLOCK_SYS_DisableAdcClock -Disable the clock for ADC module.
   - clockMan1_CLOCK_SYS_GetAdcGateCmd -Get the the clock gate state for ADC module.
   - clockMan1_CLOCK_SYS_EnableCmpClock -Enable the clock for CMP module.
   - clockMan1_CLOCK_SYS_DisableCmpClock -Disable the clock for CMP module.
   - clockMan1_CLOCK_SYS_GetCmpGateCmd -Get the the clock gate state for CMP module.
   - clockMan1_CLOCK_SYS_EnableDacClock -Enable the clock for DAC module.
   - clockMan1_CLOCK_SYS_DisableDacClock -Disable the clock for DAC module.
   - clockMan1_CLOCK_SYS_GetDacGateCmd -Get the the clock gate state for DAC module.
   - clockMan1_CLOCK_SYS_EnableVrefClock -Enable the clock for VREF module.
   - clockMan1_CLOCK_SYS_DisableVrefClock -Disable the clock for VREF module.
   - clockMan1_CLOCK_SYS_GetVrefGateCmd -Get the the clock gate state for VREF module.
   - clockMan1_CLOCK_SYS_EnableSaiClock -Enable the clock for SAI module.
   - clockMan1_CLOCK_SYS_DisableSaiClock -Disable the clock for SAI module.
   - clockMan1_CLOCK_SYS_GetSaiGateCmd -Get the the clock gate state for SAI module.
   - clockMan1_CLOCK_SYS_EnablePdbClock -Enable the clock for PDB module.
   - clockMan1_CLOCK_SYS_DisablePdbClock -Disable the clock for PDB module.
   - clockMan1_CLOCK_SYS_GetPdbGateCmd -Get the the clock gate state for PDB module.
   - clockMan1_CLOCK_SYS_EnableFtmClock -Enable the clock for FTM module.
   - clockMan1_CLOCK_SYS_DisableFtmClock -Disable the clock for FTM module.
   - clockMan1_CLOCK_SYS_GetFtmGateCmd -Get the the clock gate state for FTM module.
   - clockMan1_CLOCK_SYS_EnablePitClock -Enable the clock for PIT module.
   - clockMan1_CLOCK_SYS_DisablePitClock -Disable the clock for PIT module.
   - clockMan1_CLOCK_SYS_GetPitGateCmd -Get the the clock gate state for PIT module.
   - clockMan1_CLOCK_SYS_EnableLptmrClock -Enable the clock for LPTIMER module.
   - clockMan1_CLOCK_SYS_DisableLptmrClock -Disable the clock for LPTIMER module.
   - clockMan1_CLOCK_SYS_GetLptmrGateCmd -Get the the clock gate state for LPTIMER module.
   - clockMan1_CLOCK_SYS_EnableRtcClock -Enable the clock for RTC module.
   - clockMan1_CLOCK_SYS_DisableRtcClock -Disable the clock for RTC module.
   - clockMan1_CLOCK_SYS_GetRtcGateCmd -Get the the clock gate state for RTC module.
   - clockMan1_CLOCK_SYS_EnableUsbfsClock -Enable the clock for USBFS module.
   - clockMan1_CLOCK_SYS_DisableUsbfsClock -Disable the clock for USBFS module.
   - clockMan1_CLOCK_SYS_GetUsbfsGateCmd -Get the the clock gate state for USB module.
   - clockMan1_CLOCK_SYS_EnableSpiClock -Enable the clock for SPI module.
   - clockMan1_CLOCK_SYS_DisableSpiClock -Disable the clock for SPI module.
   - clockMan1_CLOCK_SYS_GetSpiGateCmd -Get the the clock gate state for SPI module.
   - clockMan1_CLOCK_SYS_EnableI2cClock -Enable the clock for I2C module.
   - clockMan1_CLOCK_SYS_DisableI2cClock -Disable the clock for I2C module.
   - clockMan1_CLOCK_SYS_GetI2cGateCmd -Get the the clock gate state for I2C module.
   - clockMan1_CLOCK_SYS_EnableUartClock -Enable the clock for UART module.
   - clockMan1_CLOCK_SYS_DisableUartClock -Disable the clock for UART module.
   - clockMan1_CLOCK_SYS_GetUartGateCmd -Get the the clock gate state for UART module.
   - clockMan1_CLOCK_SYS_EnableLpuartClock -Enable the clock for LPUART module.
   - clockMan1_CLOCK_SYS_DisableLpuartClock -Disable the clock for LPUART module.
   - clockMan1_CLOCK_SYS_GetLpuartGateCmd -Get the the clock gate state for LPUART module.
   - clockMan1_CLOCK_SYS_SetUsbExternalFreq -Set the USB external clock frequency(USB_CLKIN).
   - clockMan1_CLOCK_SYS_SetFtmExternalFreq -Set the FTM external clock frequency(FTM_CLKx).
   - clockMan1_CLOCK_SYS_Init -Install pre-defined clock configurations.
   - clockMan1_CLOCK_SYS_UpdateConfiguration -Set system clock configuration according to pre-defined structure.
   - clockMan1_CLOCK_SYS_SetConfiguration -Set system clock configuration.
   - clockMan1_CLOCK_SYS_GetCurrentConfiguration -Get current system clock configuration.
   - clockMan1_CLOCK_SYS_GetErrorCallback -Get the callback which returns error in last clock switch.
   - clockMan1_CLOCK_SYS_SetMcgliteMode -Sets the MCG_Lite to some specific mode.
   - clockMan1_CLOCK_SYS_SetMcgMode -Set MCG to some target mode.
   - clockMan1_CLOCK_SYS_OscInit -Initialize OSC.
   - clockMan1_CLOCK_SYS_OscDeinit -Deinitialize OSC.
   - clockMan1_CLOCK_SYS_SetOscerConfigration -Configure the OSCERCLK.
   - clockMan1_CLOCK_SYS_RtcOscInit -Initialize the RTC OSC.
   - clockMan1_CLOCK_SYS_RtcOscDeinit -Deinitialize RTC OSC.
   - clockMan1_CLOCK_SYS_GetFreq -Gets the clock frequency for a specific clock name.
   - clockMan1_CLOCK_SYS_GetCoreClockFreq -Get core clock frequency.
   - clockMan1_CLOCK_SYS_GetSystemClockFreq -Get system clock frequency.
   - clockMan1_CLOCK_SYS_GetBusClockFreq -Get bus clock frequency.
   - clockMan1_CLOCK_SYS_GetFlashClockFreq -Get flash clock frequency.
   - clockMan1_CLOCK_SYS_GetLpoClockFreq -Get LPO clock frequency.
   - clockMan1_CLOCK_SYS_SetSystickSrc -Set Systick clock source SYST_CSR[CLKSOURCE].
   - clockMan1_CLOCK_SYS_GetSystickFreq -Get Systick clock frequency.

Module "pin_init"  (component PinSettings)
   - pin_init_hardware_init -This method configures registers according to settings of routing and electrical features. It 
                provides pin initialization for selected pins during processor start-up. Selected pins are either user selected 
                pins or pins selected in pin properties in components.  Only pins of devices  enabled for auto initialization 
                are handled within this method.
   - pin_init_init_adc_pins -ADC method configures registers according to settings  of routing and electrical features. This 
                method is enabled only if any pin of corresponding peripheral type is selected. Selected pins are either user 
                selected pins or pins selected in pin items in components. Call this method code to route desired pins into 
                ADC0, ADC1 peripherals.
   - pin_init_deinit_adc_pins -ADC method configures registers according to settings  of routing and electrical features. This 
                method is enabled only if any pin of corresponding peripheral type is selected. Selected pins are either user 
                selected pins or pins selected in pin items in components. Call this method code to route desired pins into 
                ADC0, ADC1 peripherals.
   - pin_init_init_cmp_pins -CMP method configures registers according to settings  of routing and electrical features. This 
                method is enabled only if any pin of corresponding peripheral type is selected. Selected pins are either user 
                selected pins or pins selected in pin items in components. Call this method code to route desired pins into 
                CMP0, CMP1 peripherals.
   - pin_init_deinit_cmp_pins -CMP method configures registers according to settings  of routing and electrical features. This 
                method is enabled only if any pin of corresponding peripheral type is selected. Selected pins are either user 
                selected pins or pins selected in pin items in components. Call this method code to route desired pins into 
                CMP0, CMP1 peripherals.
   - pin_init_init_gpio_pins -GPIO method configures registers according to settings  of routing and electrical features. This 
                method is enabled only if any pin of corresponding peripheral type is selected. Selected pins are either user 
                selected pins or pins selected in pin items in components. Call this method code to route desired pins into PTA,
                PTB, PTC, PTD, PTE peripherals.
   - pin_init_deinit_gpio_pins -GPIO method configures registers according to settings  of routing and electrical features. 
                This method is enabled only if any pin of corresponding peripheral type is selected. Selected pins are either 
                user selected pins or pins selected in pin items in components. Call this method code to route desired pins 
                into PTA, PTB, PTC, PTD, PTE peripherals.
   - pin_init_init_jtag_pins -JTAG method configures registers according to settings  of routing and electrical features. This 
                method is enabled only if any pin of corresponding peripheral type is selected. Selected pins are either user 
                selected pins or pins selected in pin items in components. Call this method code to route desired pins into 
                JTAG peripheral.
   - pin_init_deinit_jtag_pins -JTAG method configures registers according to settings  of routing and electrical features. 
                This method is enabled only if any pin of corresponding peripheral type is selected. Selected pins are either 
                user selected pins or pins selected in pin items in components. Call this method code to route desired pins 
                into JTAG peripheral.
   - pin_init_init_llwu_pins -LLWU method configures registers according to settings  of routing and electrical features. This 
                method is enabled only if any pin of corresponding peripheral type is selected. Selected pins are either user 
                selected pins or pins selected in pin items in components. Call this method code to route desired pins into 
                LLWU peripheral.
   - pin_init_deinit_llwu_pins -LLWU method configures registers according to settings  of routing and electrical features. 
                This method is enabled only if any pin of corresponding peripheral type is selected. Selected pins are either 
                user selected pins or pins selected in pin items in components. Call this method code to route desired pins 
                into LLWU peripheral.
   - pin_init_init_osc_pins -OSC method configures registers according to settings  of routing and electrical features. This 
                method is enabled only if any pin of corresponding peripheral type is selected. Selected pins are either user 
                selected pins or pins selected in pin items in components. Call this method code to route desired pins into OSC 
                peripheral.
   - pin_init_deinit_osc_pins -OSC method configures registers according to settings  of routing and electrical features. This 
                method is enabled only if any pin of corresponding peripheral type is selected. Selected pins are either user 
                selected pins or pins selected in pin items in components. Call this method code to route desired pins into OSC 
                peripheral.
   - pin_init_init_spi_pins -SPI method configures registers according to settings  of routing and electrical features. This 
                method is enabled only if any pin of corresponding peripheral type is selected. Selected pins are either user 
                selected pins or pins selected in pin items in components. Call this method code to route desired pins into 
                SPI0, SPI1 peripherals.
   - pin_init_deinit_spi_pins -SPI method configures registers according to settings  of routing and electrical features. This 
                method is enabled only if any pin of corresponding peripheral type is selected. Selected pins are either user 
                selected pins or pins selected in pin items in components. Call this method code to route desired pins into 
                SPI0, SPI1 peripherals.
   - pin_init_init_tpiu_pins -TPIU method configures registers according to settings  of routing and electrical features. This 
                method is enabled only if any pin of corresponding peripheral type is selected. Selected pins are either user 
                selected pins or pins selected in pin items in components. Call this method code to route desired pins into 
                TPIU peripheral.
   - pin_init_deinit_tpiu_pins -TPIU method configures registers according to settings  of routing and electrical features. 
                This method is enabled only if any pin of corresponding peripheral type is selected. Selected pins are either 
                user selected pins or pins selected in pin items in components. Call this method code to route desired pins 
                into TPIU peripheral.
   - pin_init_init_uart_pins -UART method configures registers according to settings  of routing and electrical features. This 
                method is enabled only if any pin of corresponding peripheral type is selected. Selected pins are either user 
                selected pins or pins selected in pin items in components. Call this method code to route desired pins into 
                UART0, UART1, UART2 peripherals.
   - pin_init_deinit_uart_pins -UART method configures registers according to settings  of routing and electrical features. 
                This method is enabled only if any pin of corresponding peripheral type is selected. Selected pins are either 
                user selected pins or pins selected in pin items in components. Call this method code to route desired pins 
                into UART0, UART1, UART2 peripherals.

Module "intMan1"   (component fsl_interrupt_manager)
   - intMan1_INT_SYS_InstallHandler -Installs an interrupt handler routine for a given IRQ number.
   - intMan1_INT_SYS_EnableIRQ -Enables an interrupt for a given IRQ number.
   - intMan1_INT_SYS_DisableIRQ -Disables an interrupt for a given IRQ number.
   - intMan1_INT_SYS_EnableIRQGlobal -Enables system interrupt.
   - intMan1_INT_SYS_DisableIRQGlobal -Disable system interrupt.

Module "osa1"      (component fsl_os_abstraction)
   - osa1_OSA_PollAllOtherTasks -Calls all task functions one time except for the current task.
   - osa1_DefaultISR -The default interrupt handler installed in vector table.
   - osa1_OSA_SemaCreate -Creates a semaphore with a given value.
   - osa1_OSA_SemaWait -Pending a semaphore with timeout.
   - osa1_OSA_SemaPost -Signals for someone waiting on the semaphore to wake up.
   - osa1_OSA_SemaDestroy -Destroys a previously created semaphore.
   - osa1_OSA_MutexCreate -Create an unlocked mutex.
   - osa1_OSA_MutexLock -Waits for a mutex and locks it.
   - osa1_OSA_MutexUnlock -Unlocks a previously locked mutex.
   - osa1_OSA_MutexDestroy -Destroys a previously created mutex.
   - osa1_OSA_EventCreate -Initializes an event object with all flags cleared.
   - osa1_OSA_EventWait -Waits for specified event flags to be set.
   - osa1_OSA_EventSet -Sets one or more event flags.
   - osa1_OSA_EventClear -Clears one or more flags.
   - osa1_OSA_EventGetFlags -Gets event flags status.
   - osa1_OSA_EventDestroy -Destroys a previously created event object.
   - osa1_OSA_TaskCreate -Creates a task.
   - osa1_OSA_TaskDestroy -Destroys a previously created task.
   - osa1_OSA_TaskYield -Puts the active task to the end of scheduler's queue.
   - osa1_OSA_TaskGetHandler -Gets the handler of active task.
   - osa1_OSA_TaskGetPriority -Gets the priority of a task.
   - osa1_OSA_TaskSetPriority -Sets the priority of a task.
   - osa1_OSA_MsgQCreate -Initializes a message queue.
   - osa1_OSA_MsgQPut -Puts a message at the end of the queue.
   - osa1_OSA_MsgQGet -Reads and remove a message at the head of the queue.
   - osa1_OSA_MsgQDestroy -Destroys a previously created queue.
   - osa1_OSA_MemAlloc -Reserves the requested amount of memory in bytes.
   - osa1_OSA_MemAllocZero -Reserves the requested amount of memory in bytes and initializes it to 0.
   - osa1_OSA_MemFree -Releases the memory previously reserved.
   - osa1_OSA_TimeDelay -Delays execution for a number of milliseconds.
   - osa1_OSA_TimeGetMsec -Gets the current time since system boot in milliseconds.
   - osa1_OSA_InstallIntHandler -Installs the interrupt handler.
   - osa1_OSA_EnterCritical -Enters the critical section to ensure some code is not preempted.
   - osa1_OSA_ExitCritical -Exits the critical section.
   - osa1_OSA_Init -Initializes the RTOS services.
   - osa1_OSA_Start -Starts the RTOS.

Module "DbgCs1"    (component fsl_debug_console)
   - DbgCs1_DbgConsole_Init -Init the UART/LPUART used for debug messages.
   - DbgCs1_DbgConsole_DeInit -Deinit the UART/LPUART used for debug messages.
   - DbgCs1_debug_printf -Prints formatted output to the standard output stream.
   - DbgCs1_debug_putchar -Writes a character to stdout.
   - DbgCs1_debug_scanf -Reads formatted data from the standard input stream.
   - DbgCs1_debug_getchar -Reads a character from standard input.

Module "sd_card"   (component fsl_sdcard)
   - sd_card_SDSPI_DRV_Init -Initializes the card on a specific SPI instance.
   - sd_card_SDSPI_DRV_ReadBlocks -Reads blocks from the specific card.
   - sd_card_SDSPI_DRV_WriteBlocks -Writes blocks of data to the specific card.
   - sd_card_SDSPI_DRV_CheckReadOnly -Checks whether the card is write-protected.
   - sd_card_SDSPI_DRV_Shutdown -Deinitializes the card.
   - sd_card_SDCARD_DRV_Init -Initializes the card on a specific host controller.
   - sd_card_SDCARD_DRV_ReadBlocks -Reads blocks from the specific card.
   - sd_card_SDCARD_DRV_WriteBlocks -Writes blocks of data to the specific card.
   - sd_card_SDCARD_DRV_EraseBlocks -Erases blocks of the specific card.
   - sd_card_SDCARD_DRV_CheckReadOnly -Checks whether the card is write-protected.
   - sd_card_SDCARD_DRV_Shutdown -Deinitializes the card.

Module "WAIT1"     (component Wait)
   - WAIT1_Wait10Cycles -Wait for 10 CPU cycles.
   - WAIT1_Wait100Cycles -Wait for 100 CPU cycles.
   - WAIT1_WaitCycles -Wait for a specified number of CPU cycles (16bit data type).
   - WAIT1_WaitLongCycles -Wait for a specified number of CPU cycles (32bit data type).
   - WAIT1_Waitms -Wait for a specified time in milliseconds.
   - WAIT1_Waitus -Wait for a specified time in microseconds.
   - WAIT1_Waitns -Wait for a specified time in nano seconds.
   - WAIT1_WaitOSms -If an RTOS is enabled, this routine will use a non-blocking wait method. Otherwise it will do a 
                busy/blocking wait.

Module "disp_spi"  (component fsl_dspi)
   - disp_spi_DSPI_DRV_IRQHandler -The function DSPI_DRV_IRQHandler passes IRQ control to either the master or slave driver.
   - disp_spi_DSPI_DRV_MasterInit -Initializes a DSPI instance for master mode operation.
   - disp_spi_DSPI_DRV_MasterDeinit -Shuts down a DSPI instance.
   - disp_spi_DSPI_DRV_MasterSetDelay -Configures the DSPI master mode bus timing delay options.
   - disp_spi_DSPI_DRV_MasterConfigureBus -Configures the DSPI port physical parameters to access a device on the bus.
   - disp_spi_DSPI_DRV_MasterTransferBlocking -Performs a blocking SPI master mode transfer.
   - disp_spi_DSPI_DRV_MasterTransfer -Performs a non-blocking SPI master mode transfer.
   - disp_spi_DSPI_DRV_MasterGetTransferStatus -Returns whether the previous transfer is completed.
   - disp_spi_DSPI_DRV_MasterAbortTransfer -Terminates an asynchronous transfer early.
   - disp_spi_DSPI_DRV_MasterIRQHandler -Interrupt handler for DSPI master mode. This handler uses the buffers stored in the 
                dspi_master_state_t structs to transfer data.
   - disp_spi_DSPI_DRV_SlaveInit -Initializes a DSPI instance for a slave mode operation, using interrupt mechanism.
   - disp_spi_DSPI_DRV_SlaveDeinit -Shuts down a DSPI instance - interrupt mechanism.
   - disp_spi_DSPI_DRV_SlaveTransferBlocking -Transfers data on SPI bus using interrupt and blocking call.
   - disp_spi_DSPI_DRV_SlaveTransfer -Starts transfer data on SPI bus using interrupt and a non-blocking call.
   - disp_spi_DSPI_DRV_SlaveAbortTransfer -Aborts the transfer that started by a non-blocking call to a transfer function.
   - disp_spi_DSPI_DRV_SlaveGetTransferStatus -Returns whether the previous transfer is finished.
   - disp_spi_DSPI_DRV_SlaveIRQHandler -DSPI Slave Generic IRQ handler.

Module "dut_adc"   (component fsl_adc16)
   - dut_adc_ADC16_DRV_GetAutoCalibrationParam -Gets the calibration parameters by auto calibration.
   - dut_adc_ADC16_DRV_SetCalibrationParam -Sets the calibration parameters.
   - dut_adc_ADC16_DRV_StructInitUserConfigDefault -Fills the initial user configuration by default for a one-time trigger mode.
   - dut_adc_ADC16_DRV_Init -Initializes the ADC module converter.
   - dut_adc_ADC16_DRV_Deinit -De-initializes the ADC module converter.
   - dut_adc_ADC16_DRV_ConfigHwCompare -Configures the hardware compare feature.
   - dut_adc_ADC16_DRV_ConfigHwAverage -Configures the hardware averaging feature.
   - dut_adc_ADC16_DRV_SetChnMux -Switches the channel mux.
   - dut_adc_ADC16_DRV_ConfigConvChn -Configure the conversion channel by software.
   - dut_adc_ADC16_DRV_WaitConvDone -Waits for the latest conversion to be complete.
   - dut_adc_ADC16_DRV_PauseConv -Pauses the current conversion by software.
   - dut_adc_ADC16_DRV_GetConvValueRAW -Gets the latest conversion value with no format.
   - dut_adc_ADC16_DRV_GetConvValueSigned -Gets the latest conversion value with signed.
   - dut_adc_ADC16_DRV_GetConvFlag -Gets the event status of the ADC16 module.
   - dut_adc_ADC16_DRV_GetChnFlag -Gets the event status of each channel group.

Module "self_adc"  (component fsl_adc16)
   - self_adc_ADC16_DRV_GetAutoCalibrationParam -Gets the calibration parameters by auto calibration.
   - self_adc_ADC16_DRV_SetCalibrationParam -Sets the calibration parameters.
   - self_adc_ADC16_DRV_StructInitUserConfigDefault -Fills the initial user configuration by default for a one-time trigger 
                mode.
   - self_adc_ADC16_DRV_Init -Initializes the ADC module converter.
   - self_adc_ADC16_DRV_Deinit -De-initializes the ADC module converter.
   - self_adc_ADC16_DRV_ConfigHwCompare -Configures the hardware compare feature.
   - self_adc_ADC16_DRV_ConfigHwAverage -Configures the hardware averaging feature.
   - self_adc_ADC16_DRV_SetChnMux -Switches the channel mux.
   - self_adc_ADC16_DRV_ConfigConvChn -Configure the conversion channel by software.
   - self_adc_ADC16_DRV_WaitConvDone -Waits for the latest conversion to be complete.
   - self_adc_ADC16_DRV_PauseConv -Pauses the current conversion by software.
   - self_adc_ADC16_DRV_GetConvValueRAW -Gets the latest conversion value with no format.
   - self_adc_ADC16_DRV_GetConvValueSigned -Gets the latest conversion value with signed.
   - self_adc_ADC16_DRV_GetConvFlag -Gets the event status of the ADC16 module.
   - self_adc_ADC16_DRV_GetChnFlag -Gets the event status of each channel group.

Module "hw_irqs"   (component fsl_gpio)
   - hw_irqs_GPIO_DRV_Init -Initializes all GPIO pins used by the board.
   - hw_irqs_GPIO_DRV_InputPinInit -Initializes one GPIO input pin used by the board.
   - hw_irqs_GPIO_DRV_OutputPinInit -Initializes one GPIO output pin used by the board.
   - hw_irqs_GPIO_DRV_GetPinDir -Gets the current direction of the individual GPIO pin.
   - hw_irqs_GPIO_DRV_SetPinDir -Sets the current direction of the individual GPIO pin.
   - hw_irqs_GPIO_DRV_WritePinOutput -Sets the output level of the individual GPIO pin to the logic 1 or 0.
   - hw_irqs_GPIO_DRV_SetPinOutput -Sets the output level of the individual GPIO pin to the logic 1.
   - hw_irqs_GPIO_DRV_ClearPinOutput -Sets the output level of the individual GPIO pin to the logic 0.
   - hw_irqs_GPIO_DRV_TogglePinOutput -Reverses current output logic of the individual GPIO pin.
   - hw_irqs_GPIO_DRV_ReadPinInput -Reads the current input value of the individual GPIO pin.
   - hw_irqs_GPIO_DRV_SetDigitalFilterCmd -Enables or disables the digital filter in a single port.
   - hw_irqs_GPIO_DRV_IsPinIntPending -Reads the individual pin-interrupt status flag.
   - hw_irqs_GPIO_DRV_ClearPinIntFlag -Clears the individual GPIO pin interrupt status flag.

Module "gpio1"     (component fsl_gpio)
   - gpio1_GPIO_DRV_Init -Initializes all GPIO pins used by the board.
   - gpio1_GPIO_DRV_InputPinInit -Initializes one GPIO input pin used by the board.
   - gpio1_GPIO_DRV_OutputPinInit -Initializes one GPIO output pin used by the board.
   - gpio1_GPIO_DRV_GetPinDir -Gets the current direction of the individual GPIO pin.
   - gpio1_GPIO_DRV_SetPinDir -Sets the current direction of the individual GPIO pin.
   - gpio1_GPIO_DRV_WritePinOutput -Sets the output level of the individual GPIO pin to the logic 1 or 0.
   - gpio1_GPIO_DRV_SetPinOutput -Sets the output level of the individual GPIO pin to the logic 1.
   - gpio1_GPIO_DRV_ClearPinOutput -Sets the output level of the individual GPIO pin to the logic 0.
   - gpio1_GPIO_DRV_TogglePinOutput -Reverses current output logic of the individual GPIO pin.
   - gpio1_GPIO_DRV_ReadPinInput -Reads the current input value of the individual GPIO pin.
   - gpio1_GPIO_DRV_SetDigitalFilterCmd -Enables or disables the digital filter in a single port.
   - gpio1_GPIO_DRV_IsPinIntPending -Reads the individual pin-interrupt status flag.
   - gpio1_GPIO_DRV_ClearPinIntFlag -Clears the individual GPIO pin interrupt status flag.

Module "Cpu"       (component MK22FN512LH12_4SDK)
   - Cpu_SystemInit -This method configures the oscillator (PLL) that is part of the microcontroller device. SystemInit is 
                called from startup_device file.
   - Cpu_SystemCoreClockUpdate -SystemCoreClockUpdate evaluates the clock register settings and calculates the current core 
                clock.

===================================================================================
