rmfharvey/EE4951_REPO/Testing/Testing Documentation.docx

EE4951W Rev. A Testing

Power System

Converter Selection Controls

- Comparator Inputs good
- U7 regulates to 2.7v
- Rework Done on U6 (See 1)
- Buck converter (U5) working
- U9 Needs some minimum output load to regulate
- USB_5V LED always on when powered. Flip M5.

Rework

1. Rewire U6 inputs (Flip U6 +/- inputs)
2. Remove D6
3. Connect V5_MAIN to V5_SUM (Net naming error)

EE4951 Rev. B Changes

Power System

4. Flip U6 +/- inputs
5. Add hysteresis and overlap to U6 range
6. Add blocking FET to output of boost converter (U8)

Voltage Measurement System

1. Testing was done for the voltage divider (consisting of components R22 and R24).

V_BAT supplied was 24V. The measured output voltage recorded was about 2.907V.

2. U4 was also tested. The output voltage measured and recorded was about 2.908V.

Current Measurement System

1. Range 0: This range is good (within 0.5%)
  a. 119.9 uA -> 3.000 V
  b. 59.9 uA -> 1.496 V
  c. 89.9 uA -> 2.251 V
2. Range 1: This range functions but measurements are off
  a. 1.200 mA -> 2.922 V ~2% error
  b. 100.3 uA -> 250.5 mV This one is actually right on
  c. 120.1 uA -> 292.9 mV ~2% error
  d. 600.3 uA -> 1.366 V ~9% error
3. Range 2: This range is good
  a. 59.96 mA -> 1.487 V
  b. 120.0 mA -> 2.987 V
  c. 90.22 mA -> 2.243 V
4. Range 3: The readings were good, but there was significant heating
  a. 600 mA -> 150.3 mV
  b. 1.198 A -> 298.7 mV
  c. 2.003 A -> 0.500 V
  d. 3.002 A -> 0.750 V
  e. 4.003 A -> 1.001 V

Microcontroller/Firmware

1. DutISense.updateADCVal() timing
  a. 35 instruction cycles
  b. 583ns at 120MHz (1.7MHz)
2. ADC Sample Rate
  a. 152.6kHz (module)
  b. 76.3kHz (per channel)
