rmfharvey/EE4951_REPO/Python/ADC_TEST.csv

Count | ADC1 | ADC2
1 | 19849 | 19756
2 | 19878 | 19714
3 | 19888 | 19728
4 | 19826 | 19744
5 | 19872 | 19708
6 | 19871 | 19700
7 | 19912 | 19728
8 | 19858 | 19720
9 | 19902 | 19716
10 | 19840 | 19727
11 | 19873 | 19734
12 | 19864 | 19722
13 | 19877 | 19724
14 | 19874 | 19726
15 | 19875 | 19712
16 | 19880 | 19725
17 | 19884 | 19719
18 | 19896 | 19735
19 | 19892 | 19709
20 | 19880 | 19735
21 | 19880 | 19730
22 | 19851 | 19708
23 | 19896 | 19720
24 | 19883 | 19699
25 | 19872 | 19713
26 | 19848 | 19715
27 | 19876 | 19732
28 | 19869 | 19739
29 | 19892 | 19751
30 | 19843 | 19739
31 | 19898 | 19725
32 | 19854 | 19731
33 | 19873 | 19732
34 | 19884 | 19694
35 | 19896 | 19728
36 | 19864 | 19720
37 | 19871 | 19728
38 | 19856 | 19705
39 | 19848 | 19724
40 | 19880 | 19728
41 | 19881 | 19742
42 | 19876 | 19726
43 | 19869 | 19748
44 | 19828 | 19726
45 | 19892 | 19739
46 | 19871 | 19720
47 | 19883 | 19740
48 | 19864 | 19722
49 | 19886 | 19732
50 | 19872 | 19712
51 | 19893 | 19724
52 | 19854 | 19755
53 | 19877 | 19729
54 | 19884 | 19733
55 | 19862 | 19710
56 | 19881 | 19731
57 | 19874 | 19743
58 | 19857 | 19848
59 | 19858 | 19795
60 | 19834 | 19785
61 | 19829 | 19787
62 | 19878 | 19790
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
