rmfharvey/EE4951_REPO/Documentation/Nimbelink Device Power Profile/Battery Voltage Measurement 1.png

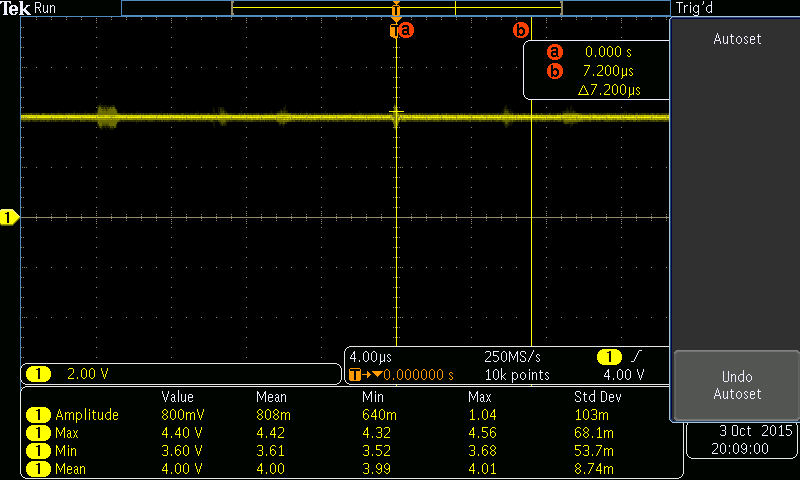
Documentation/Nimbelink Device Power Profile/Battery Voltage Measurement 1.png
