rmfharvey/EE4951_REPO/Documentation/Nimbelink Device Power Profile/Current Shunt (Voltage) Measurement 2.png

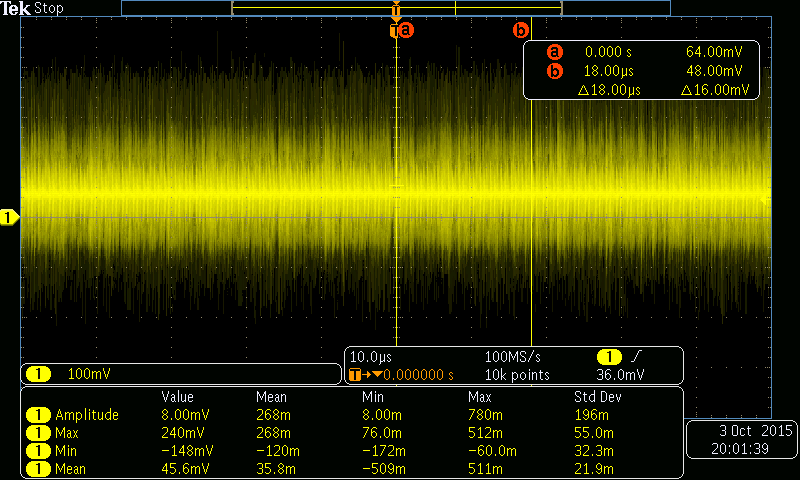
Documentation/Nimbelink Device Power Profile/Current Shunt (Voltage) Measurement 2.png
