rmfharvey/EE4951_REPO/Documentation/Nimbelink Device Power Profile/Current Shunt (Voltage) Measurement 6.png

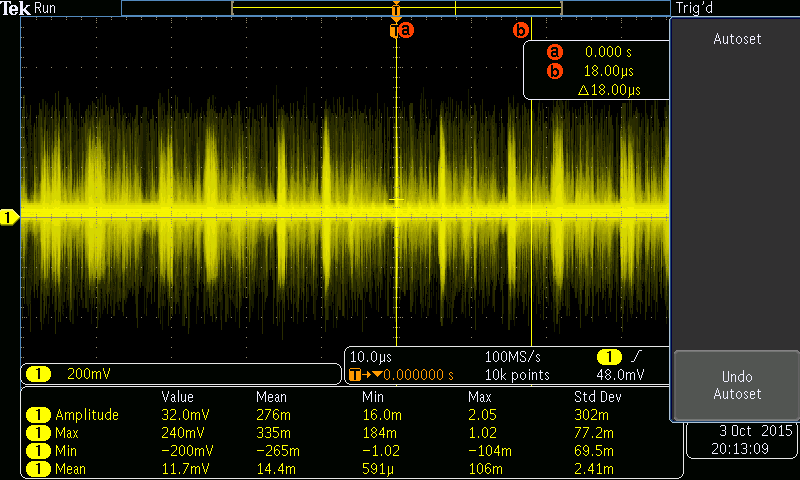
Documentation/Nimbelink Device Power Profile/Current Shunt (Voltage) Measurement 6.png
