rmfharvey/EE4951_REPO/Documentation/Firmware Toolchain/FRDM-K22F/SPF-28164_D.pdf

Table of Contents | Revisions & Change Log
X1 | Initial Draft

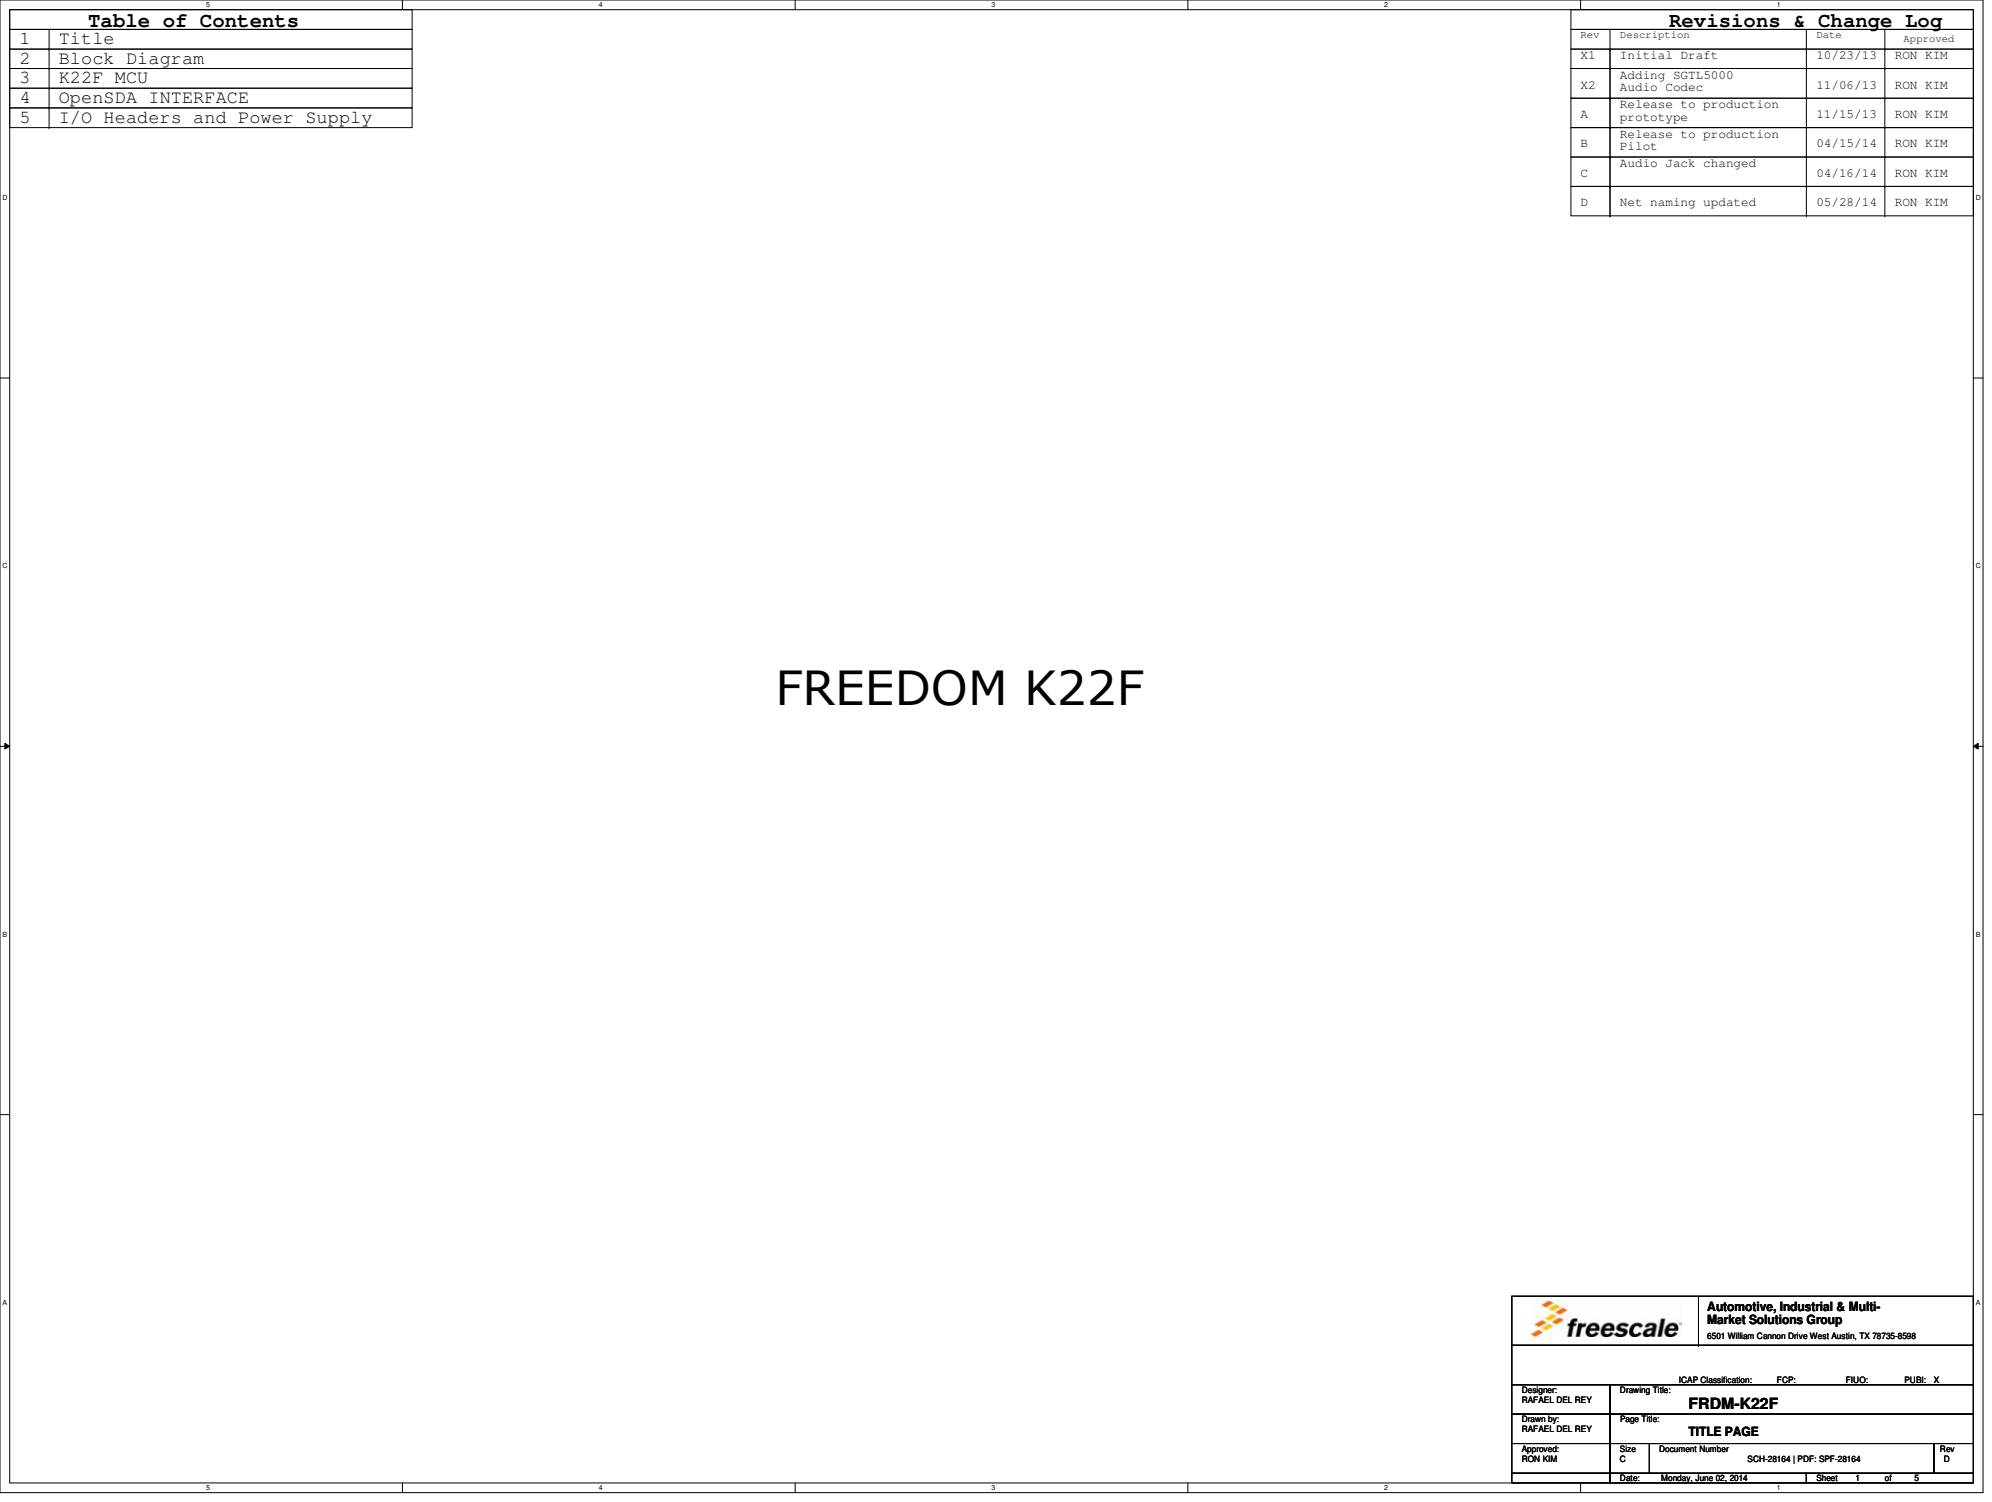
[picture p127: page 1]
Rev; Description; Approved RON KIM; Date; Block Diagram; Title; OpenSDA INTERFACE; K22F MCU; I/O Headers and Power Supply; FREEDOM K22F; Adding SGTL5000 Audio Codec; RON KIM; prototype; Pilot; Audio Jack changed; Net naming updated; Drawing Title:; Size; Document Number; Date:; Sheet; Page Title:; Approved:; ICAP Classification:; FCP:; FIUO:; PUBI:; SCH-28164 | PDF: SPF-28164; FRDM-K22F; Monday, June 02, 2014; TITLE PAGE; X Drawing Title: Size; Rev Date: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

Release to production

Automotive, Industrial & Multi-
Market Solutions Group

6501 William Cannon Drive West Austin, TX 78735-8598

Designer:
RAFAEL DEL REY

Drawn by:

# 1. Unless Otherwise Specified: All resistors are in ohms, 5%, 1/8 Watt

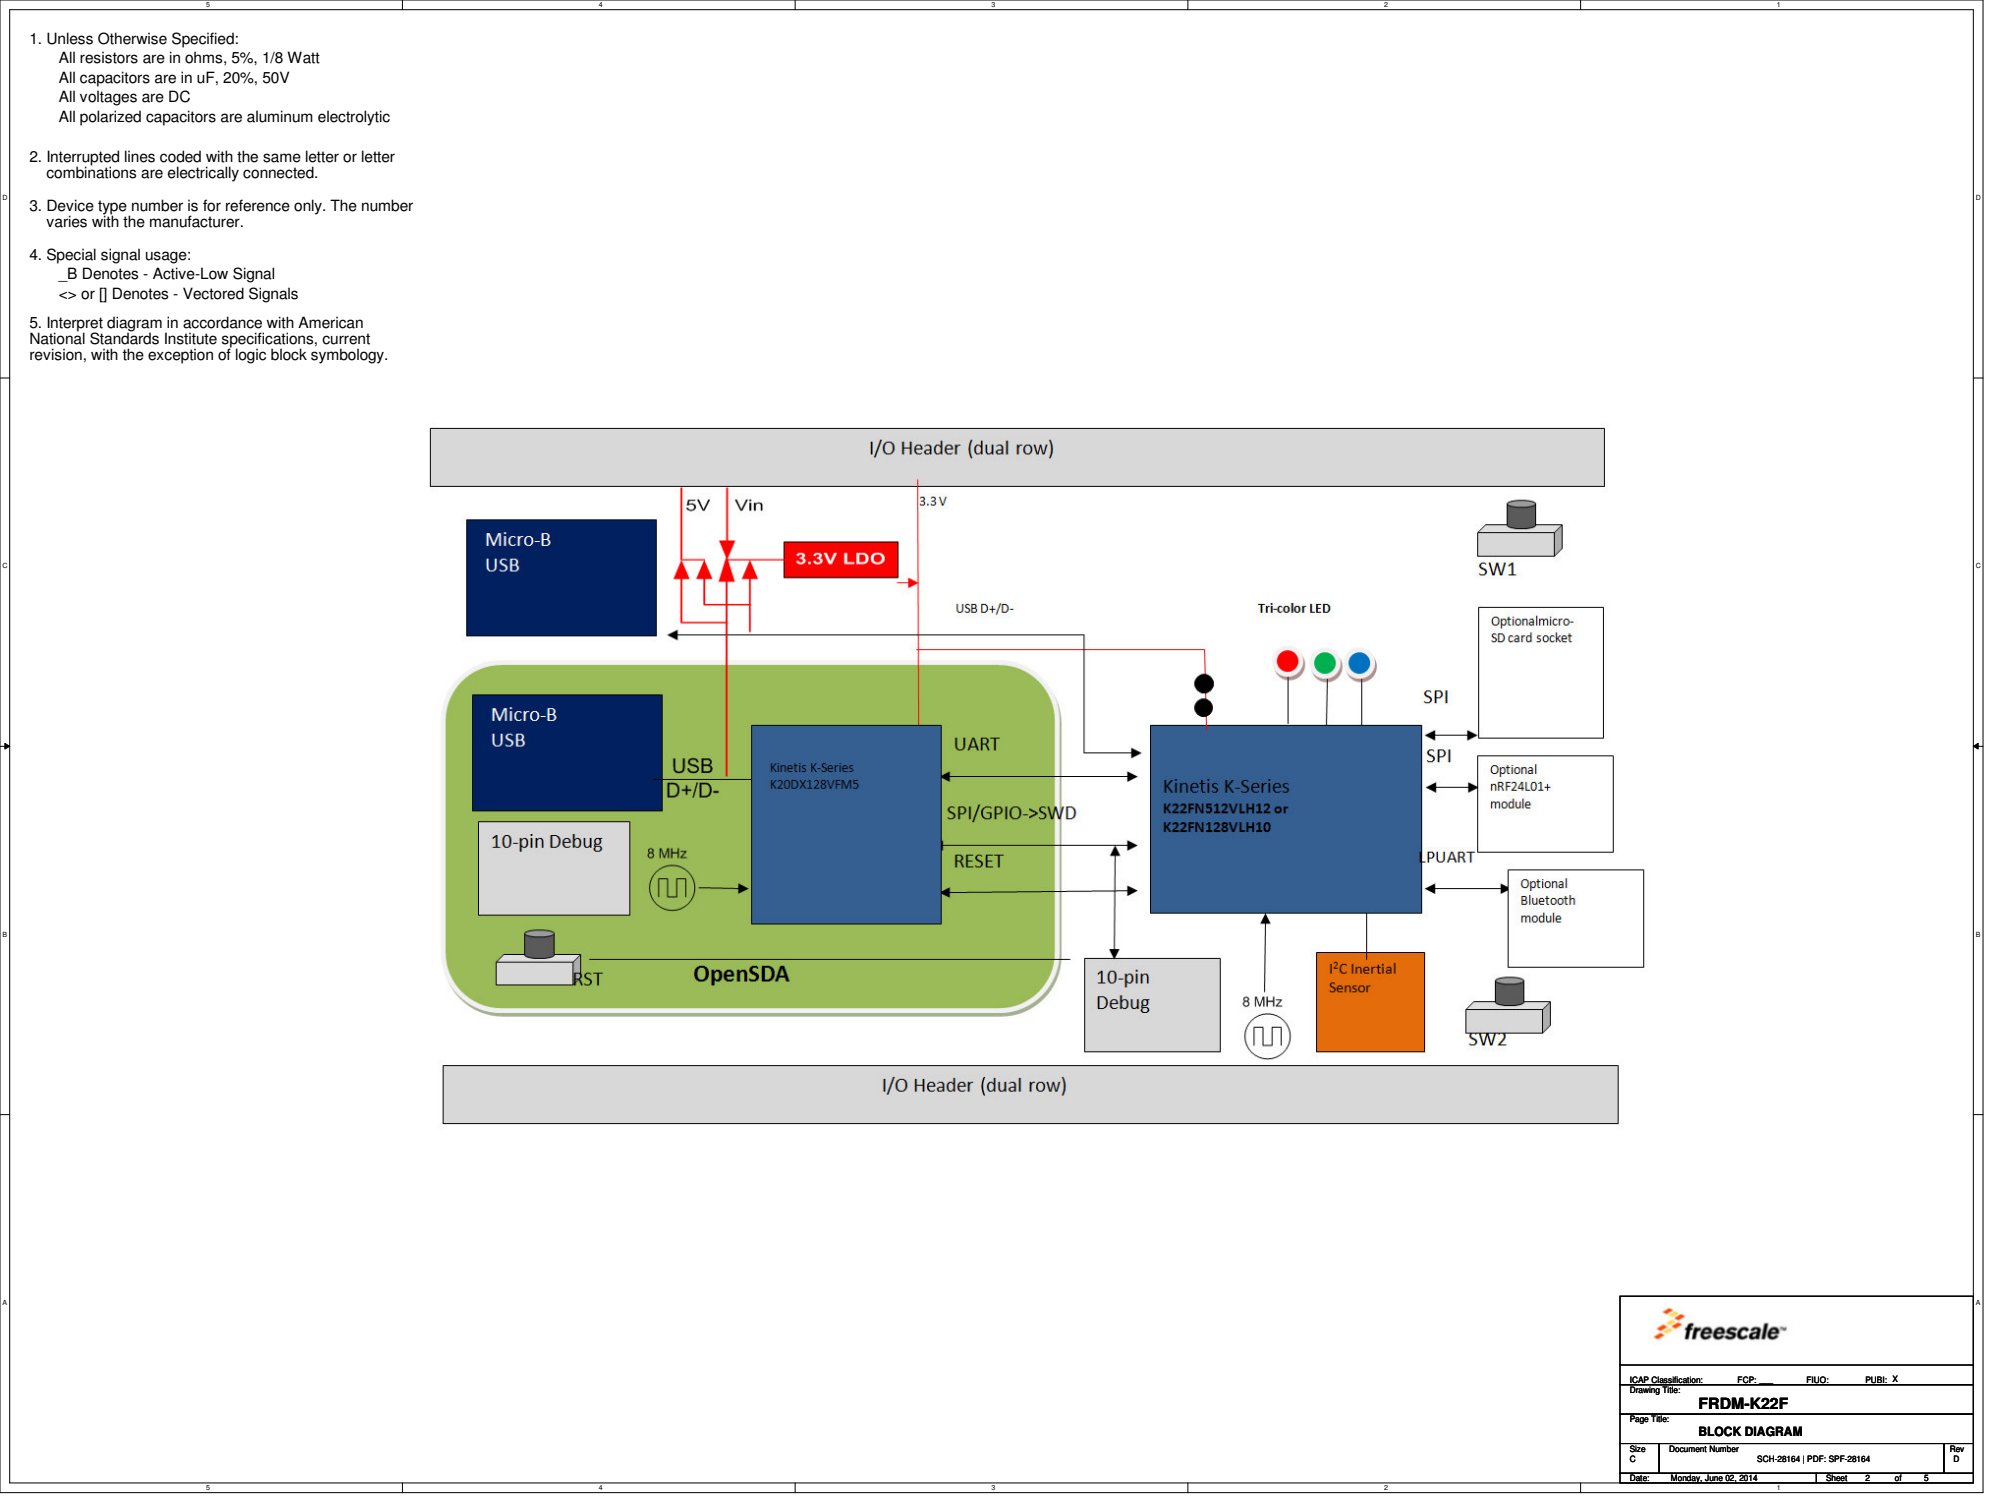
[picture p128: page 2]
Drawing Title:; ICAP Classification:; FCP:; FIUO:; PUBI:; FRDM-K22F; BLOCK DIAGRAM; X ___ Drawing Title:

All capacitors are in uF, 20%, 50V
All voltages are DC
All polarized capacitors are aluminum electrolytic

2. Interrupted lines coded with the same letter or letter
combinations are electrically connected.

3. Device type number is for reference only. The number
varies with the manufacturer.

4. Special signal usage:
_B Denotes - Active-Low Signal
<> or [] Denotes - Vectored Signals

5. Interpret diagram in accordance with American
National Standards Institute specifications, current
revision, with the exception of logic block symbology.

# K22F DECOUPLING CAPS

# K22F USB CONNECTOR

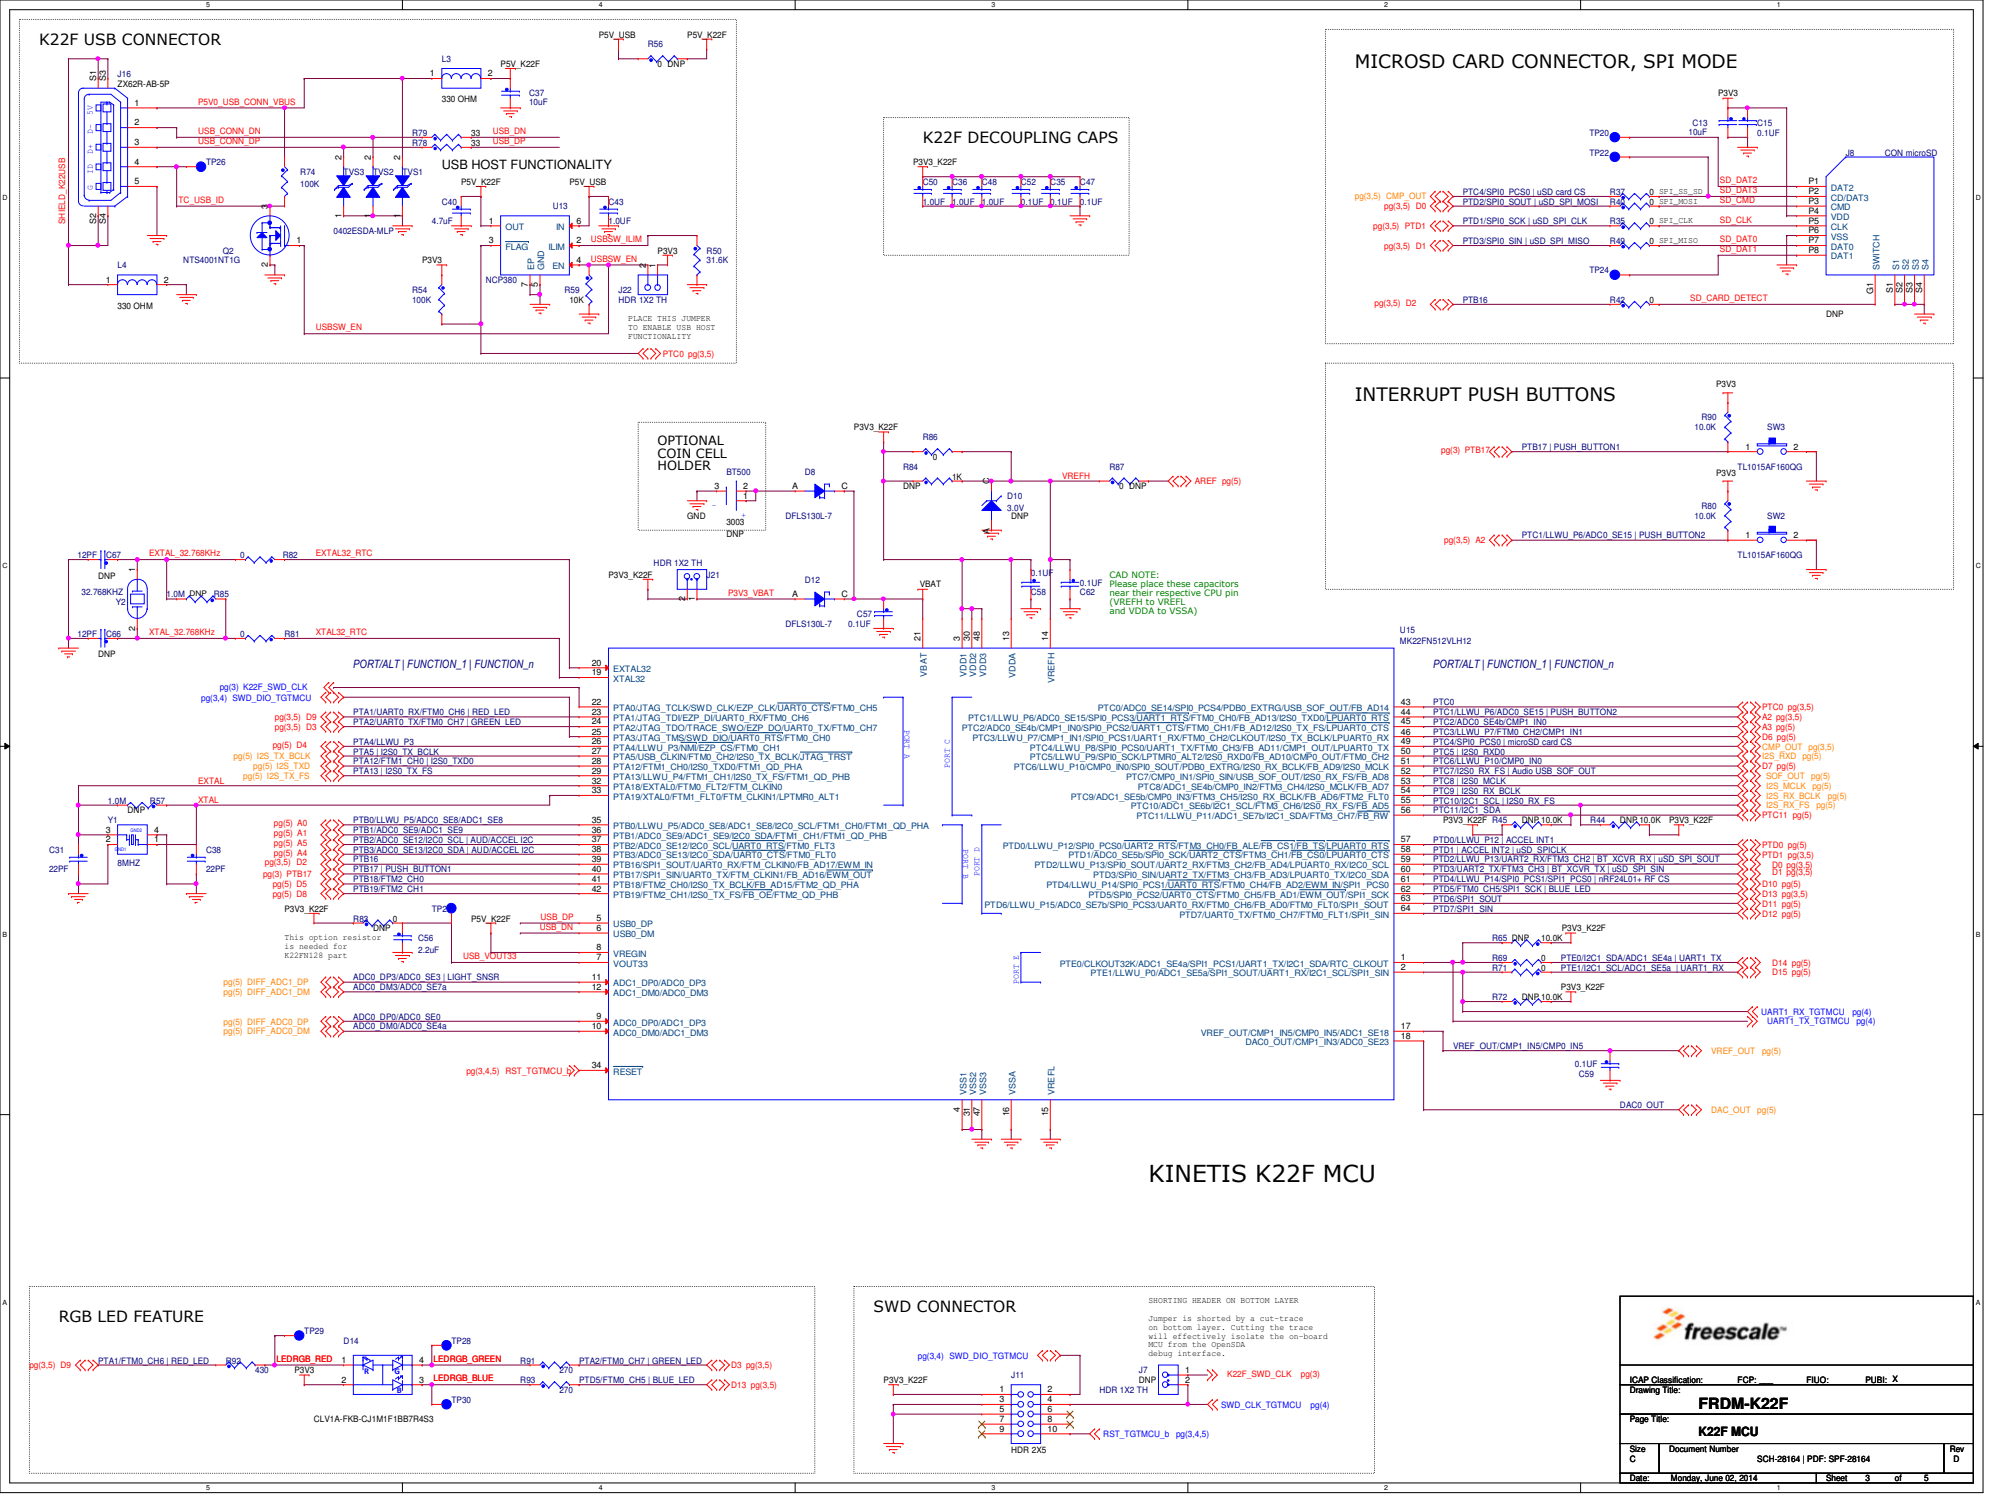
[picture p129: page 3]

MICROSD CARD CONNECTOR, SPI MODE

PLACE THIS JUMPER
TO ENABLE USB HOST
FUNCTIONALITY

CAD NOTE:
Please place these capacitors
near their respective CPU pin
(VREFH to VREFL
and VDDA to VSSA)

SHORTING HEADER ON BOTTOM LAYER

Jumper is shorted by a cut-trace
on bottom layer. Cutting the trace
will effectively isolate the on-board
MCU from the OpenSDA
debug interface.
DNP

# OpenSDA Interface

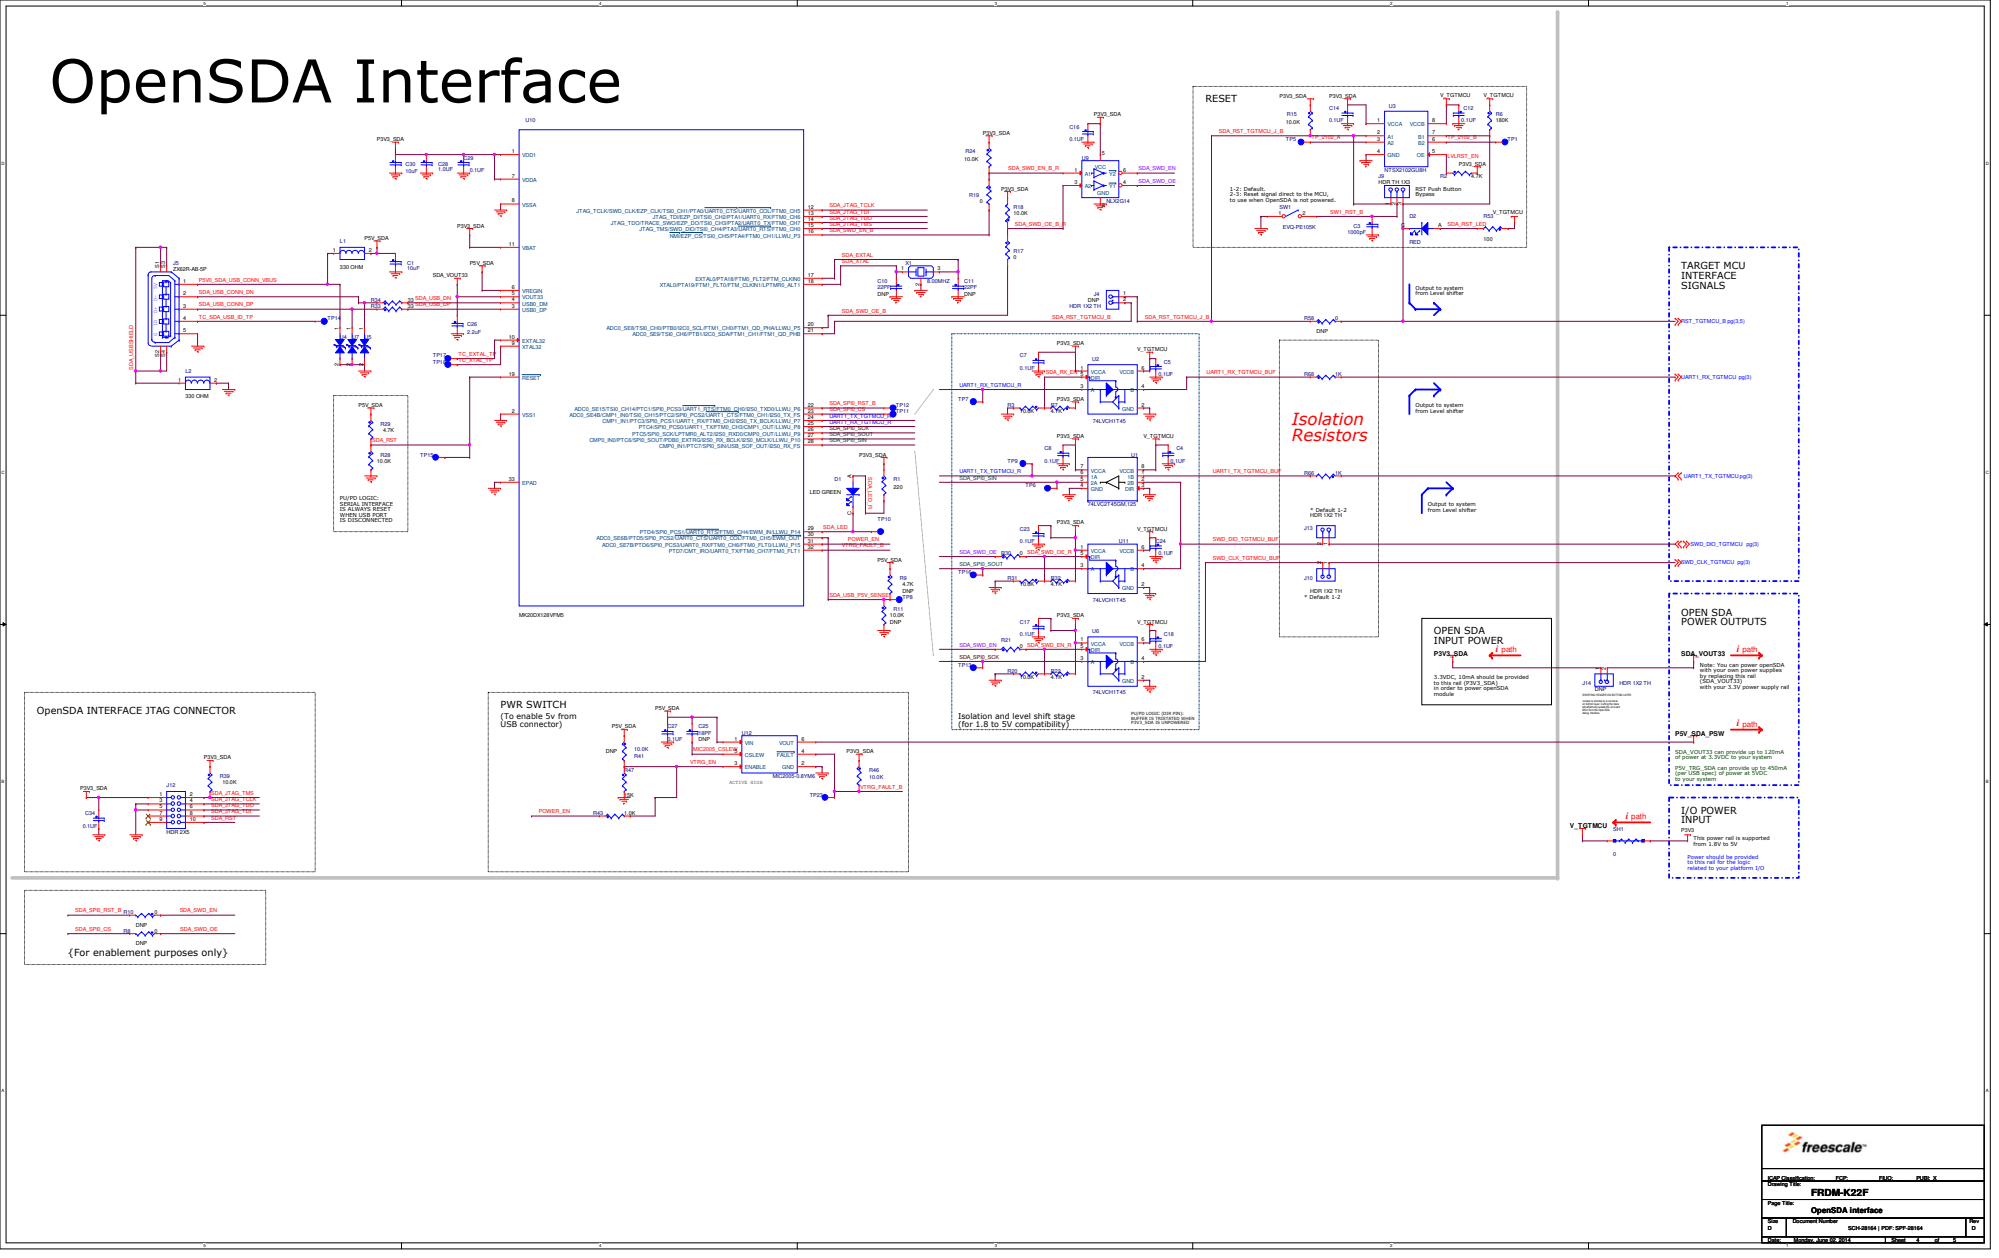
[picture p130: page 4]

1-2: Default.
2-3: Reset signal direct to the MCU,
to use when OpenSDA is not powered.

HW Designer: Rafael del Rey

3.3VDC, 10mA should be provided
to this rail (P3V3_SDA)
in order to power openSDA
module

Note: You can power openSDA
with your own power supplies
by replacing this rail
(SDA_VOUT33)
with your 3.3V power supply rail

SHORTING HEADER ON BOTTOM LAYER

OpenSDA INTERFACE JTAG CONNECTOR

PWR SWITCH
P3V3_SDA IS UNPOWERED (To enable 5v from USB connector)

Isolation and level shift stage
(for 1.8 to 5V compatibility)

PU/PD LOGIC (DIR PIN):
BUFFER IS TRISTATED WHEN

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

SDA_VOUT33 can provide up to 120mA
of power at 3.3VDC to your system

P5V_TRG_SDA can provide up to 450mA
(per USB spec) of power at 5VDC
to your system

This power rail is supported
from 1.8V to 5V

Power should be provided
to this rail for the logic
related to your platform I/O

{For enablement purposes only}

# FREEDOM PLATFORM COMPATIBILITY HEADERS

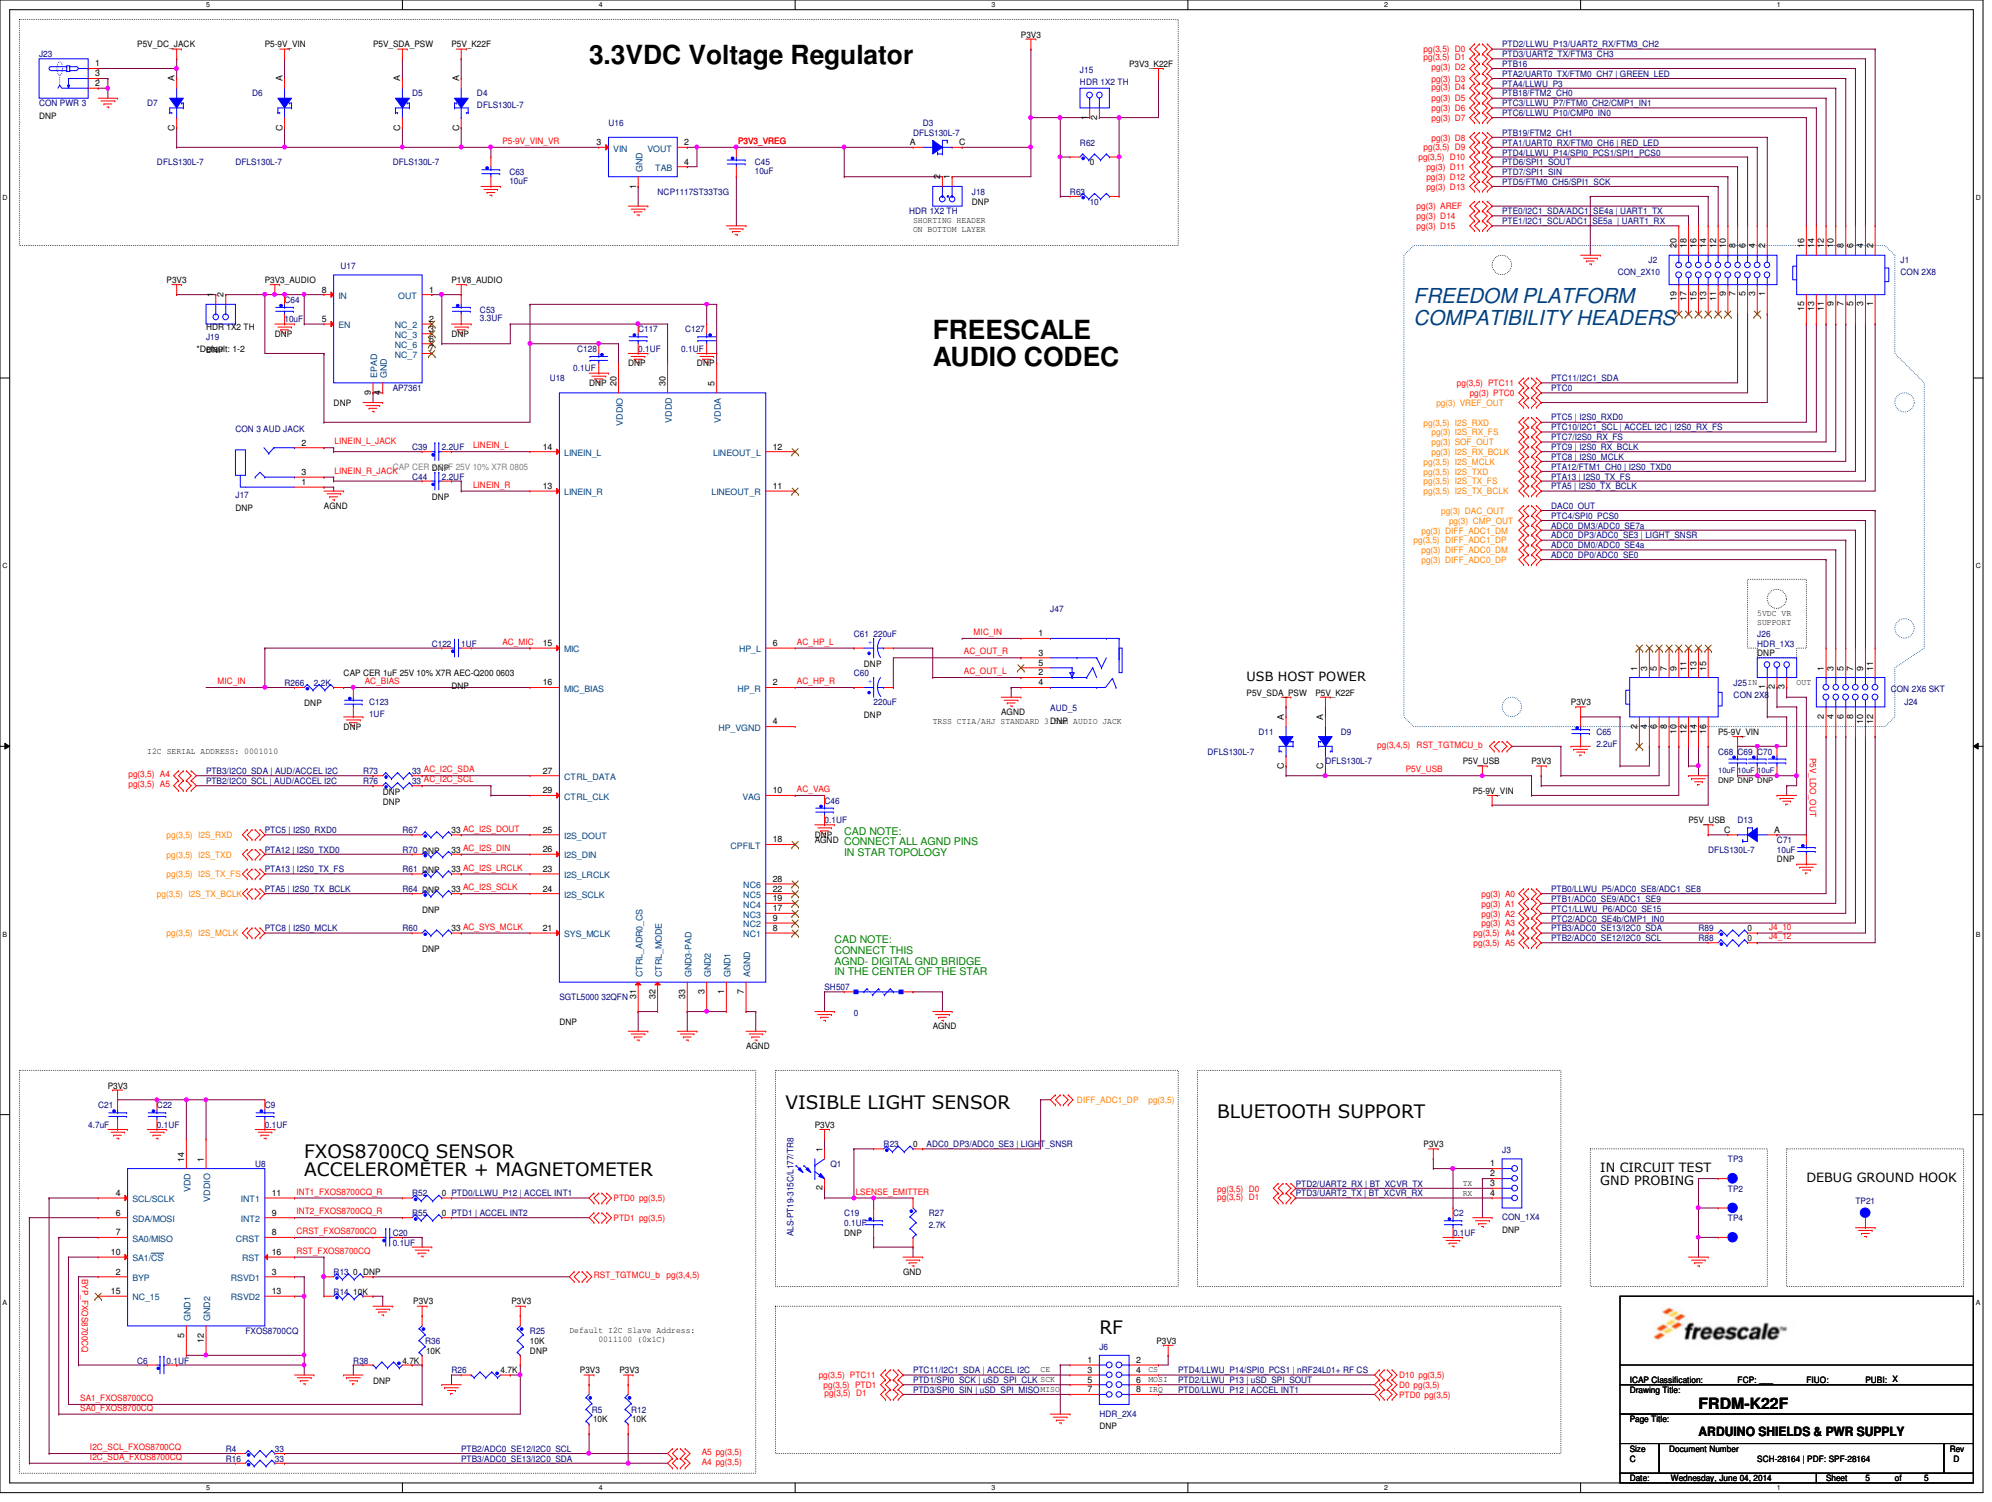
[picture p131: page 5]

TRSS CTIA/AHJ STANDARD 3.5mm AUDIO JACK

CAD NOTE:
CONNECT ALL AGND PINS
IN STAR TOPOLOGY

CONNECT THIS
AGND- DIGITAL GND BRIDGE
IN THE CENTER OF THE STAR

ARDUINO SHIELDS & PWR SUPPLY
