rmfharvey/EE4951_REPO/PCBA/EE4951_BPM_REV_A/EE4951_BPM_REV_A.pdf

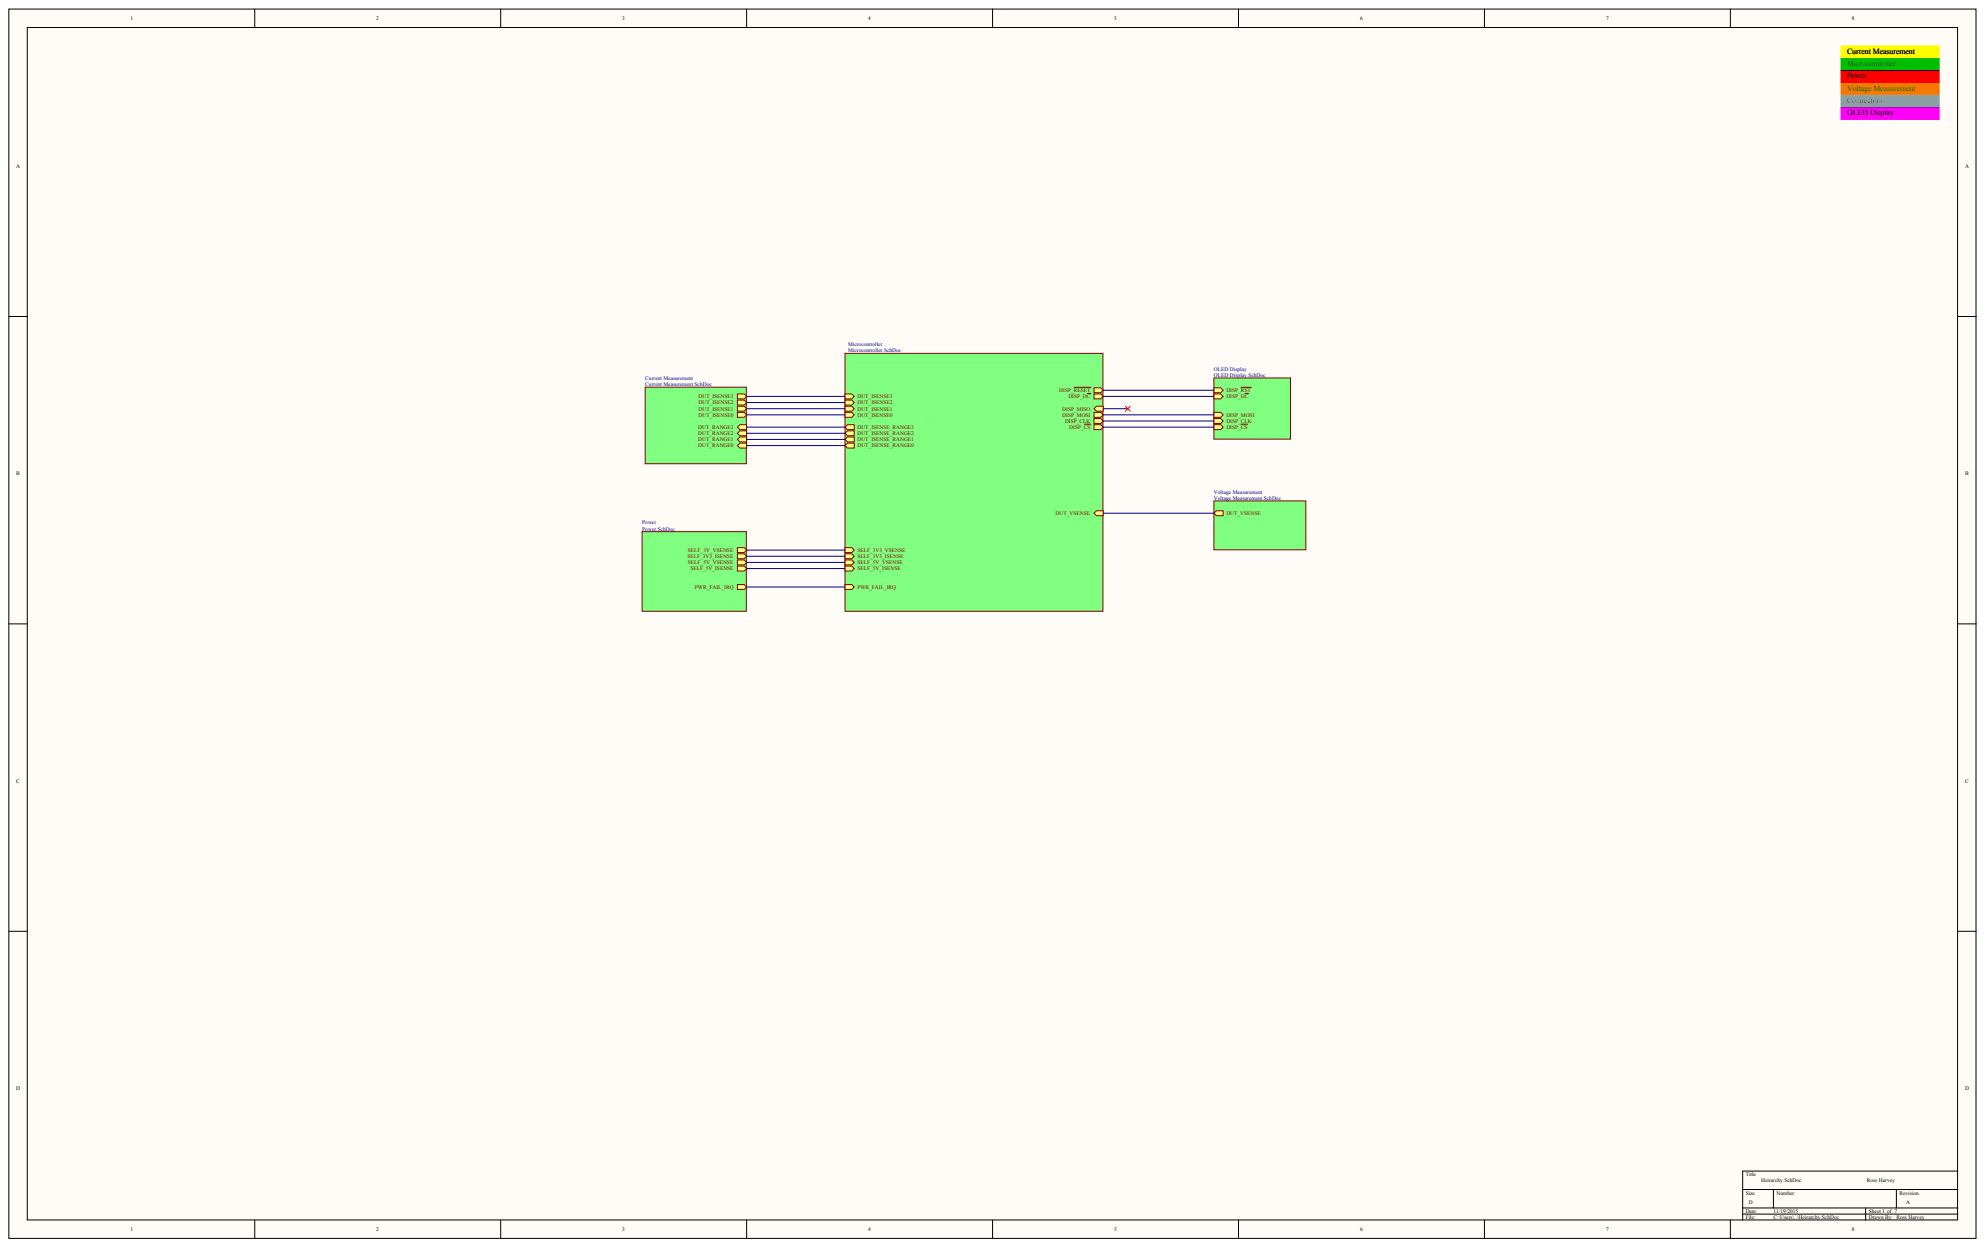
[picture p132: page 1]

Size D | Number | Revision A

Date: 11/19/2015 File: C:\Users\..\Heirarchy.SchDoc | Sheet 1 of 7 Drawn By: Ross Harvey

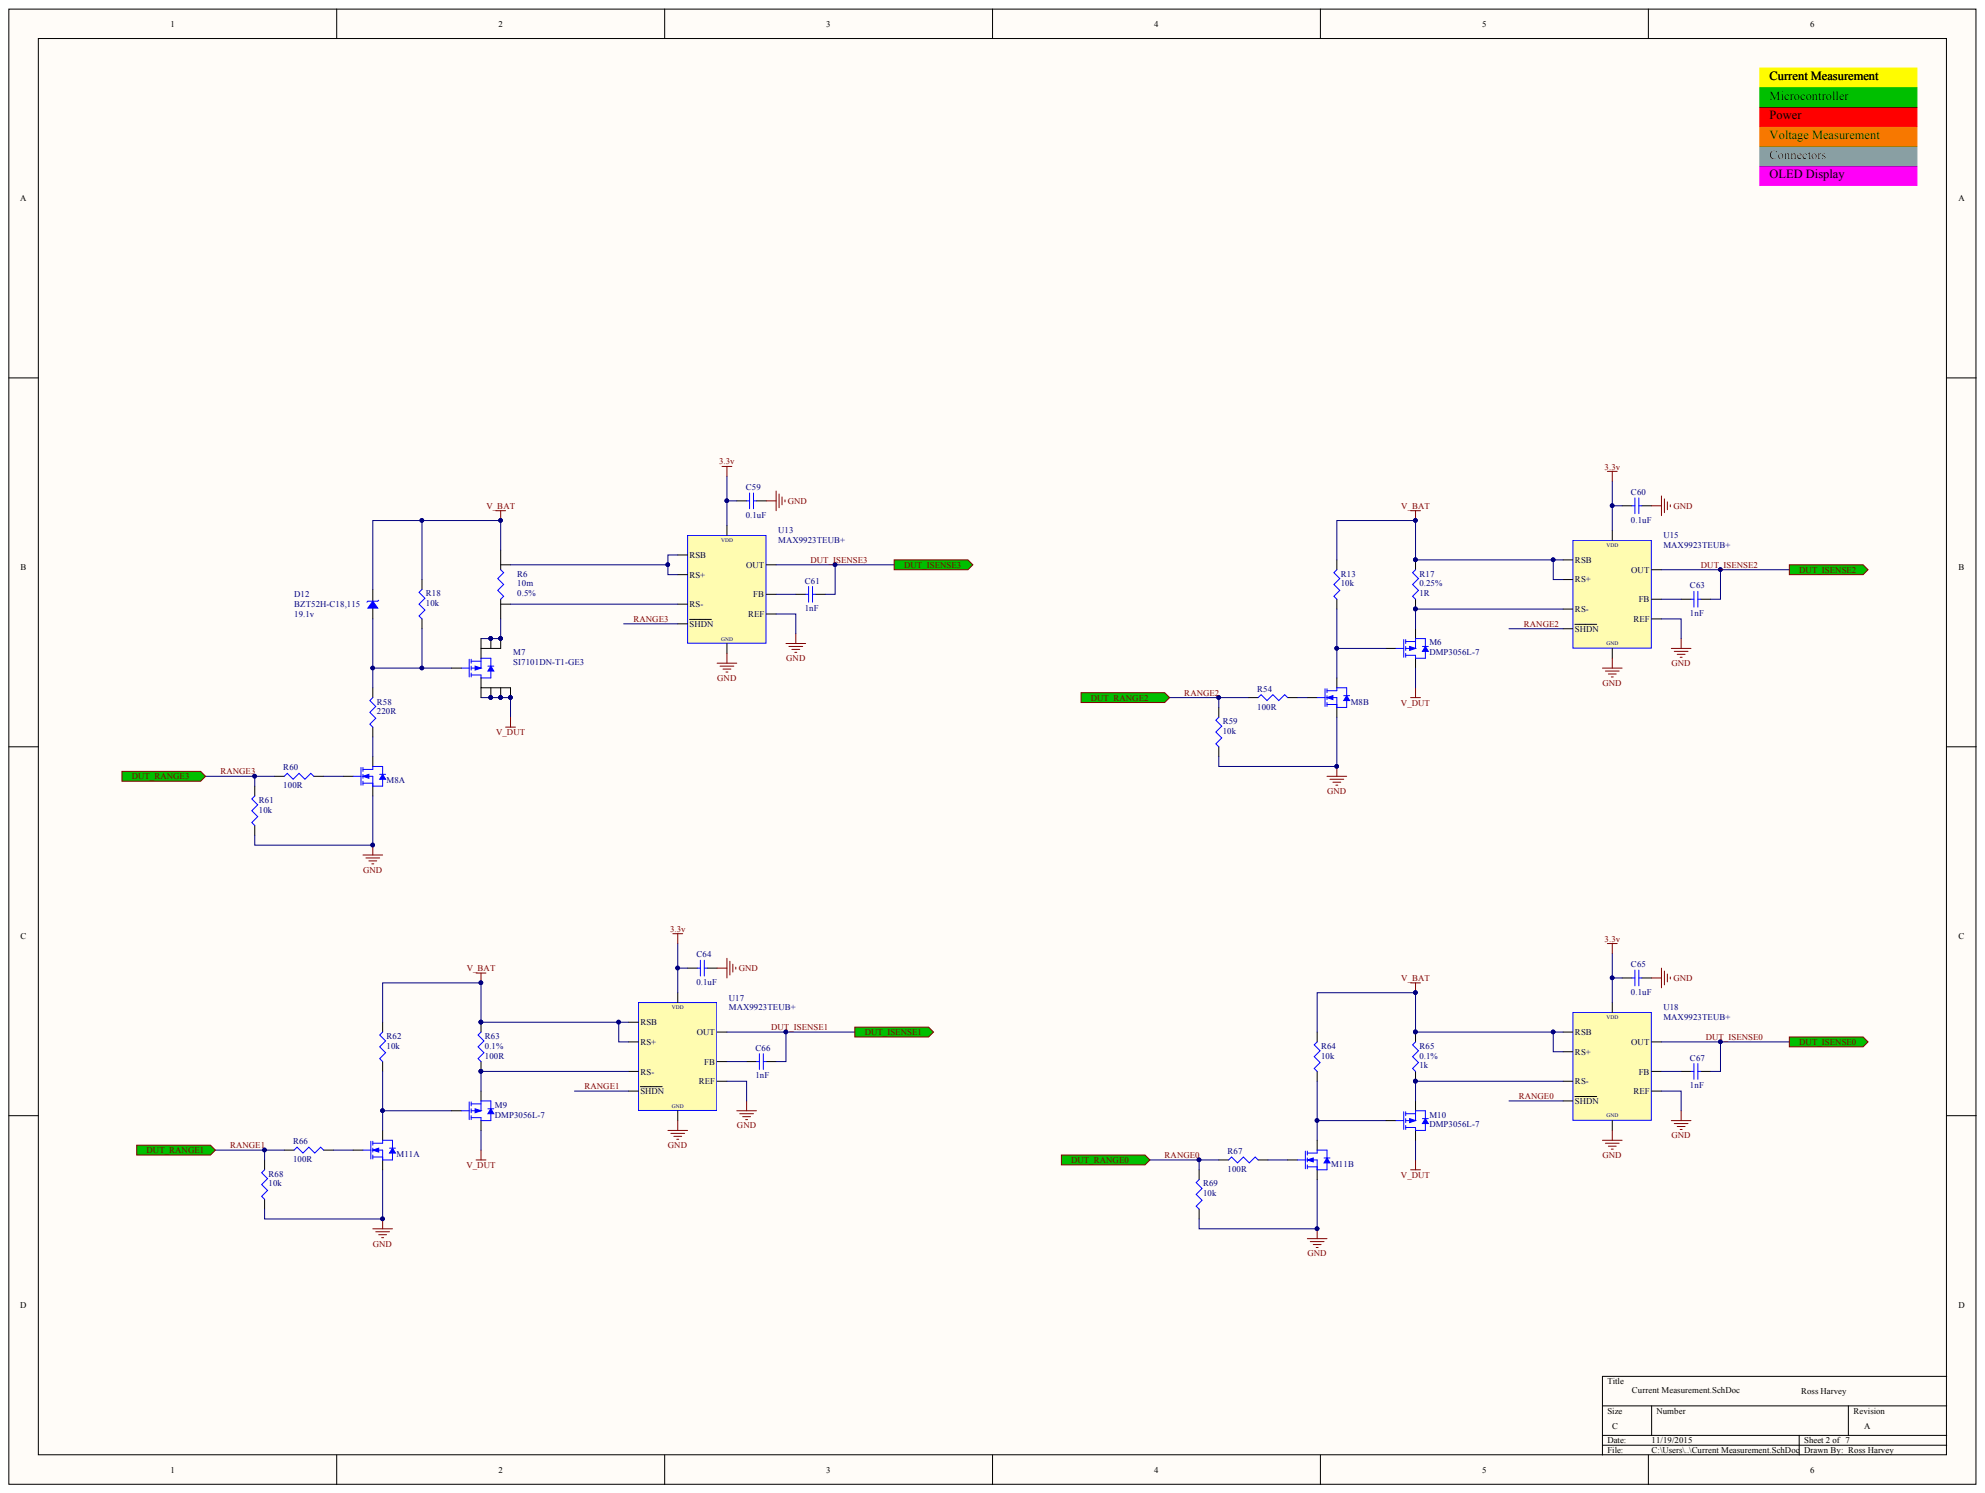
[picture p133: page 2]

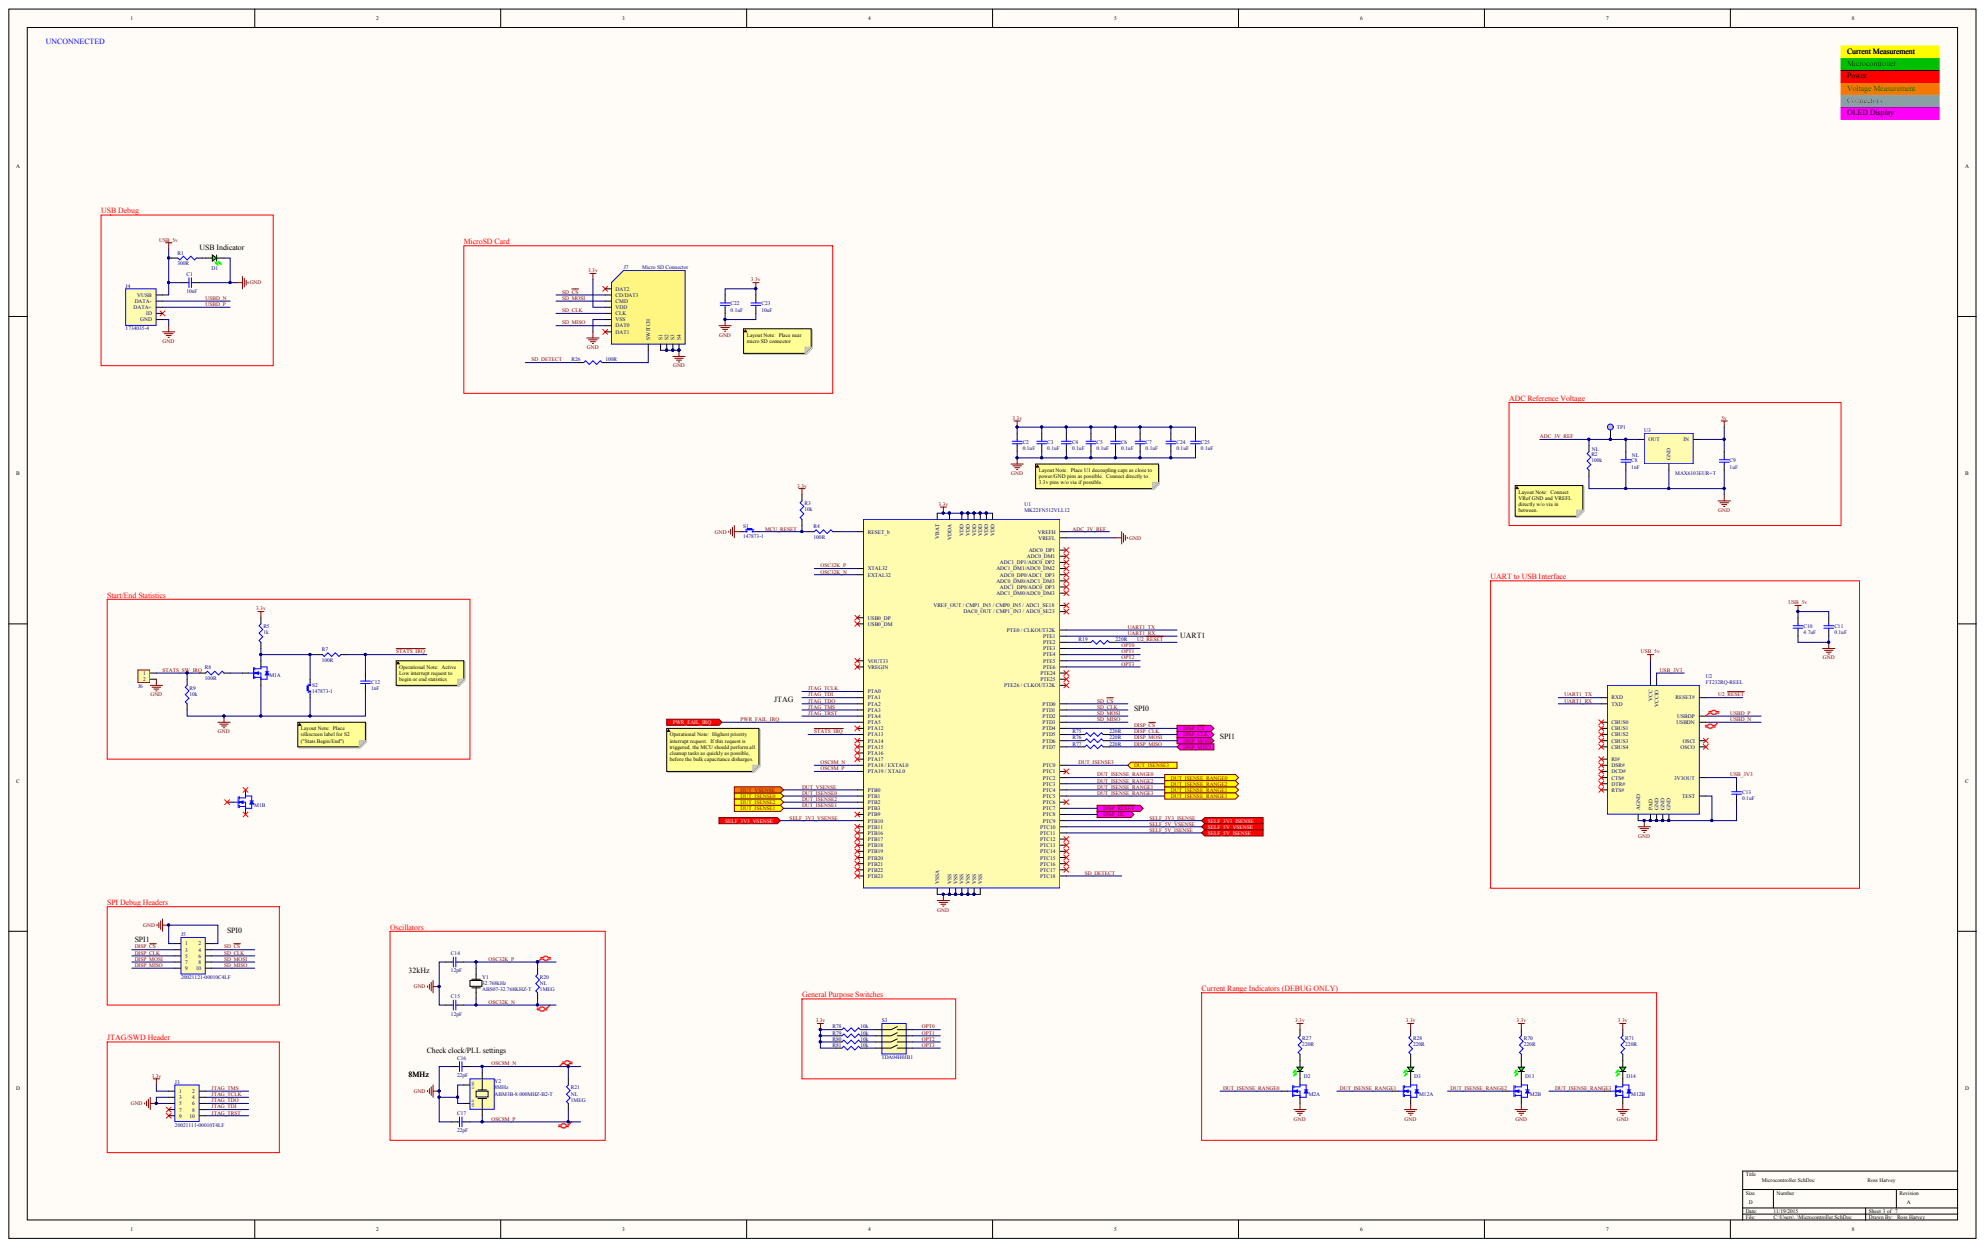
[picture p134: page 3]

Layout Note: Place near
micro SD connector

Layout Note: Place U1 decoupling caps as close to
power/GND pins as possible. Connect directly to
3.3v pins w/o via if possible.

Layout Note: Connect
VRef GND and VREFL
directly w/o via in
between.

UART to USB Interface

Operational Note: Active
Low interrupt request to
begin or end statistics

Operational Note: Highest priority
interrupt request. If this request is
triggered, the MCU should perform all
cleanup tasks as quickly as possible,
before the bulk capacitance disharges.

Current Range Indicators (DEBUG ONLY)

Check clock/PLL settings

Size D | Number | Revision A

Date: 11/19/2015 File: C:\Users\..\Microcontroller.SchDoc | Sheet 3 of 7 Drawn By: Ross Harvey

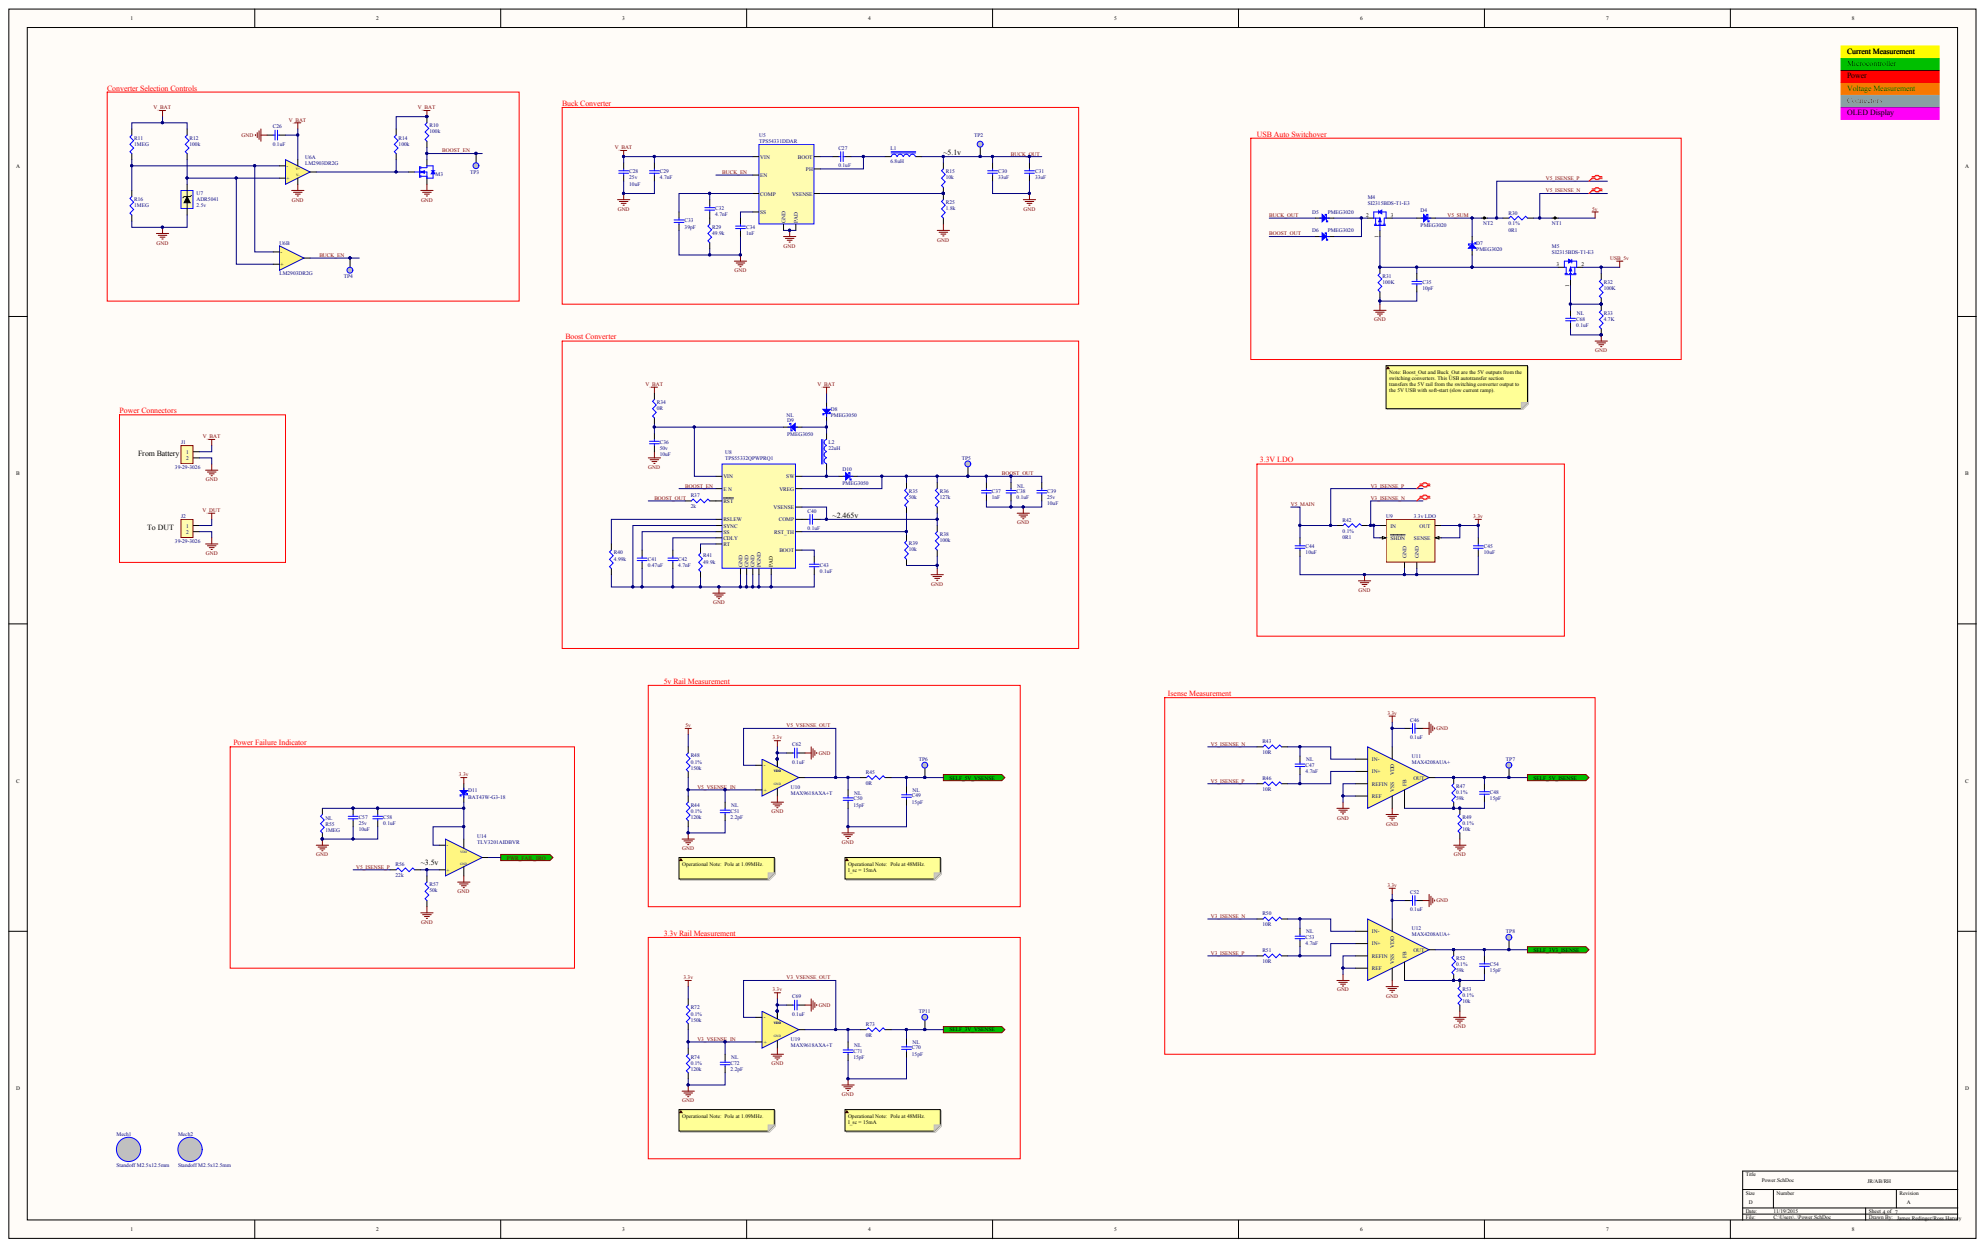
[picture p135: page 4]

Note: Boost_Out and Buck_Out are the 5V outputs from the
switching converters. This USB autotransfer section
transfers the 5V rail from the switching converter output to
the 5V USB with soft-start (slow current ramp).

Size D | Number | Revision A

Date: 11/19/2015 File: C:\Users\..\Power.SchDoc | Sheet 4 of 7 Drawn By: James Redinger/Ross Harvey

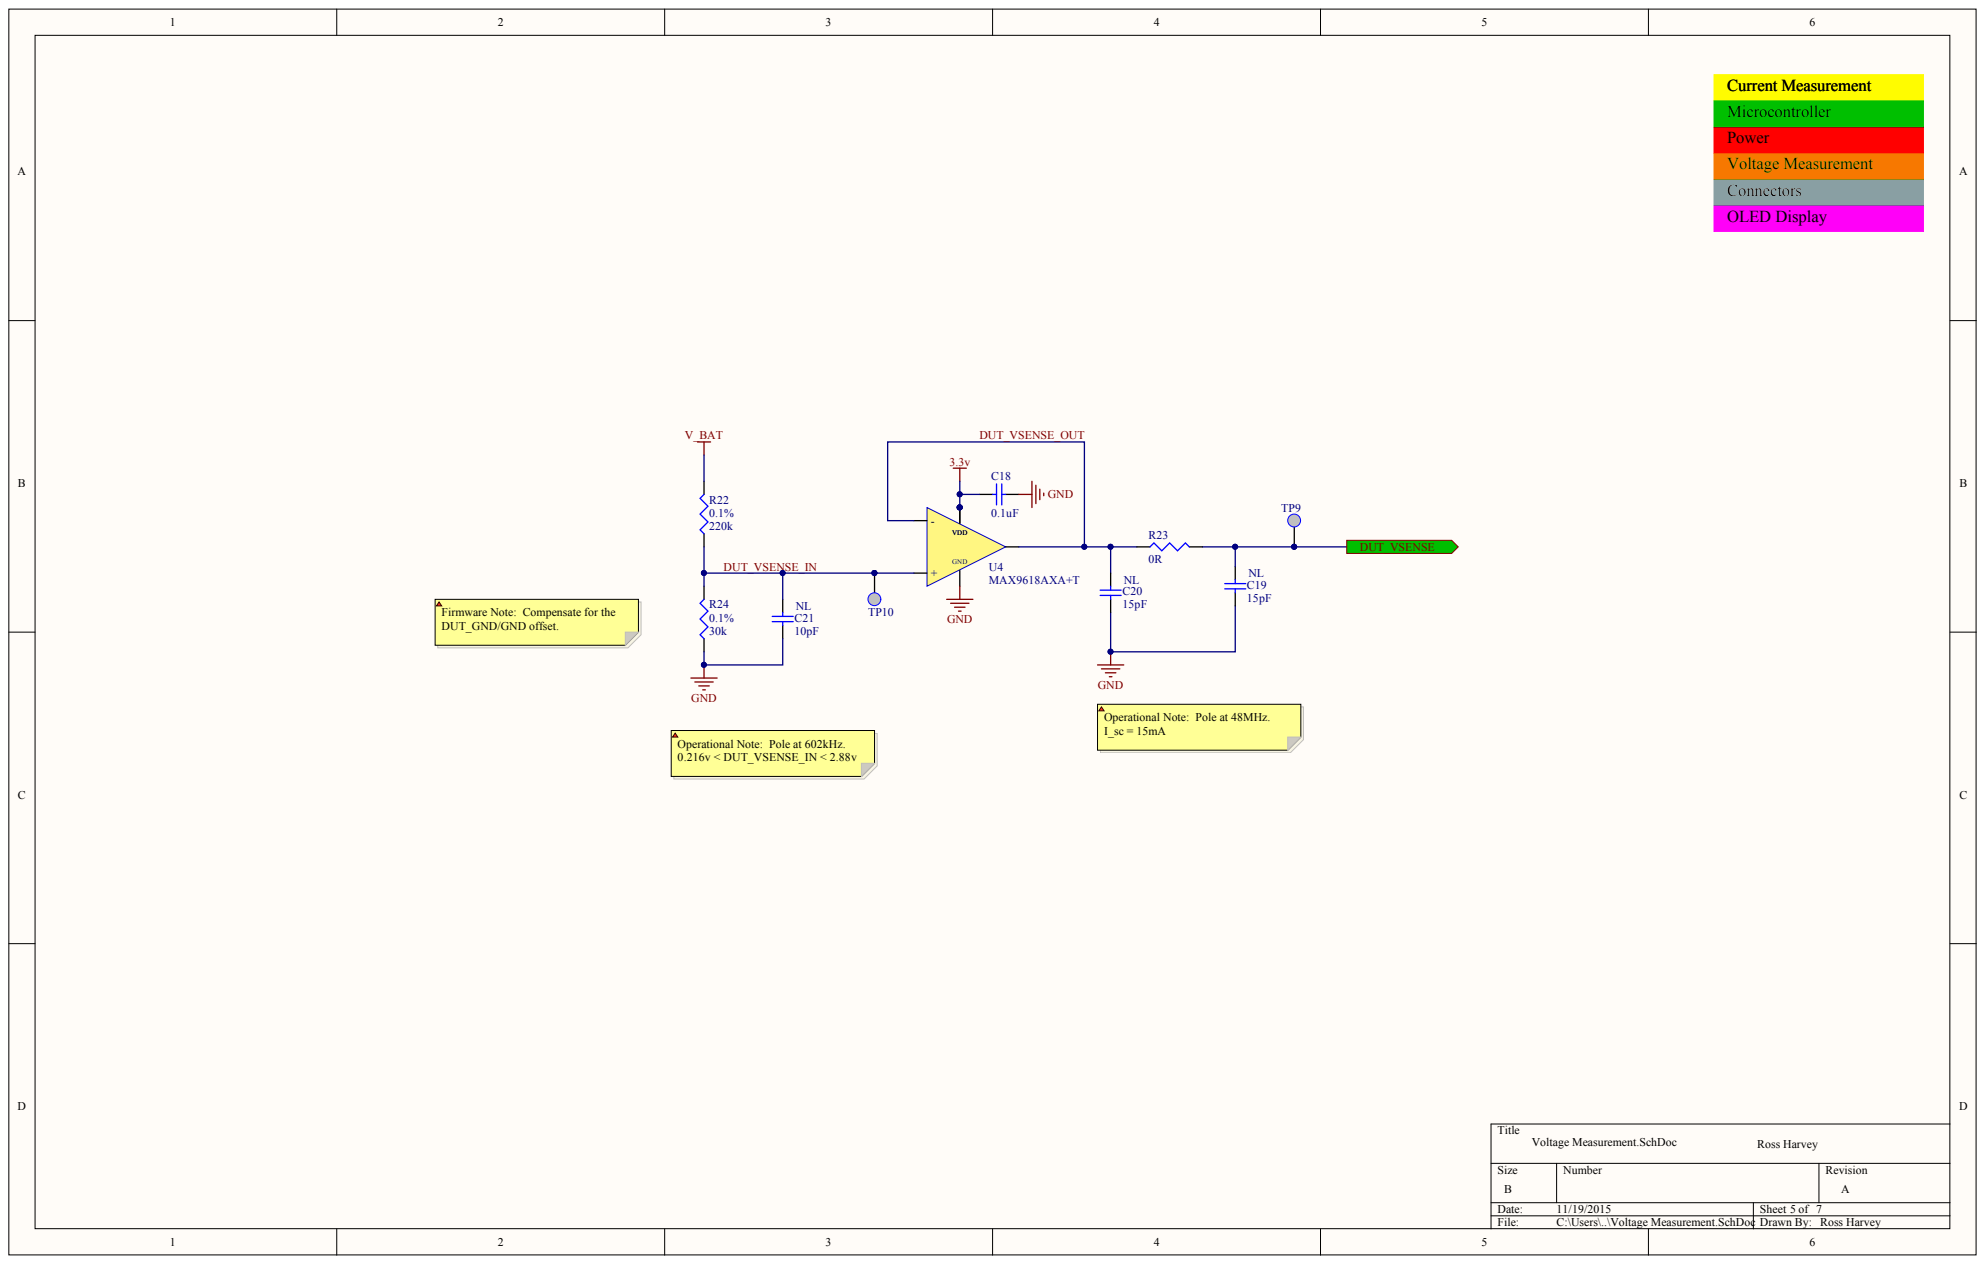
[picture p136: page 5]

Firmware Note: Compensate for the
DUT_GND/GND offset.

nal Note: Pole at 4

nal Note: Pole at 6

Size B | Number | Revisio n A

Date: 1 1/1 9/2 0 1 5 | Sheet o 5 f 7
File: C:\Users\..\Voltage Measurement.SchDo | c Drawn By : Ross Harvey

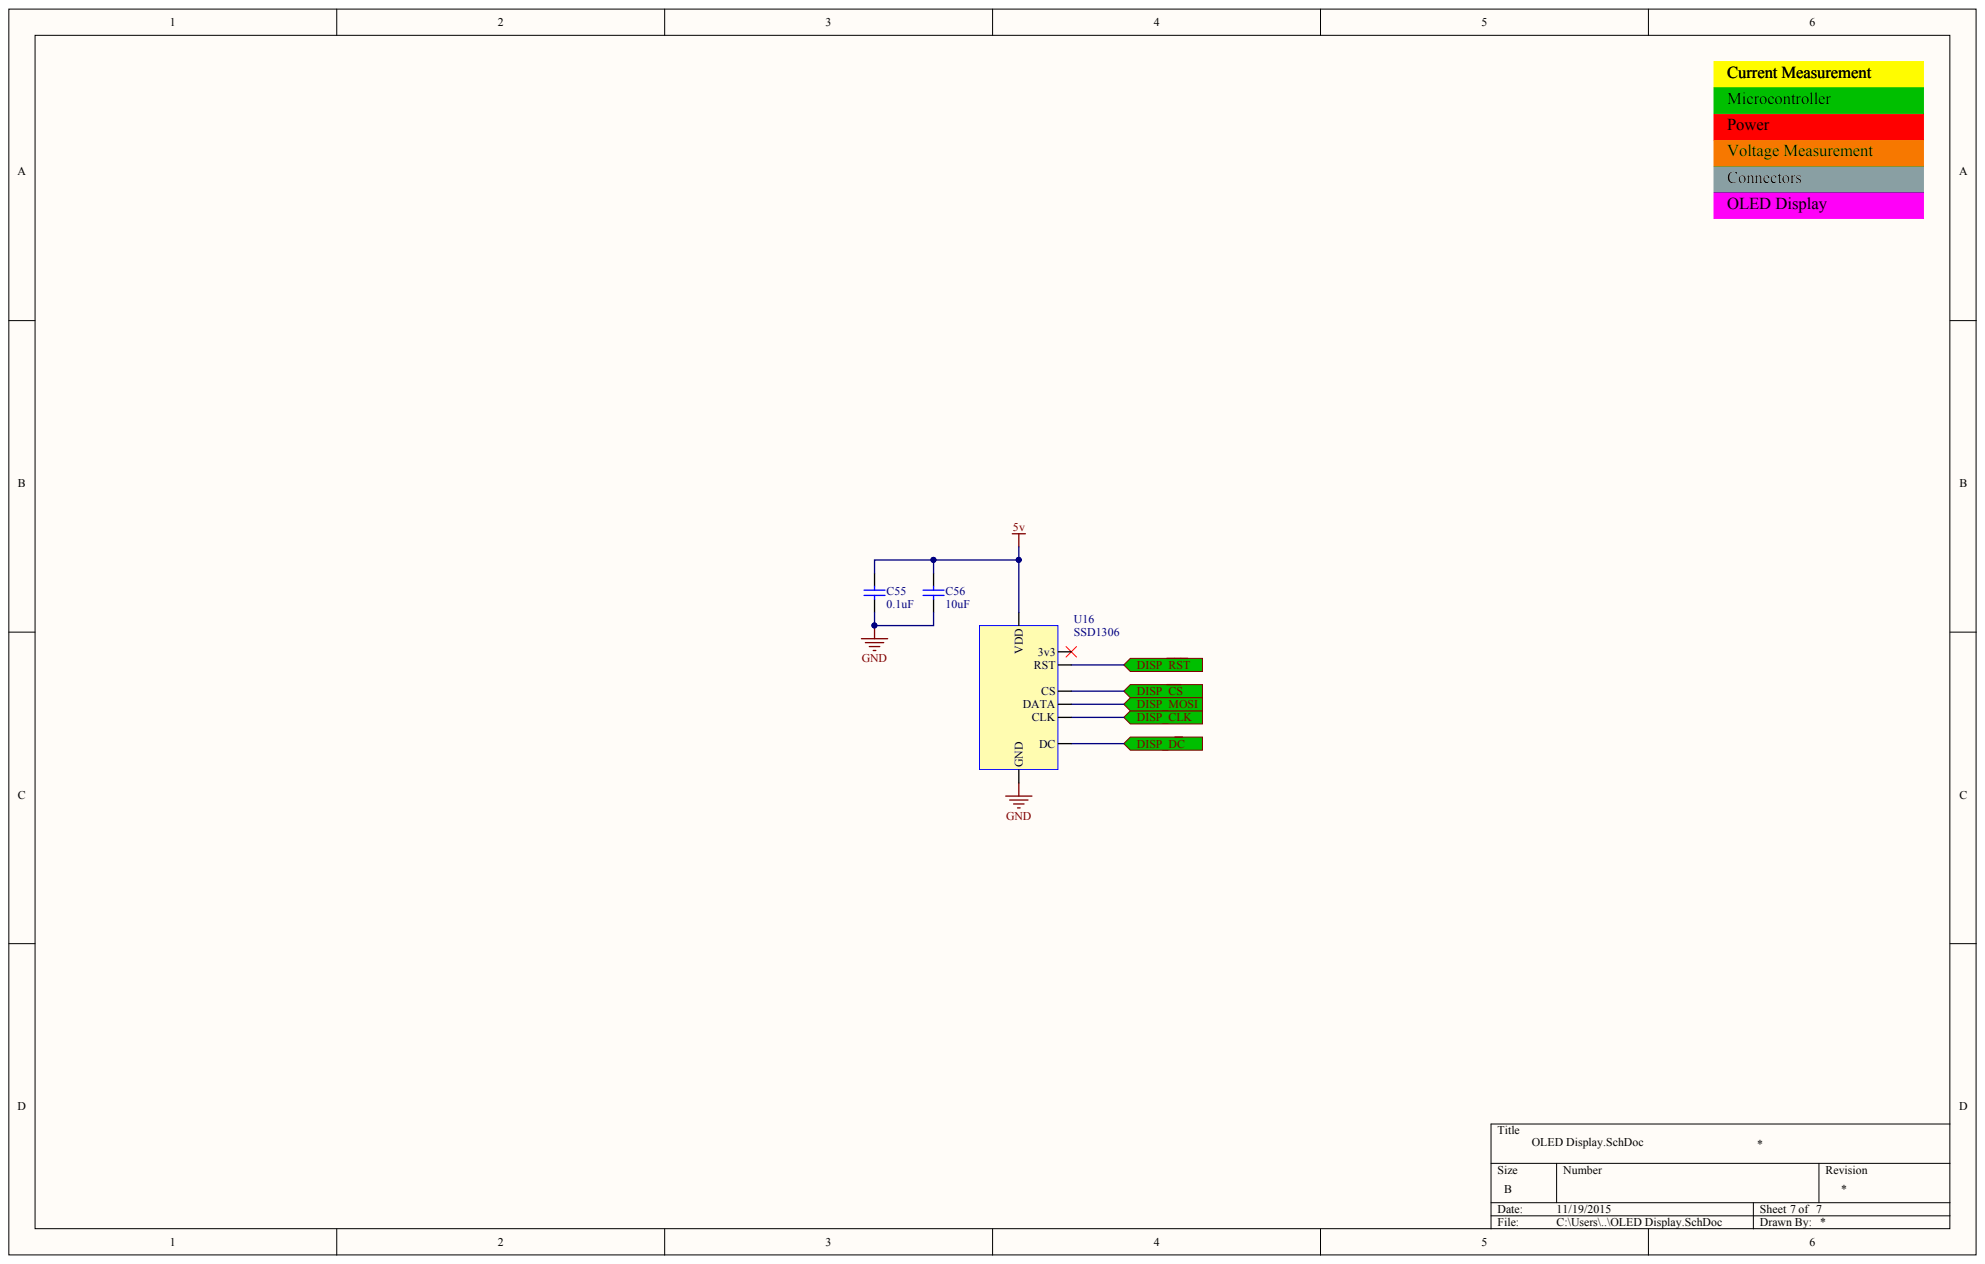
[picture p137: page 6]

Size B | Number | Revision *

Date: 11/19/2015 | Sheet of 7 7
File: C:\Users\..\OLED Display.SchDoc | Drawn By: *

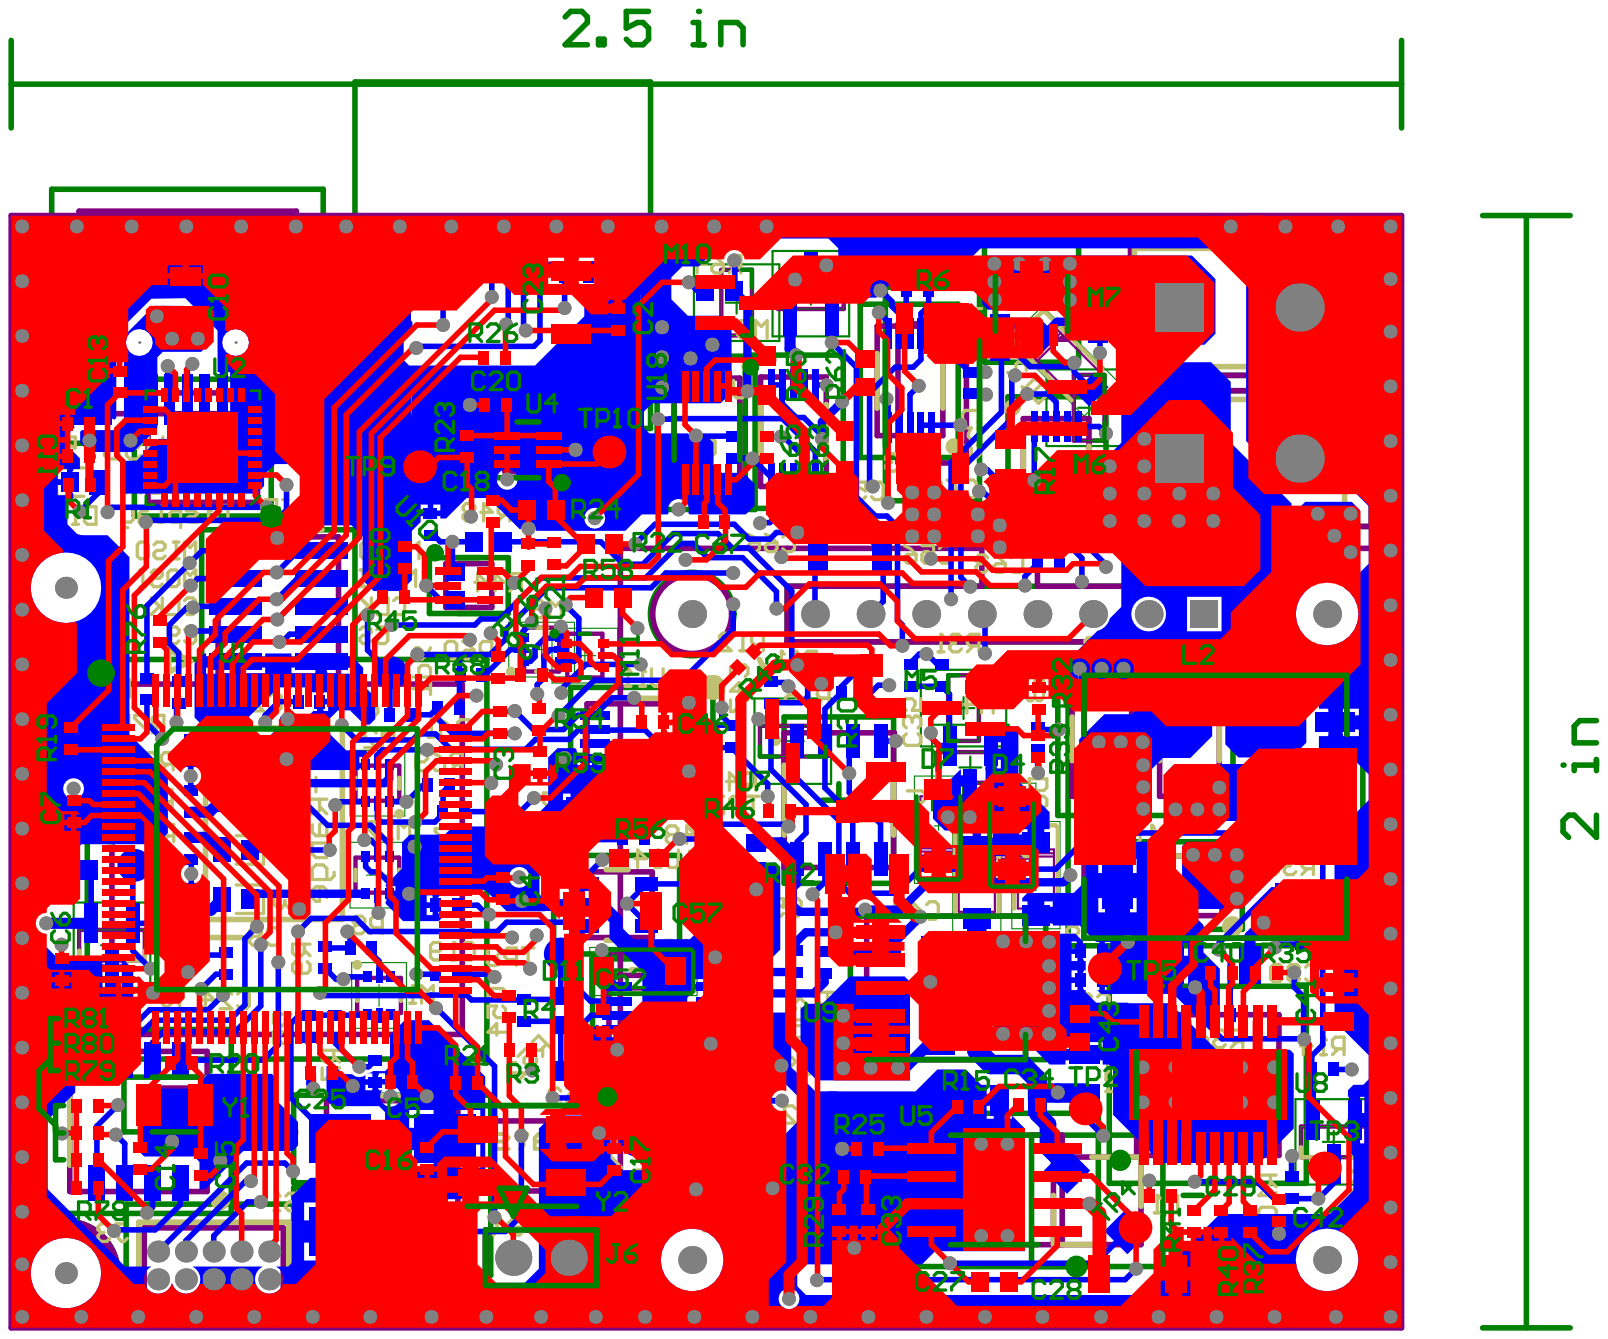
[picture p138: page 7]
