rmfharvey/EE4951_REPO/Simulation/Voltage Measurement Subsystem.asc

C1: cap; 0.015µ; V=16 Irms=777m Rser=0.326249 Lser=0 mfg="KEMET" pn="C0402C153K4RAC" type="X7R"
C2: cap; 0.015µ; V=16 Irms=955m Rser=0.283316 Lser=0 mfg="KEMET" pn="C0402C153K4PAC" type="X5R"
R1: res; 100000
R2: res; 14300
R3: res; 100
U2: LTC1440
U3: OP07
V1: voltage; 24
V2: voltage; 5
V3: voltage; 3.3
Named nets: 0
.tran 0 10sec 5sec 0.12sec
.include "file.txt"
