rmfharvey/EE4951_REPO/Schematics/Power Subsystem/Buck and Boost (Design Version).asc

C1: cap; 10µ
C2: cap; 0.1µ
C4: cap; 100µ
C5: cap; 2.7n
C6: cap; 0.1µ
C7: cap; 33µ
C8: cap; 4.7n
C9: cap; 0.01µ
C11: cap; 2.2µ
C12: cap; 39p
C13: cap; 100n
C14: cap; 4.7µ
C15: cap; 10µ
C16: cap; 10µ
C17: cap; 100µ
C18: cap; 4.7µ
C19: cap; 33µ
D1: zener; 2_5V_Zener
D2: schottky; 1N5817
D3: schottky; 1N5817
D5: schottky; MBRS340
L1: ind; 6.8µ
L2: ind; 6.8µ
M1: pmos; FDC5614P
M2: pmos; FDC5614P
M3: pmos; AO6407
M4: pmos; FDC5614P
M6: nmos; AP9465GEM
M7: nmos; AP9465GEM
R1: res; 1000k
R2: res; 1000k
R3: res; 5k
R4: res; 100k
R5: res; 4.7k
R6: res; 49.9k
R7: res; 10k
R8: res; 100k
R9: res; 50
R10: res; 33
R11: res; 150k
R12: res; 768k
R13: res; 1000k
R14: res; 1.91k
R15: res; 1Meg
R17: res; 5k
R18: res; 390k
R19: res; 1k
R21: res; 10k
R22: res; 100k
U1: LT1018
U2: LP38690_3P3_TRANS
U4: LT1018
U5: TPS61032
U7: TPS54331_TRANS
V1: voltage; 3.5V
V2: voltage; 0V
Named nets: 0, +VCC, Control_1, Control_2, 5V_Rail, 3.3V_Rail, Boost_Out, Boost_In, Buck_Out, Buck_In, 5V_USB, Low_Batt
.tran 3ms uic
.inc "C:\\Users\\James\\Documents\\LT SPICE SIMULATIONS\\MMSZ5222BT1G.txt"
Converter Selection Controls
Loads
3.3V LDO
USB Autotransfer
Buck Converter
Boost Converter
