rmfharvey/EE4951_REPO/Schematics/Power Subsystem/Buck_Boost (Design Version).asc

C1: cap; 10µ
C2: cap; 10µ
C3: cap; 1µ
C4: cap; 1µ
C5: cap; 470n
C6: cap; 4.7n
C7: cap; 4.7n
C8: cap; 4.7µ
C9: cap; 22µ
C10: cap; 22µ
C11: cap; 22µ
C12: cap; 22µ
C13: cap; 22µ
C14: cap; 22µ
C17: cap; 0.1µ
C18: cap; 10µ
C19: cap; 10µ
C20: cap; 100n
D1: schottky; MBRS340
D3: zener; 2_5V_Zener
D4: schottky; 1N5817
D5: schottky; 1N5817
L1: ind; 33µ
M1: pmos
M2: pmos
M5: nmos; AO6408
M7: nmos; AP9465GEM
M8: nmos; AP9465GEM
M9: pmos; FDC5614P
M10: pmos; AO6407
R6: res; 5k
R7: res; 12k
R11: res; 1000k
R14: res; 1000k
R15: res; 1000k
R16: res; 5k
R17: res; 1000k
R18: res; 1k
R19: res; 5k
R20: res; 10k
R21: res; 100k
R22: res; 50
R23: res; 33
R24: res; 100k
R25: res; 4.7k
U1: LT1018
U2: TPIC74100-Q1_TRANS
U3: LTC1516
U6: LT1018
U7: LP38690_3P3_TRANS
V2: voltage; 3.5V
V3: voltage; 0V
Named nets: 0, Buck_Boost_Out, Vout_U2, +VCC, Charge_Pump_Out, Control_1, Control_2, Charge_Pump_Disable, 5V_Rail, 3.3V_Rail, 5V_USB, Charge_Pump_In, Buck_Boost_In
.tran 3ms uic
.inc "C:\\Users\\James\\Documents\\LT SPICE SIMULATIONS\\MMSZ5222BT1G.txt"
Charge Pump Activation Controls
Loads
3.3V LDO
USB Autotransfer
Charge Pump
Buck-Boost Converter
