rmfharvey/EE4951_REPO/Schematics/Current Measurement - Ross/Charge Pump and FET Switch.asc

C1: cap; 1µ
C2: cap; 1µ
C3: cap; 10µ
D1: diode; BAT54
D2: diode; BAT54
D3: diode; BAT54
I1: current; 5m
M1: nmos; 2N7002
M2: nmos; 2N7002
M3: nmos; 2N7002
M4: nmos; 2N7002
M5: pmos; BSS84
M6: nmos; IRFH6200
R1: res; 100R
R2: res; 10k
R3: res; 470R
R4: res; 470R
R5: res; 47R
R6: res; 1k
R7: res; 100R
R8: res; 10k
R9: res; 10k
R10: res; 100R
R11: res; 10k
R12: res; 100k
R13: res; 100k
R14: res; 47R
R15: res; 500m
R16: res; 100R
V1: voltage; 5v
V2: voltage; PULSE(0 5 0 1n 1n 0.5m 1m)
V3: voltage; PULSE(0 3.3v 250m 1n 1n 500m 750m)
Named nets: 0, 5v, pwm, cp3, fet_on, cp1, cp2
.TRAN 0.1u 500m 0
