rmfharvey/EE4951_REPO/Simulation/Power Subsystem/Buck_Boost Design/Buck_Boost (Simulation Version).asc

C1: cap; 1µ
C2: cap; 1µ
C3: cap; 1µ
C4: cap; 1µ
C5: cap; 10n
C9: cap; 1n
C10: cap; 1n
C11: cap; 1n
C12: cap; 1n
C13: cap; 1n
C14: cap; 1n
C15: cap; 1n
C16: cap; 1n
C17: cap; 1µ
D1: zener; KDZ6_2B
D2: schottky; 1N5817
D3: diode
L1: ind; 10µ
M1: pmos; FDC5614P
M2: pmos; FDC5614P
M3: pmos
M4: pmos; FDC5614P
M5: nmos; AP9465GEM
M6: nmos; AP9465GEM
R1: res; 1000k
R2: res; 1000k
R3: res; 5k
R4: res; 15k
R5: res; 10k
R6: res; 750k
R7: res; 250k
R8: res; 100k
R9: res; 50
R10: res; 33
R11: res; 100k
R12: res; 1000k
R13: res; 1000k
R14: res; 2k
R15: res; 3.3k
R16: res; 2k
R17: res; 10k
U1: LT1618
U2: LT1086
U3: LTC1516
U5: LT1366
V1: voltage; PULSE(2V 10V 0s 10ms 10ms 100ms 200ms 10)
Named nets: 0, Vout_U2, +VCC, Vout_U3, Control_1, Control_2, 5V_USB, 5V_Rail, 3.3V_Rail, Control_3
.tran 10ms uic
