rmfharvey/EE4951_REPO/Simulation/Power Subsystem/New Power Switching Simulation/Power_Switching_Simulation_10-24-15.asc

C1: cap; 10p
C2: cap; 0.1µ
C3: cap; 10µ
C4: cap; 1n
C5: cap; 66µ
C6: cap; 4.7µ
C7: cap; 0.1µ
C8: cap; 100µ
C9: cap; 10µ
C10: cap; 0.1µ
D1: schottky; PMEG2010EA
D2: schottky; PMEG2010EA
D3: schottky; PMEG2010EA
D4: schottky; PMEG2010EA
D5: schottky; PMEG2010EA
D6: zener; 1N750
I1: current; 30mA
I2: current; 100mA
M1: pmos; SI3445DV
M2: pmos; SI3445DV
M3: nmos; 2N7002
R1: res; 100k
R2: res; 100k
R3: res; 4.7k
R4: res; 0.1R
R5: res; 12R
R6: res; 1MEG
R7: res; 10k
R8: res; 30k
R9: res; 1MEG
R10: res; 10k
R11: res; 100k
R12: res; 100k
R13: res; 100k
U1: LTC6752
U2: LTC1841
U3: LTC1841
V1: voltage; PWL(0 0v 1m 0v 3m 5v 90m 5v 95m 0v 319m 0v 320m 5v 499.99m 5v 500m 0v)
V2: voltage; PWL(0 0v 99m 0v 100m 5v 190m 5v 195m 0v)
V3: voltage; PWL(0 0v 199m 0v 200m 5v 290m 5v 295m 0v 349.999m 0v 350m 5v 450m 5v 450.001m 0v)
V4: voltage; PWL(0 1.8v 100m 24v)
Named nets: 0, BUCK, BOOST, V5_SUM, 5V, USB, 3.3v, PWR_FAIL_IRQ, Ref, pwr_ref, BAT, BOOST_EN, BUCK_EN, sw-, sw+
0-95ms:        Test V_Buck
100-195ms:  Test V_Boost
200-295ms:  Test V_USB
350ms:         Test USB Switchover
500ms:         Test PWR_FAIL_IRQ
.tran 0 600m 0
USB Autoswitchover
Power Supervisor
PWR_FAIL_IRQ goes low if power has failed
Buck-Boost Switching
