rmfharvey/EE4951_REPO/Simulation/Power Subsystem/Converter Selection Controls Simulation/Converter Selection Controls (Buck and Boost).asc

C1: cap; 10µ
C5: cap; 10µ
D1: zener; 2_5V_Zener
M1: pmos; FDS4435A
M2: pmos; FDS4435A
M6: nmos; FDS4072N3
M7: nmos; FDS4072N3
R1: res; 1000k
R2: res; 1000k
R3: res; 5k
R6: res; 1k
R7: res; 1k
R13: res; 1000k
R17: res; 10k
R19: res; 1k
R21: res; 5k
U1: LT1018
U2: LT1018
V1: voltage; PULSE(4 6 1ms 2ms 2ms 1ms 6ms 2)
Named nets: 0, +VCC, Control_Buck, Control_Boost, Boost_In, Buck_In, Comp+, Comp-
.tran 7ms
.inc "C:\\Users\\James\\Documents\\LT SPICE SIMULATIONS\\MMSZ5222BT1G.txt"
