rmfharvey/EE4951_REPO/Simulation/Power Subsystem/Converter Selection Controls Simulation/Converter Selection Controls (Buck-Boost).asc

C1: cap; 10µ
C2: cap; 0.1µ
C5: cap; 10µ
D1: zener; 2_5V_Zener
M1: pmos; FDS4435A
M2: pmos; FDS4435A
M3: nmos; SI2316DS-T1-E3
M6: nmos; SI2316DS-T1-E3
M7: nmos; SI2316DS-T1-E3
R1: res; 1000k
R2: res; 1000k
R3: res; 5k
R4: res; 1Meg
R6: res; 1k
R7: res; 1k
R13: res; 1Meg
R17: res; 10k
R19: res; 1k
R21: res; 5k
U1: LT1018
U2: LT1018
V1: voltage; PULSE(0 2 1ms 10ms 10ms 1s 2s 2)
V2: voltage; PULSE(0 5 0.1s 1us 1us 2s 20s 2)
Named nets: 0, +VCC, Control_Buck_Boost, Control_Charge_Pump, Charge_Pump_In, Buck_Boost_In, Comp+, Comp-, Auto_Off
.tran 0.2s
.inc "C:\\Users\\James\\Documents\\LT SPICE SIMULATIONS\\MMSZ5222BT1G.txt"
.inc "C:\\Users\\James\\Documents\\LT SPICE SIMULATIONS\\SI2316DS-T1-E3.txt"
