rmfharvey/EE4951_REPO/Simulation/Power Subsystem/USB Autotransfer/5V USB Autotransfer.asc

C1: cap; 100n
C5: cap; 1µ
D1: schottky; 1N5817
D2: schottky; 1N5817
M1: pmos; AO6407
M2: pmos; FDS4435A
R1: res; 100k
R2: res; 100k
R3: res; 4.7k
R6: res; 100
V1: voltage; 5
V2: voltage; PULSE(0 5 1us 1us 1us 1ms 2ms 5)
Named nets: +VCC, 5V_USB, 0, 5V_Rail, USB_IN
.tran 5ms
