rmfharvey/EE4951_REPO/Firmware/Production/ee4951_prodmcu/Sources/DutVSense.cpp

/*
 * DutVSense.cpp
 *
 *  Created on: Dec 6, 2015
 *      Author: RossHarvey
 */

/*
 * This is almost the same as the DutISense class, but much simpler since there are no ranges to deal with.
 * It should be easy to figure out without more comments
 */


#include <DutVSense.h>


DutVSense::DutVSense() {
	scalingFactor = 0.0003601245;
	adcChConfig = dut_vsense;
}

void DutVSense::updateADCVal(void)	{
	ADC16_DRV_ConfigConvChn(dut_adc_IDX, SELFADC_CHNGROUP, &adcChConfig);
	rawADCVal = ADC16_DRV_GetConvValueRAW(dut_adc_IDX, SELFADC_CHNGROUP);
	floatADCVal.asFloat = (float)rawADCVal*scalingFactor;
}

uint16_t DutVSense::getADCValRaw(void)	{
	return rawADCVal;
}

floatUnion_t DutVSense::getADCValScaled(void)	{
	return floatADCVal;
}
